lehungthinh02/KLTN_Data/Flowchart/KLTN_Data Diagram.png

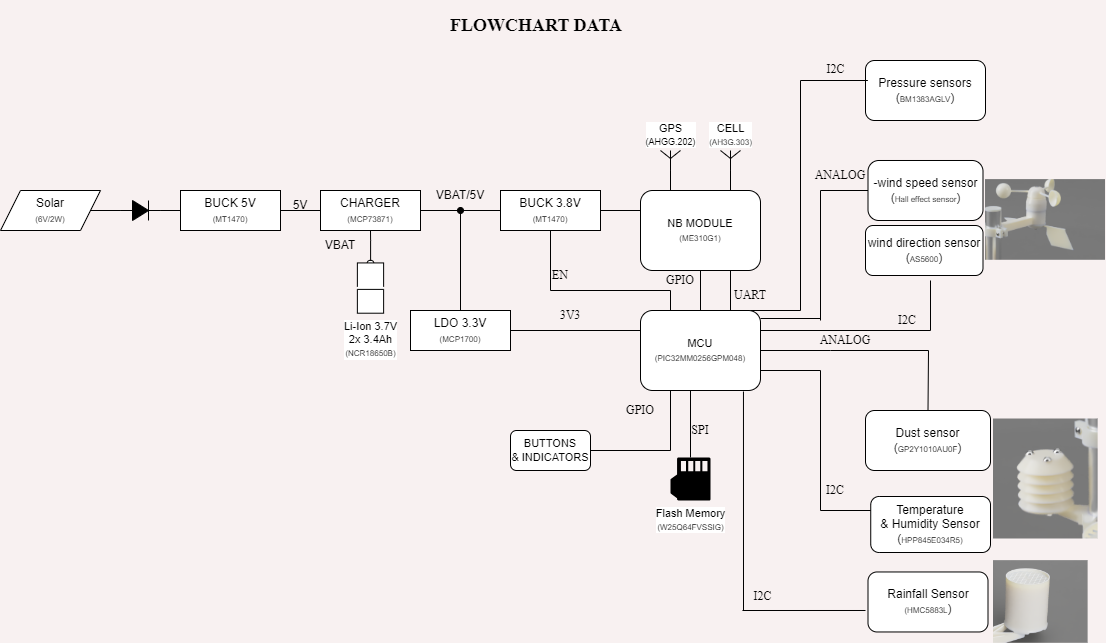
Flowchart/KLTN_Data Diagram.png
