lehungthinh02/KLTN_Data/Hardware/KiCADLib/FootprintConfig.png

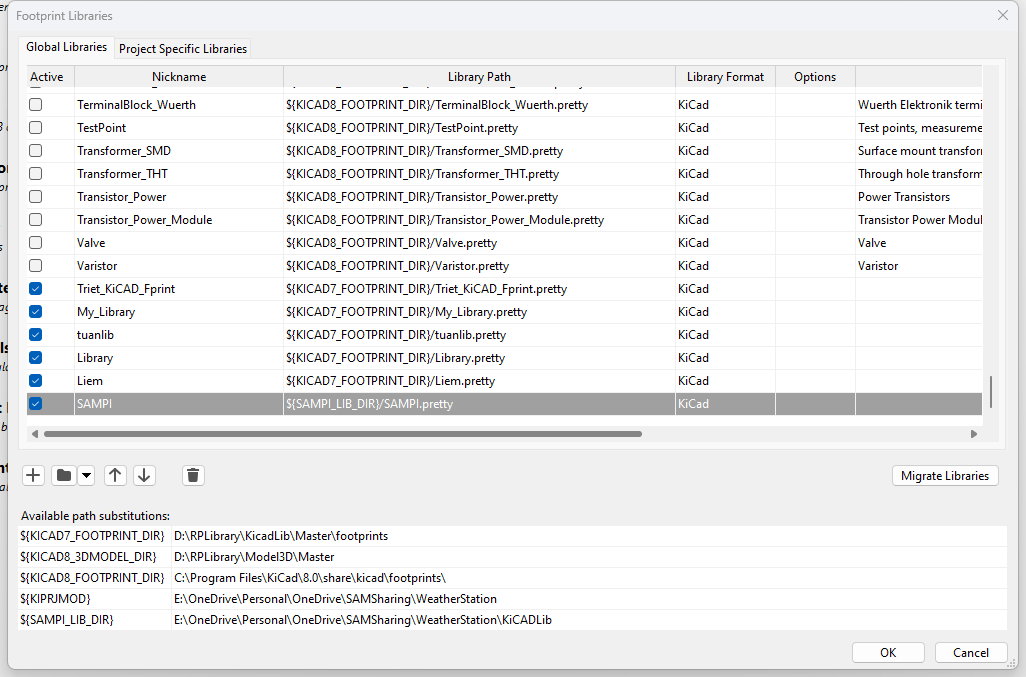
Hardware/KiCADLib/FootprintConfig.png
