lehungthinh02/KLTN_Data/Hardware/KiCADLib/PathConfig.png

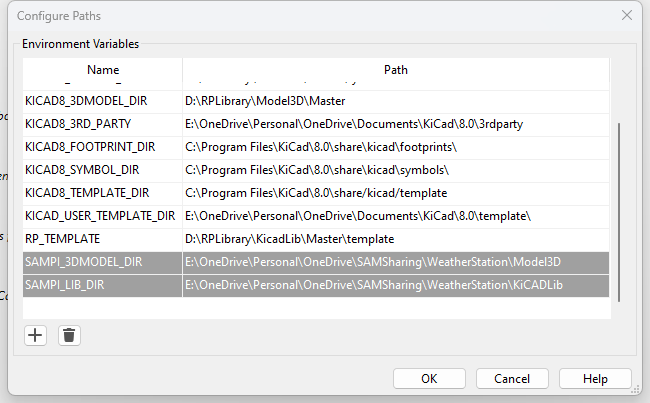
Hardware/KiCADLib/PathConfig.png
