lehungthinh02/KLTN_Data/Hardware/KiCADLib/SymbolConfig.png

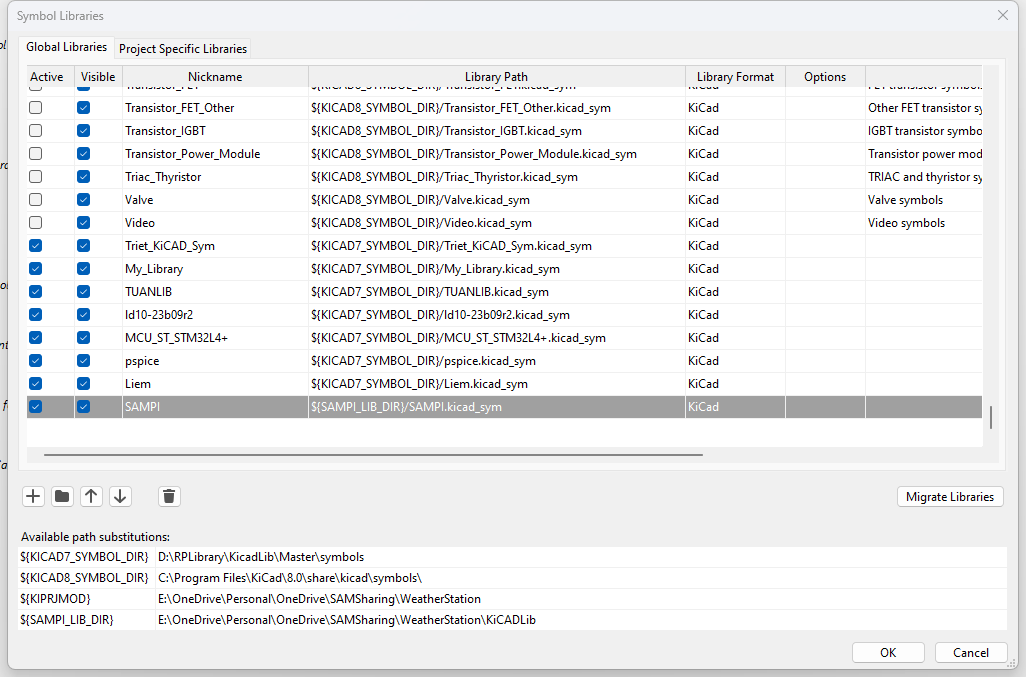
Hardware/KiCADLib/SymbolConfig.png
