lehungthinh02/KLTN_Data/Hardware/Enclosure/files/Anemo_top_-_Cap.stl

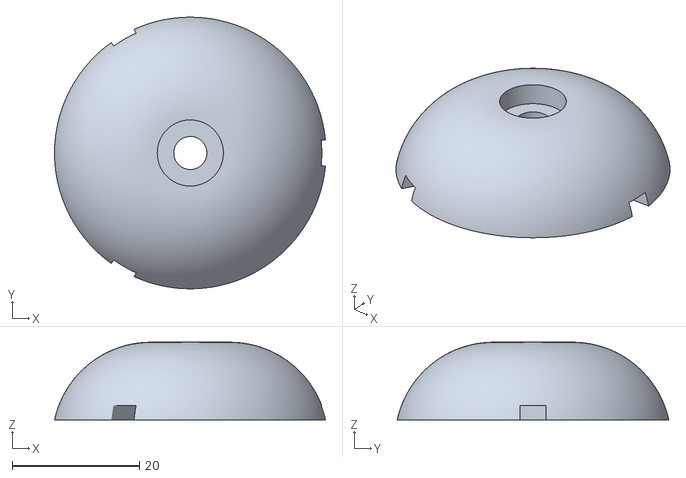
[picture p27: CAD file, 2024-04-03]
Hardware/Enclosure/files/Anemo_top_-_Cap.stl
42.6 x 42.7 x 12.2
