lehungthinh02/KLTN_Data/Hardware/Model3D/0612R.step

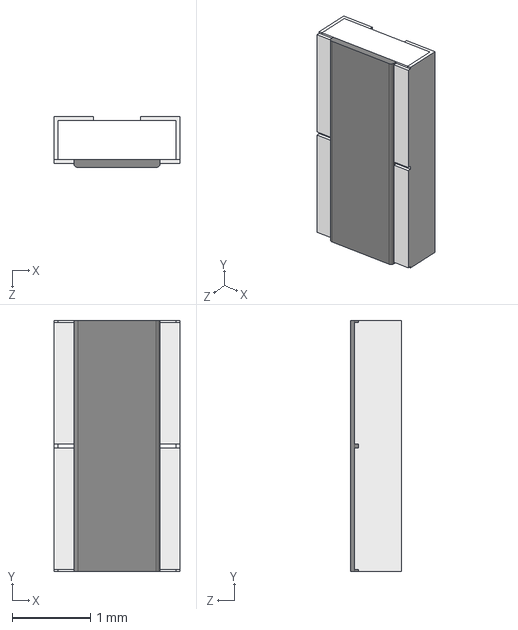
[picture p28: CAD file, 2024-04-12]
Hardware/Model3D/0612R.step
1.60 x 3.20 x 0.65 mm
