lehungthinh02/KLTN_Data/Hardware/Enclosure/files/Anemo_top_-_Wind_bowl.stl

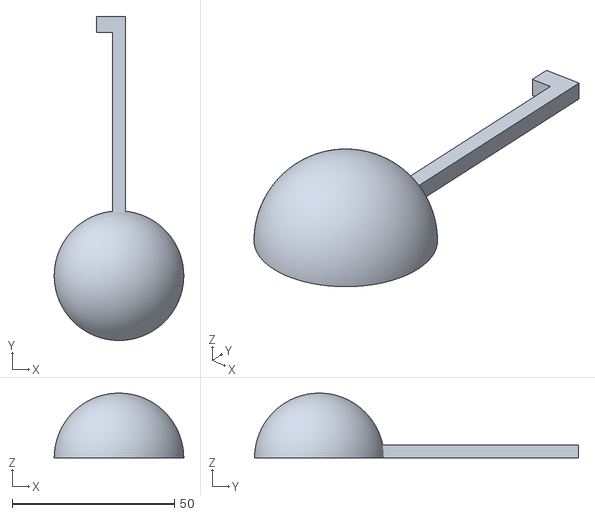
[picture p29: CAD file, 2024-04-03]
Hardware/Enclosure/files/Anemo_top_-_Wind_bowl.stl
40.0 x 100.0 x 20.0
