lehungthinh02/KLTN_Data/Hardware/Model3D/115v-ad00_c_1.stp

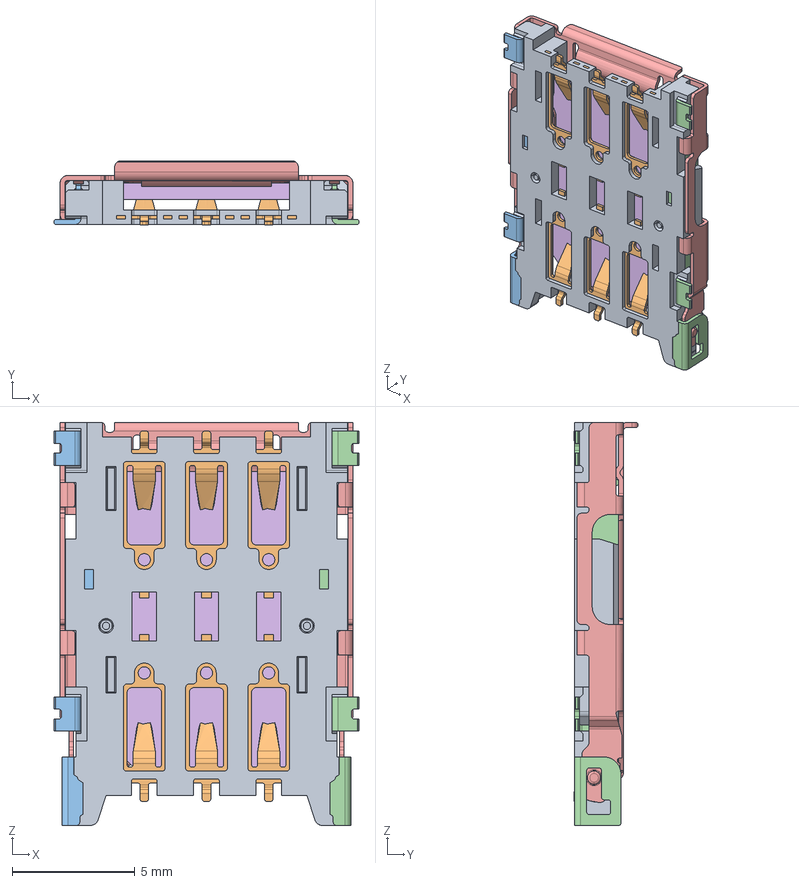
[picture p30: CAD file, 2024-04-12]
Hardware/Model3D/115v-ad00_c_1.stp
12.4 x 2.62 x 16.4 mm
INSULATOR
MICRO_SIM_CONTACT_01_19 x 3
MICRO_SIM_CONTACT_01_MIR_15 x 3
GROUND-LEFT
GROUND-RIGHT
NANO_SIM_CARD_2
