lehungthinh02/KLTN_Data/Hardware/Enclosure/files/Pluvio_sensor_Hub.stl

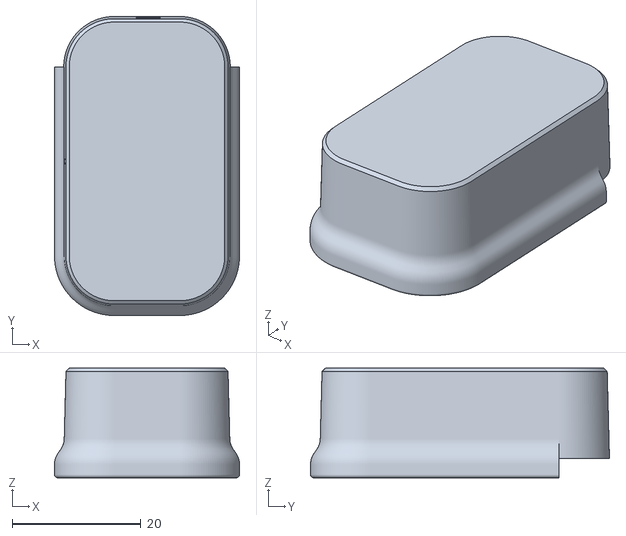
[picture p31: CAD file, 2024-04-03]
Hardware/Enclosure/files/Pluvio_sensor_Hub.stl
28.7 x 46.4 x 17.0
