lehungthinh02/KLTN_Data/Hardware/Model3D/EKMQ401VSN561MA40S.step

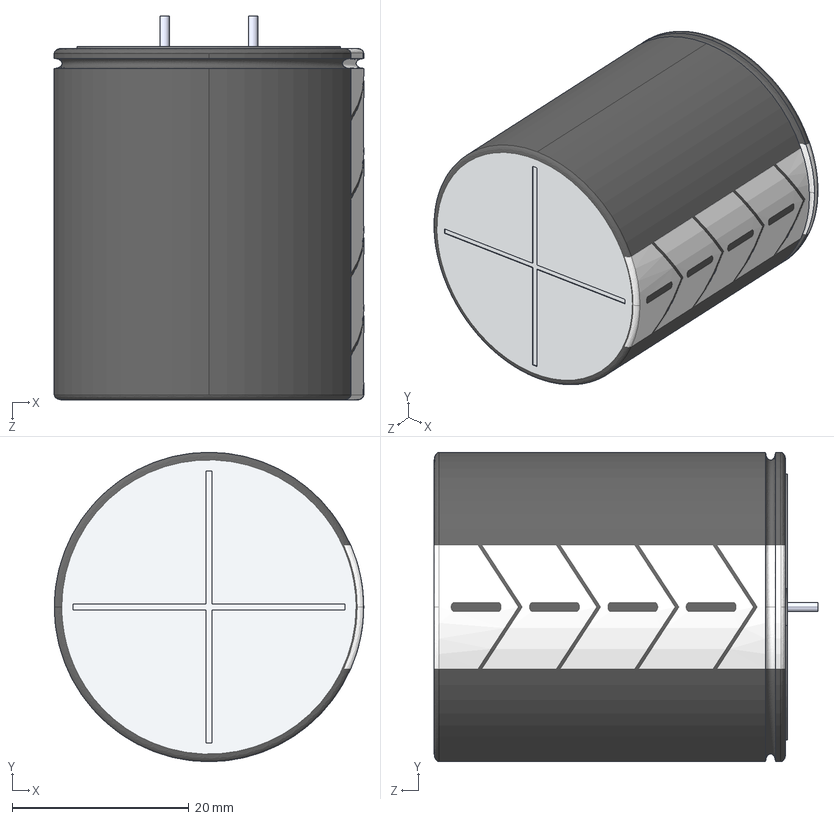
[picture p32: CAD file, 2024-04-12]
Hardware/Model3D/EKMQ401VSN561MA40S.step
35.0 x 35.0 x 43.4 mm
