lehungthinh02/KLTN_Data/Hardware/Enclosure/files/Anemo_Backpole.stl

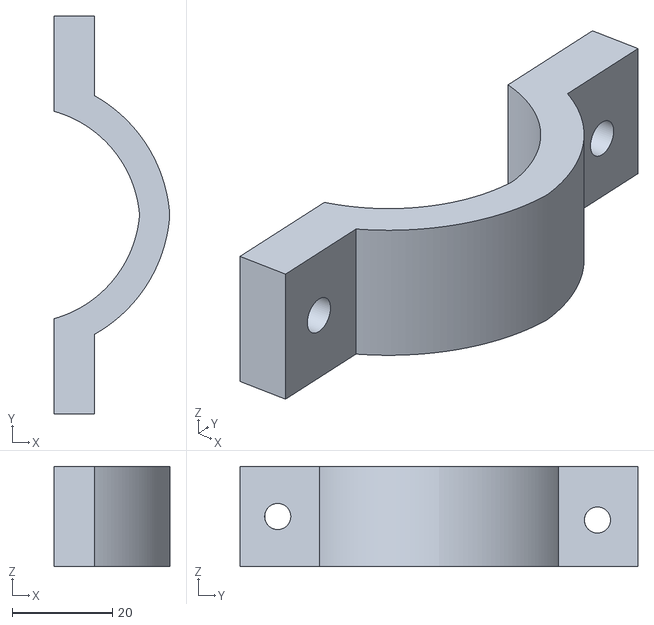
[picture p33: CAD file, 2024-04-03]
Hardware/Enclosure/files/Anemo_Backpole.stl
23.0 x 79.3 x 20.0
