lehungthinh02/KLTN_Data/Hardware/Model3D/C15DBAN.STEP

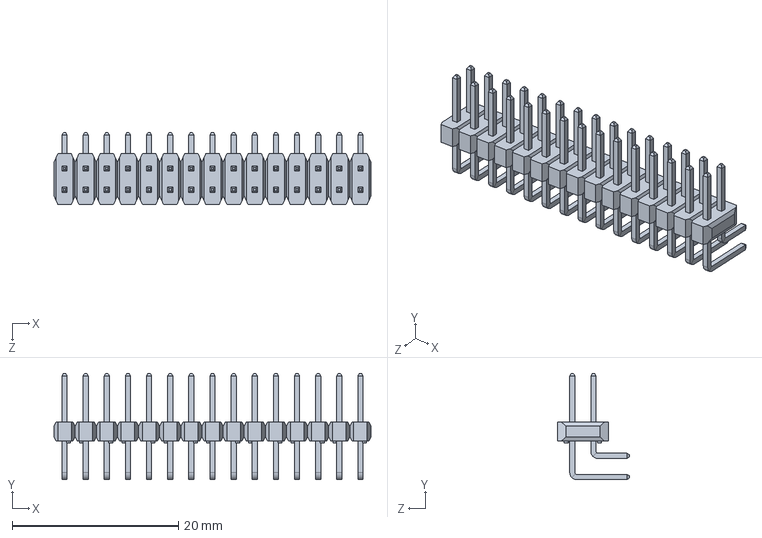
[picture p34: CAD file, 2024-04-12]
Hardware/Model3D/C15DBAN.STEP
38.1 x 12.8 x 8.64 mm
