lehungthinh02/KLTN_Data/Hardware/Enclosure/files/SH-First.stl

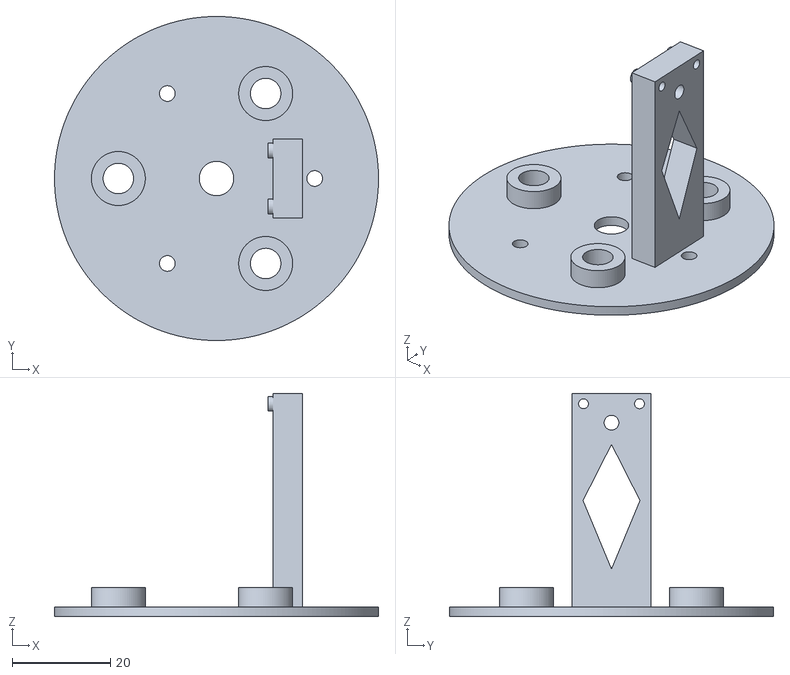
[picture p35: CAD file, 2024-04-03]
Hardware/Enclosure/files/SH-First.stl
66.0 x 66.0 x 45.5
