lehungthinh02/KLTN_Data/Hardware/Model3D/RES0603.STEP

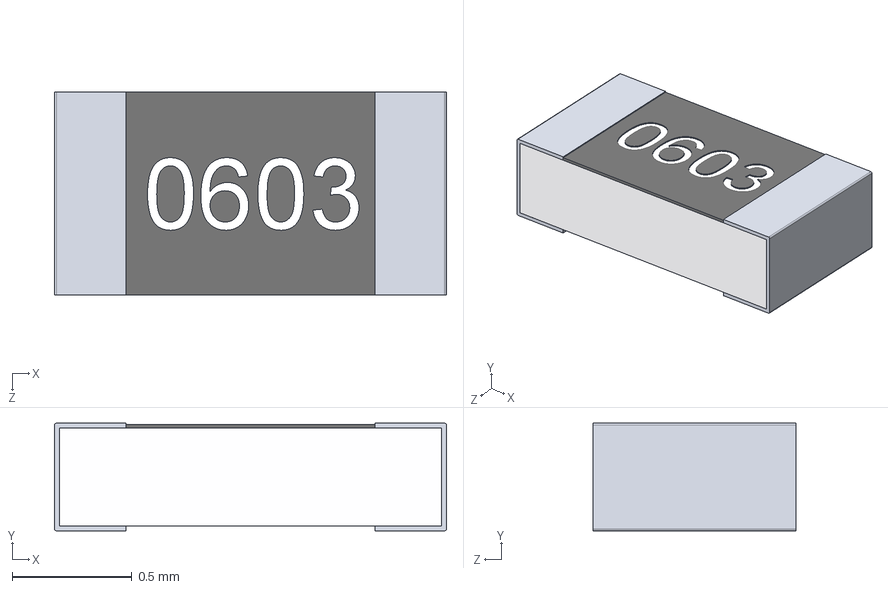
[picture p36: CAD file, 2024-04-12]
Hardware/Model3D/RES0603.STEP
1.64 x 0.45 x 0.85 mm
User Library-R SMD 0603_0603 BODY
User Library-R SMD 0603_0603 PAD x 2
User Library-R SMD 0603_0603 OPIS
