lehungthinh02/KLTN_Data/Hardware/Enclosure/files/Anemo_bottom-Base.stl

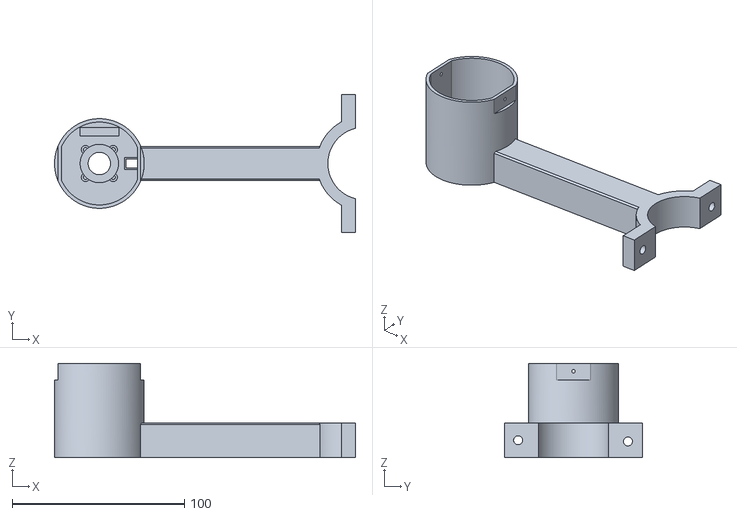
[picture p37: CAD file, 2024-04-03]
Hardware/Enclosure/files/Anemo_bottom-Base.stl
174.5 x 80.0 x 54.5
