lehungthinh02/KLTN_Data/Hardware/Model3D/1210C.step

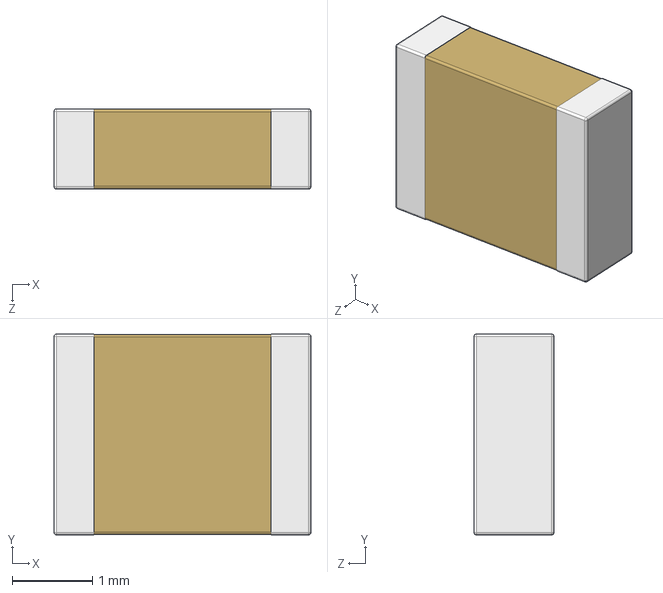
[picture p38: CAD file, 2024-04-12]
Hardware/Model3D/1210C.step
3.20 x 2.50 x 1.00 mm
