lehungthinh02/KLTN_Data/Hardware/Enclosure/files/Pluvio_Case.stl

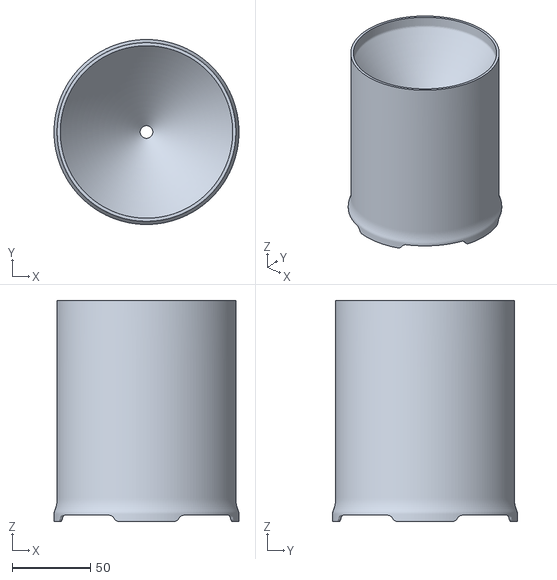
[picture p39: CAD file, 2024-04-03]
Hardware/Enclosure/files/Pluvio_Case.stl
118.0 x 118.0 x 141.0
