lehungthinh02/KLTN_Data/Hardware/Model3D/DF30FC-24DS-0.4V(82).stp

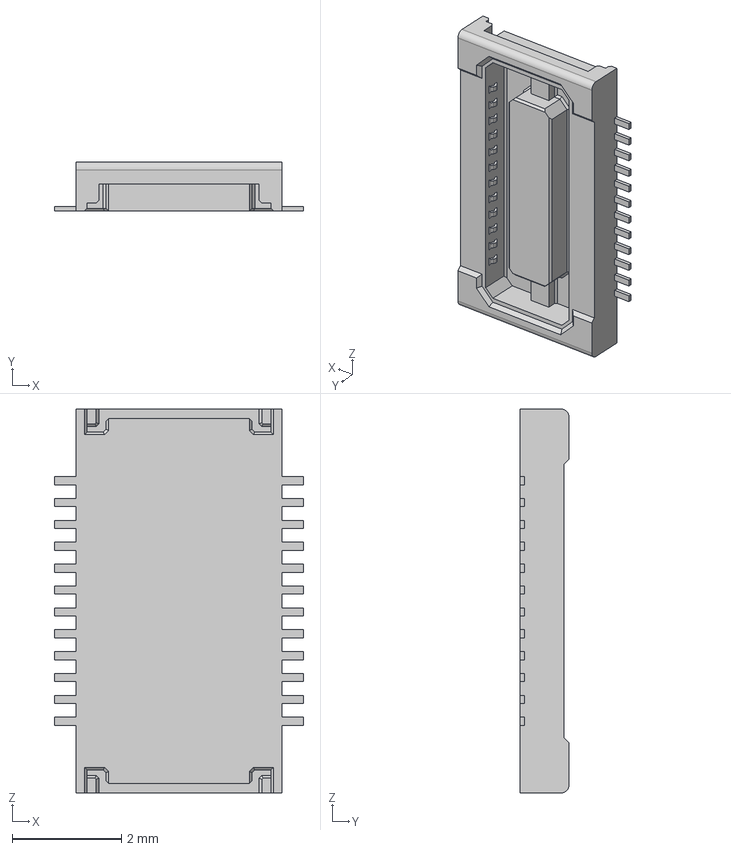
[picture p40: CAD file, 2024-04-12]
Hardware/Model3D/DF30FC-24DS-0.4V(82).stp
4.56 x 0.9 x 7.02 mm
