lehungthinh02/KLTN_Data/Hardware/Enclosure/files/SH-DHT_holder.stl

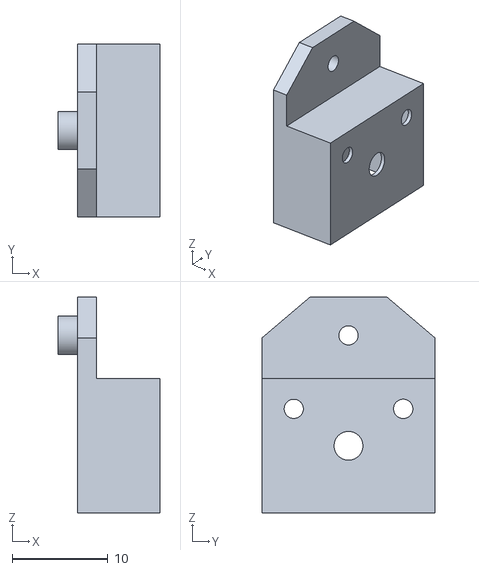
[picture p41: CAD file, 2024-04-03]
Hardware/Enclosure/files/SH-DHT_holder.stl
10.6 x 18.0 x 22.5
