lehungthinh02/KLTN_Data/Hardware/Model3D/C0603C104K4RACTU.step

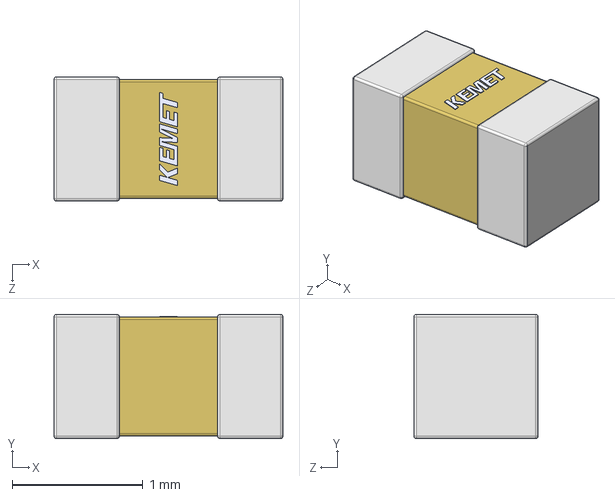
[picture p42: CAD file, 2024-04-12]
Hardware/Model3D/C0603C104K4RACTU.step
1.75 x 0.95 x 0.95 mm
