lehungthinh02/KLTN_Data/Hardware/Model3D/CONN 2M 22035025.stp

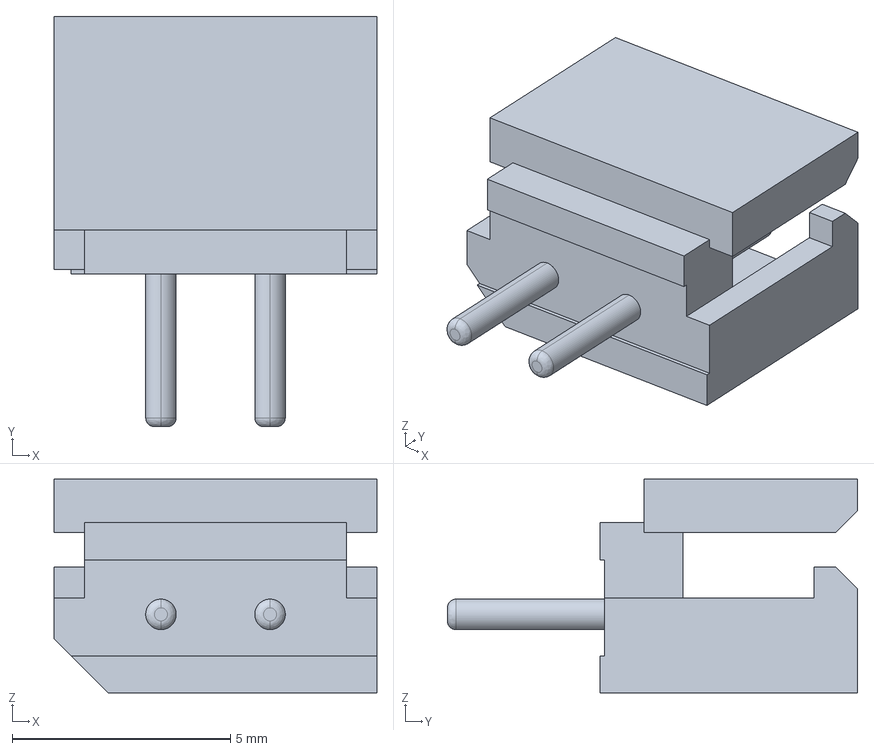
[picture p43: CAD file, 2024-04-12]
Hardware/Model3D/CONN 2M 22035025.stp
7.40 x 9.40 x 4.90 mm
