lehungthinh02/KLTN_Data/Hardware/Enclosure/files/Sensor_Hub_Backpole.stl

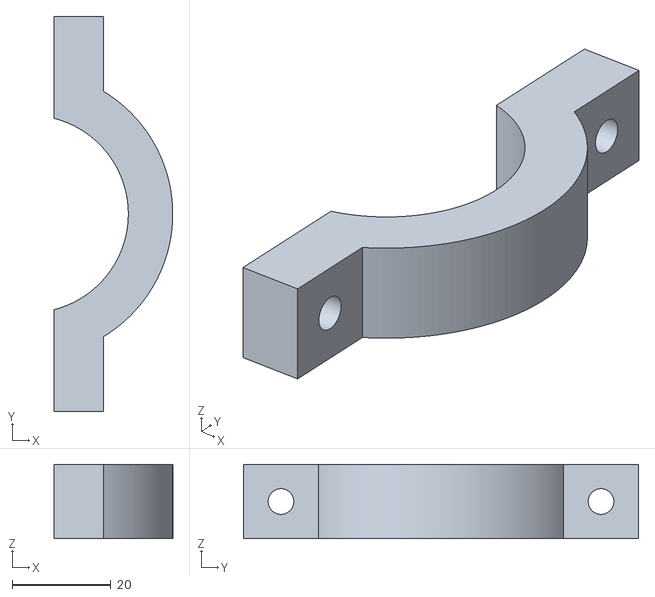
[picture p44: CAD file, 2024-04-03]
Hardware/Enclosure/files/Sensor_Hub_Backpole.stl
24.0 x 80.0 x 15.0
