lehungthinh02/KLTN_Data/Hardware/Model3D/SOP65P640X120-8N.step

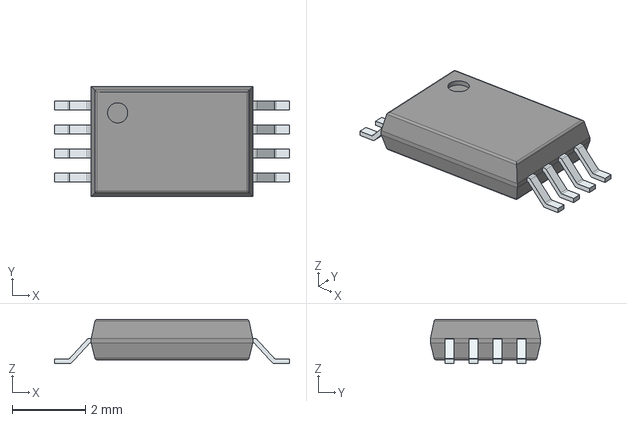
[picture p45: CAD file, 2024-04-12]
Hardware/Model3D/SOP65P640X120-8N.step
6.40 x 3.00 x 1.20 mm
PinsArrayLR
