lehungthinh02/KLTN_Data/Hardware/Enclosure/files/Pluvio-Backpole_V2.stl

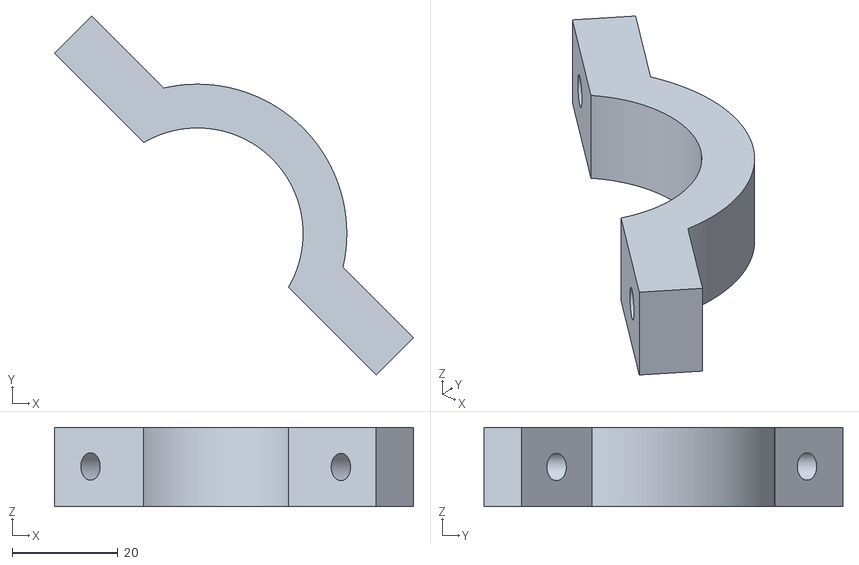
[picture p46: CAD file, 2024-04-03]
Hardware/Enclosure/files/Pluvio-Backpole_V2.stl
68.0 x 68.0 x 15.0
