lehungthinh02/KLTN_Data/Hardware/Model3D/QFN50P400X400X80-25N-D.step

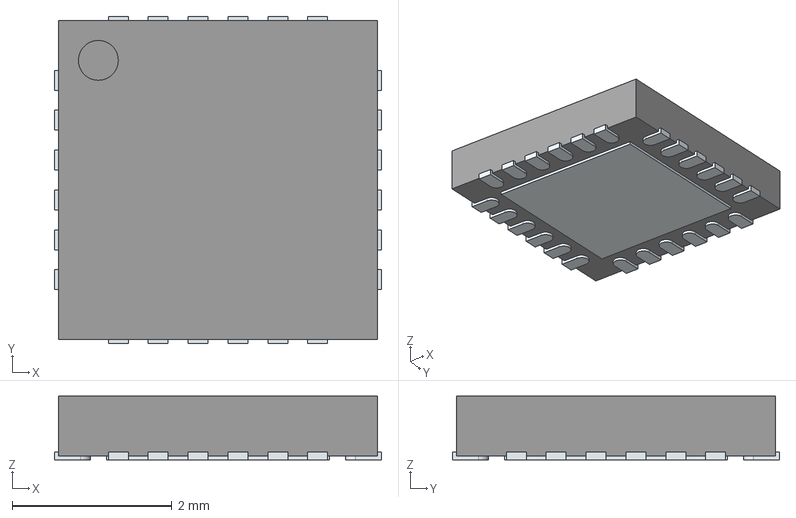
[picture p47: CAD file, 2024-04-12]
Hardware/Model3D/QFN50P400X400X80-25N-D.step
4.10 x 4.10 x 0.8 mm
ThermalPin
PinsArrayLR
PinsArrayTB
