lehungthinh02/KLTN_Data/Hardware/Enclosure/files/Sensor_Hub_Holder.stl

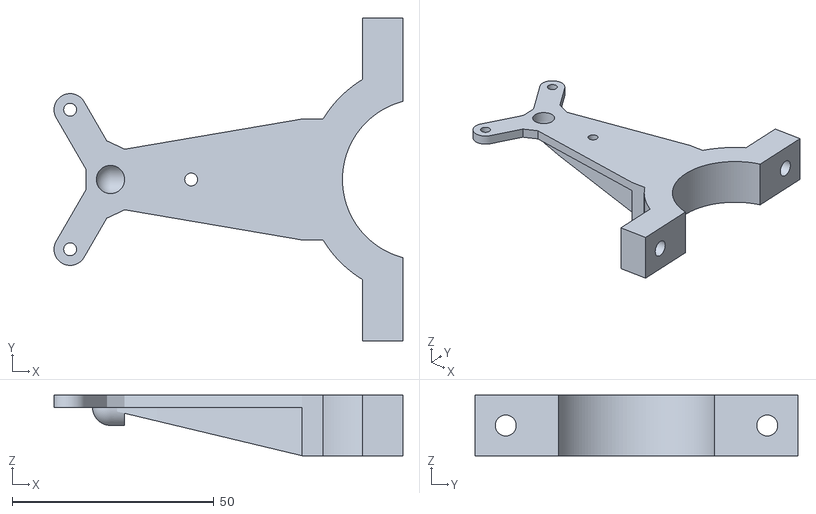
[picture p48: CAD file, 2024-04-03]
Hardware/Enclosure/files/Sensor_Hub_Holder.stl
86.5 x 80.0 x 15.0
