lehungthinh02/KLTN_Data/Hardware/Model3D/LED_0603_WS.STEP

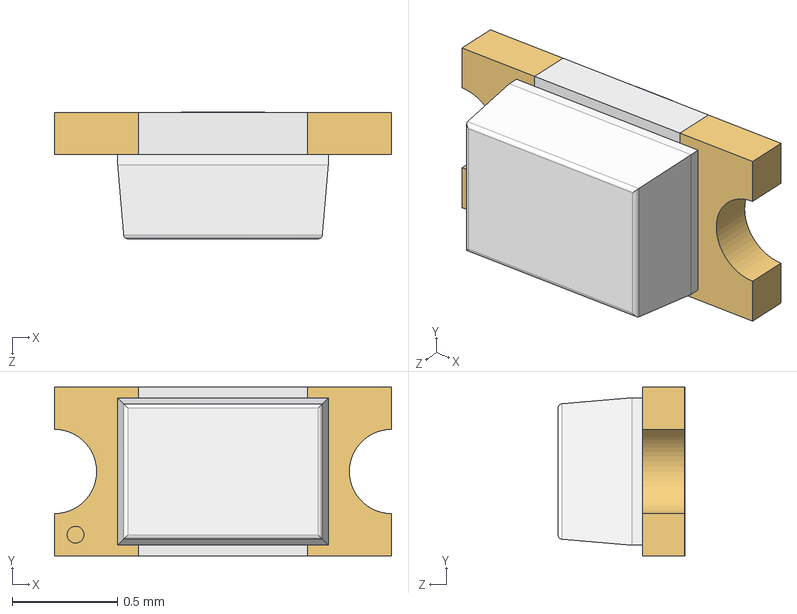
[picture p49: CAD file, 2024-04-12]
Hardware/Model3D/LED_0603_WS.STEP
1.60 x 0.8 x 0.602 mm
User Library-LED_0603_WS_Pocket002
User Library-LED_0603_WS_Pad004
User Library-LED_0603_WS_Fillet
User Library-LED_0603_WS_Pocket001
User Library-LED_0603_WS_Pad
