lehungthinh02/KLTN_Data/Hardware/Enclosure/files/Anemo_bottom-Low_cap_FIXED.stl

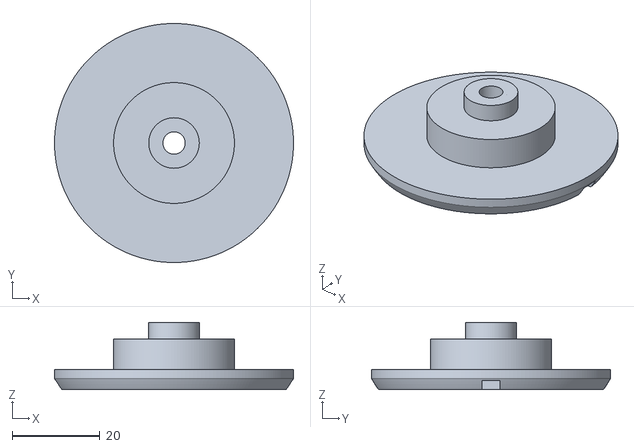
[picture p50: CAD file, 2024-04-03]
Hardware/Enclosure/files/Anemo_bottom-Low_cap_FIXED.stl
54.4 x 54.4 x 15.4
