lehungthinh02/KLTN_Data/Hardware/Model3D/mps_mag_4600.STEP

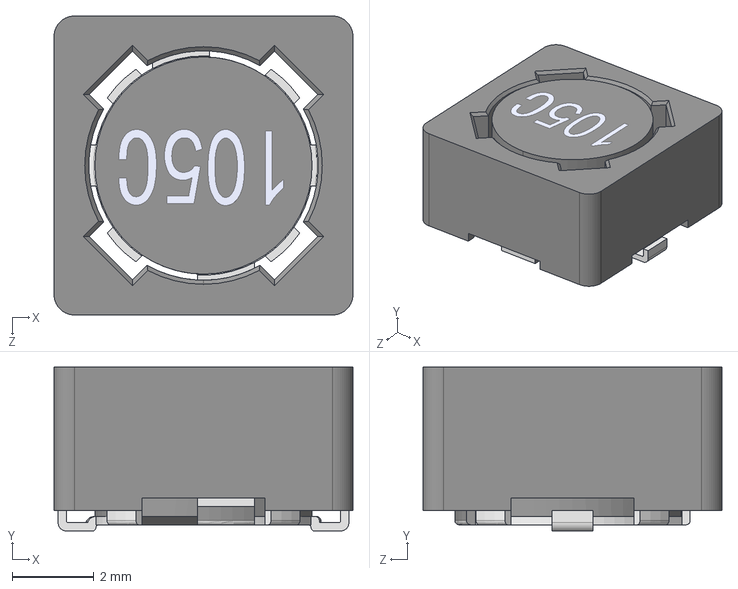
[picture p51: CAD file, 2024-04-12]
Hardware/Model3D/mps_mag_4600.STEP
7.30 x 4.00 x 7.30 mm
