lehungthinh02/KLTN_Data/Hardware/Enclosure/files/Pluvio_-_Base_FIXED.stl

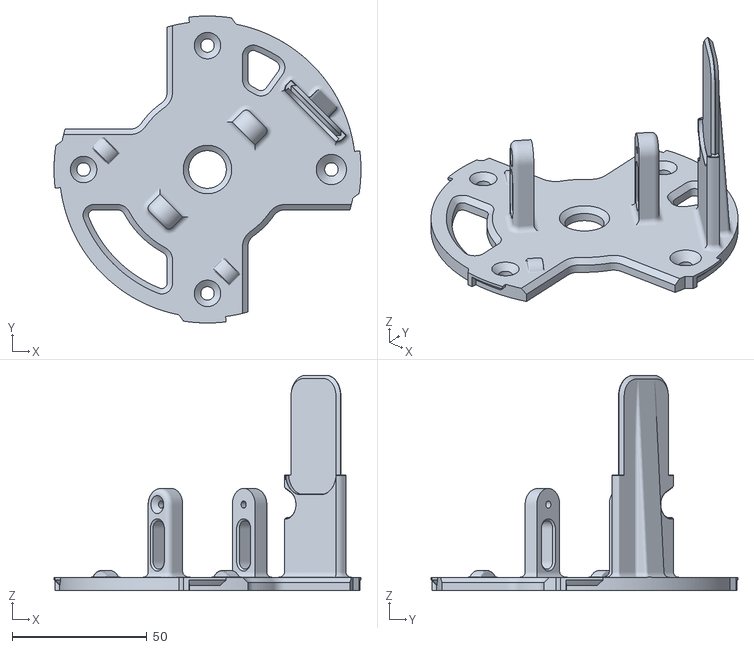
[picture p52: CAD file, 2024-04-03]
Hardware/Enclosure/files/Pluvio_-_Base_FIXED.stl
114.0 x 114.0 x 80.0
