lehungthinh02/KLTN_Data/Hardware/Model3D/A768MS477M1ELAE017.step

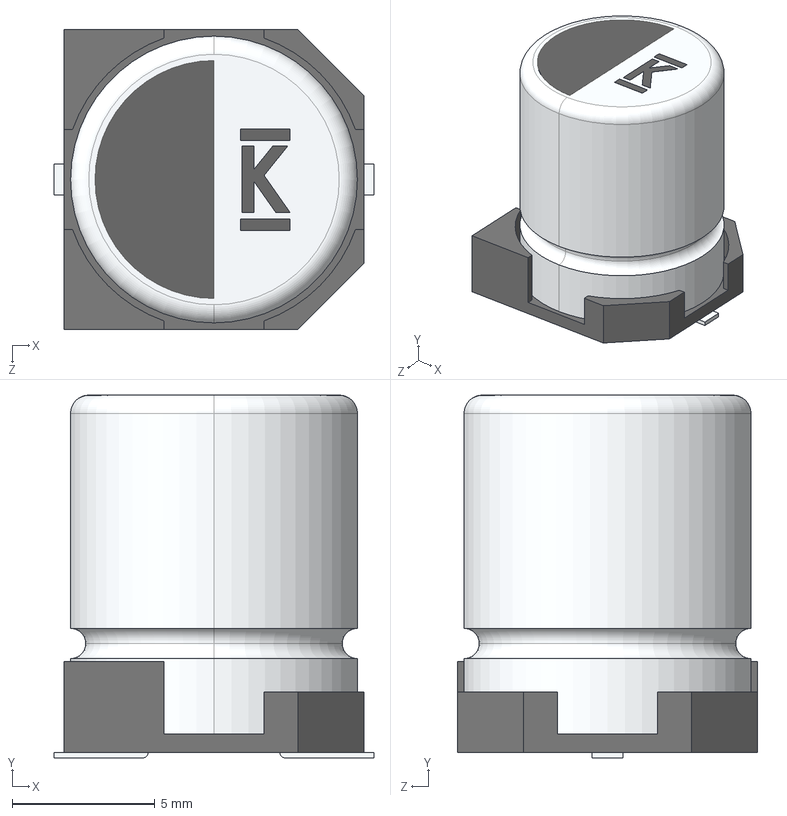
[picture p53: CAD file, 2024-04-12]
Hardware/Model3D/A768MS477M1ELAE017.step
11.2 x 12.7 x 10.5 mm
