lehungthinh02/KLTN_Data/Hardware/Enclosure/files/Sensor_Hub_Shield_top.stl

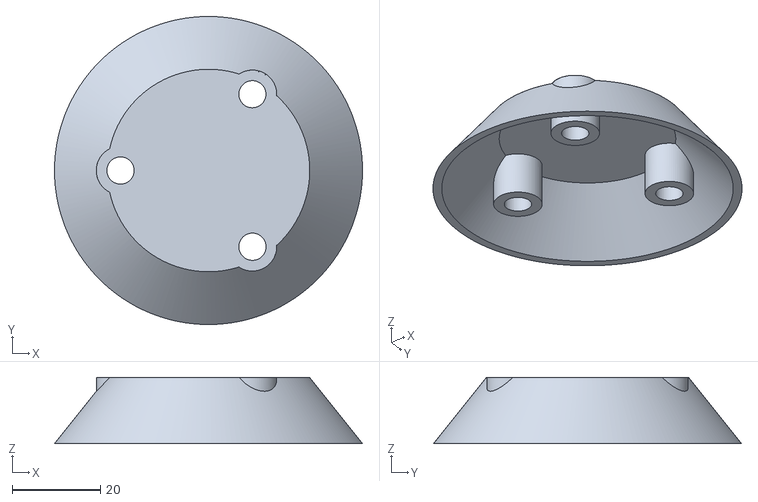
[picture p54: CAD file, 2024-04-03]
Hardware/Enclosure/files/Sensor_Hub_Shield_top.stl
70.0 x 70.0 x 15.0
