lehungthinh02/KLTN_Data/Hardware/Model3D/SCap_DGH155Q5R5_modified.STEP

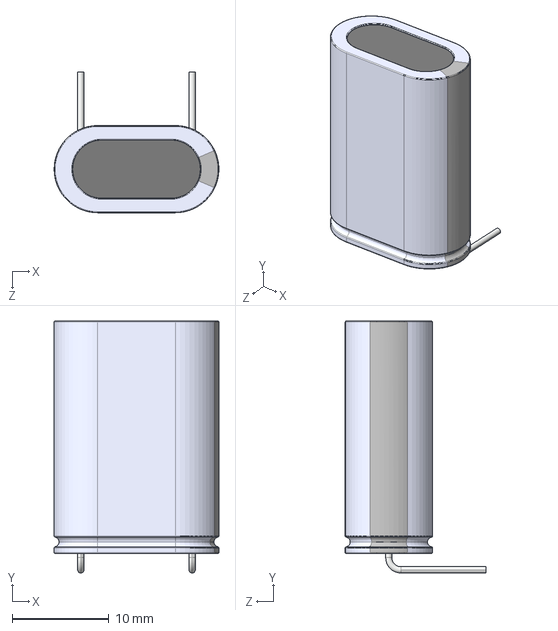
[picture p55: CAD file, 2024-04-12]
Hardware/Model3D/SCap_DGH155Q5R5_modified.STEP
17.0 x 26.0 x 14.5 mm
