lehungthinh02/KLTN_Data/Hardware/Model3D/DPS368.step

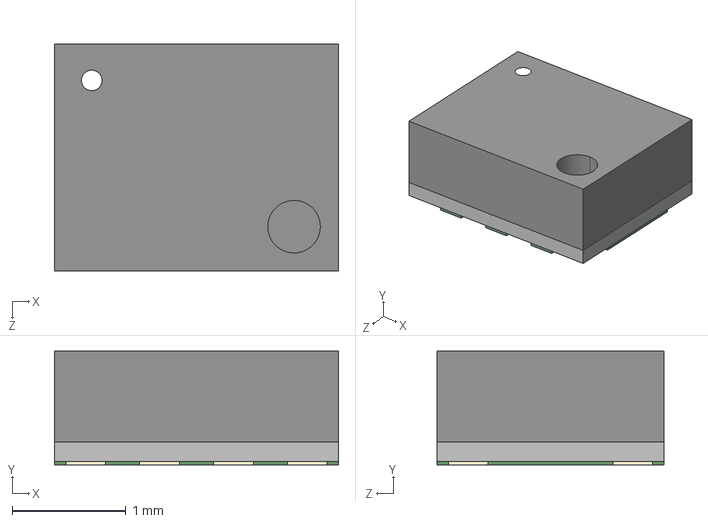
[picture p56: CAD file, 2024-04-12]
Hardware/Model3D/DPS368.step
2.50 x 1.00 x 2.00 mm
