lehungthinh02/KLTN_Data/Hardware/Enclosure/files/Pluvio_-_Tipping_bucket_FIXED.stl

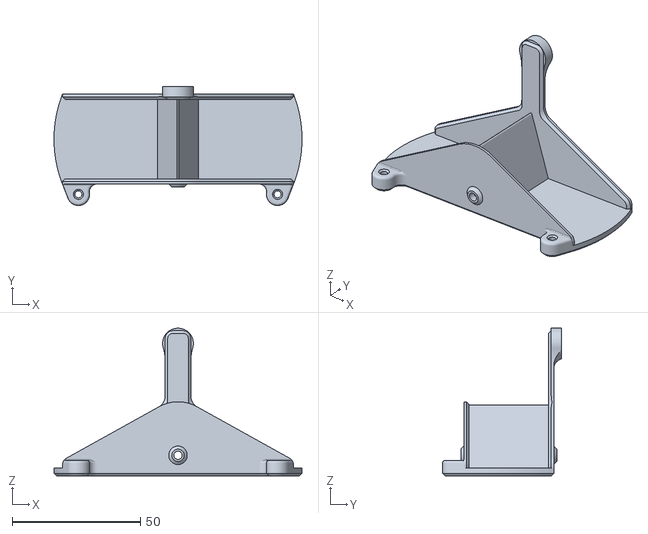
[picture p57: CAD file, 2024-04-03]
Hardware/Enclosure/files/Pluvio_-_Tipping_bucket_FIXED.stl
96.6 x 46.3 x 57.5
