lehungthinh02/KLTN_Data/Hardware/Model3D/QUECTEL L76.step

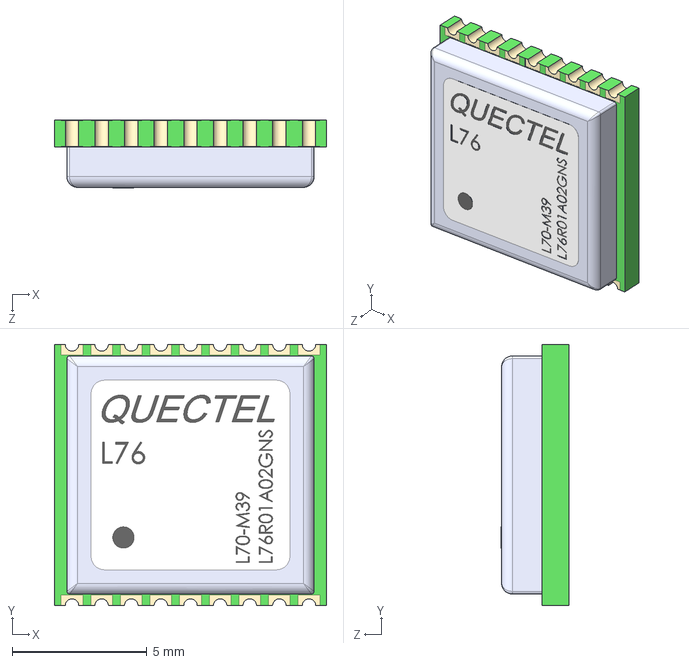
[picture p58: CAD file, 2024-04-12]
Hardware/Model3D/QUECTEL L76.step
10.1 x 9.70 x 2.52 mm
