lehungthinh02/KLTN_Data/Hardware/Enclosure/files/Anemo_bottom-High_cap_FIXED.stl

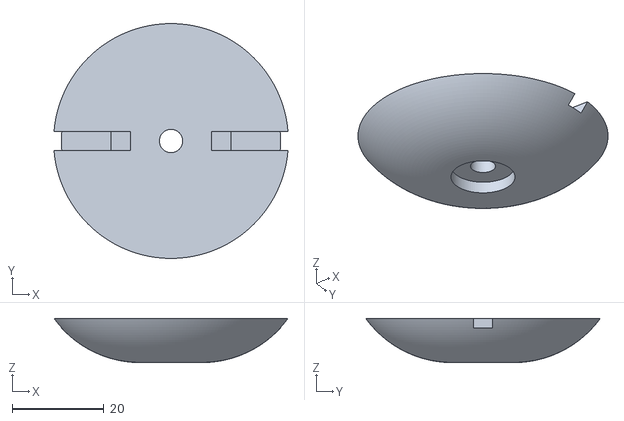
[picture p59: CAD file, 2024-04-03]
Hardware/Enclosure/files/Anemo_bottom-High_cap_FIXED.stl
51.0 x 51.2 x 9.64
