lehungthinh02/KLTN_Data/Hardware/Model3D/SOT65P210X110-6N.step

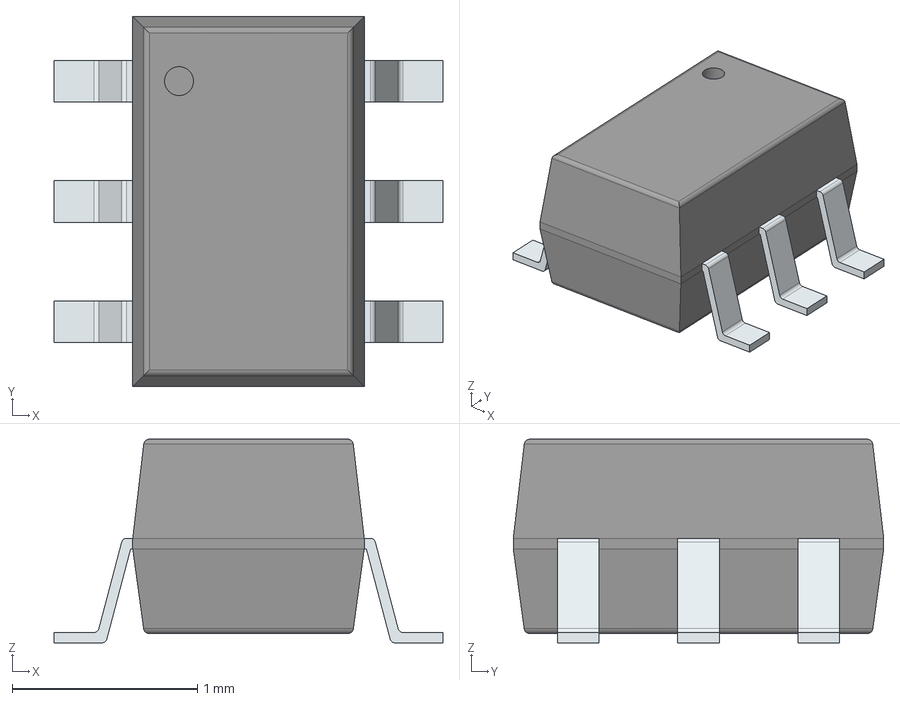
[picture p60: CAD file, 2024-04-12]
Hardware/Model3D/SOT65P210X110-6N.step
2.10 x 2.00 x 1.10 mm
PinsArrayLR
