lehungthinh02/KLTN_Data/Hardware/Model3D/mf-nsmf050.stp

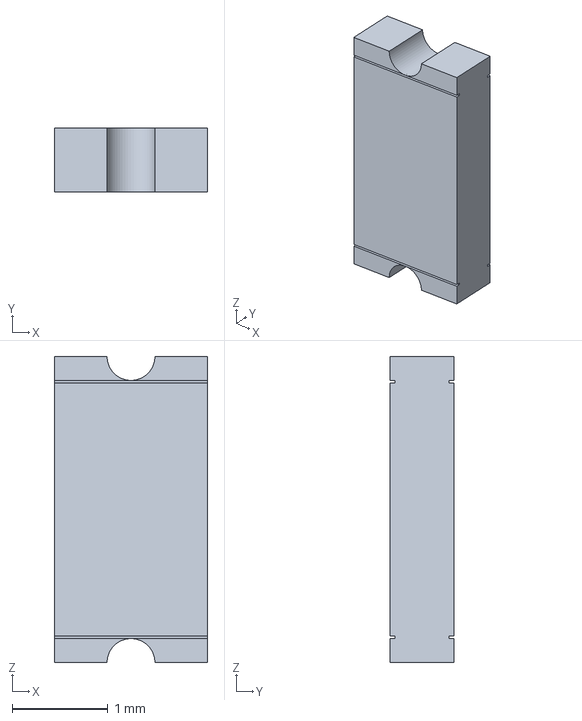
[picture p61: CAD file, 2024-04-12]
Hardware/Model3D/mf-nsmf050.stp
1.60 x 0.665 x 3.20 mm
