lehungthinh02/KLTN_Data/Hardware/Model3D/APTB1612.STEP

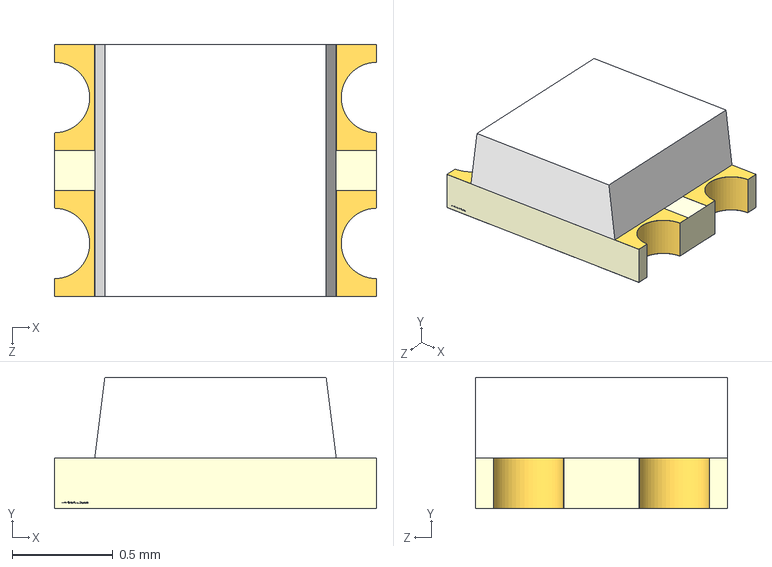
[picture p62: CAD file, 2024-04-12]
Hardware/Model3D/APTB1612.STEP
1.60 x 0.651 x 1.25 mm
