lehungthinh02/KLTN_Data/Hardware/Model3D/CI1104MXHR0-NH.STEP

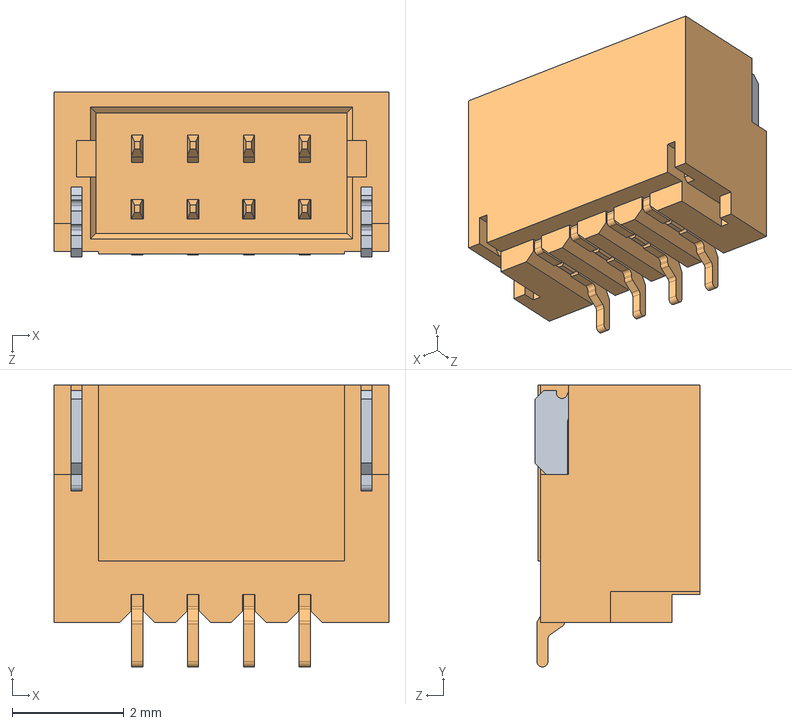
[picture p63: CAD file, 2024-04-12]
Hardware/Model3D/CI1104MXHR0-NH.STEP
6.00 x 5.05 x 2.95 mm
