lehungthinh02/KLTN_Data/Hardware/Model3D/SOT23-5L.step

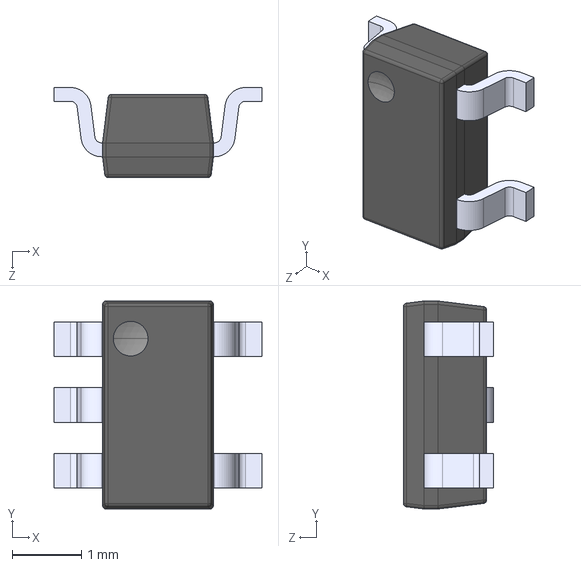
[picture p64: CAD file, 2024-04-12]
Hardware/Model3D/SOT23-5L.step
3.00 x 3.00 x 1.30 mm
