lehungthinh02/KLTN_Data/Hardware/Model3D/ZX60-B-5S.stp

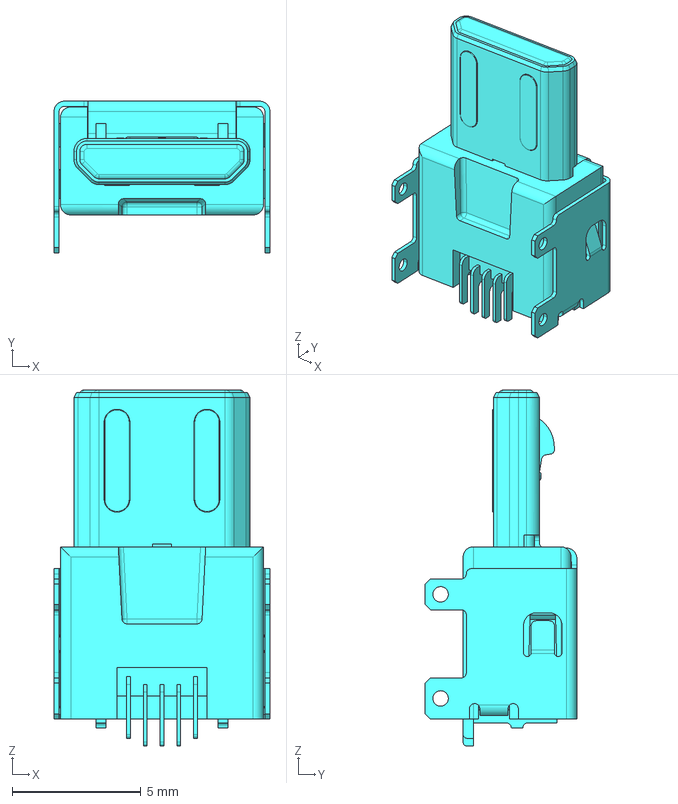
[picture p65: CAD file, 2024-04-12]
Hardware/Model3D/ZX60-B-5S.stp
8.40 x 5.90 x 13.9 mm
