lehungthinh02/KLTN_Data/Hardware/Model3D/CAP1206.step

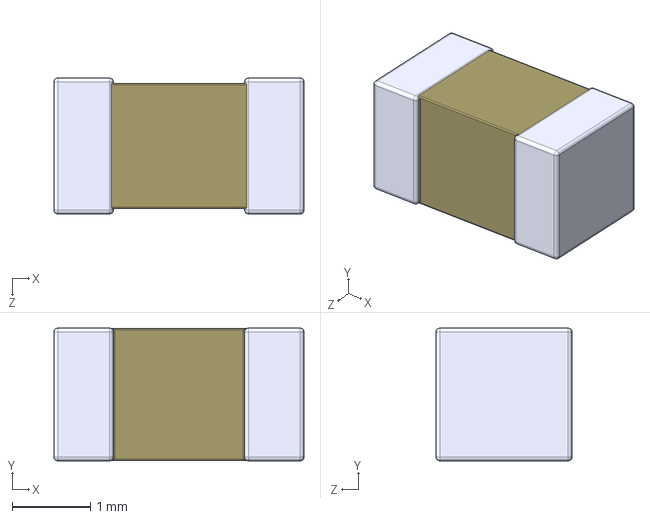
[picture p66: CAD file, 2024-04-12]
Hardware/Model3D/CAP1206.step
3.20 x 1.70 x 1.74 mm
