lehungthinh02/KLTN_Data/Hardware/Model3D/USB2512B-AEZG-TR.step

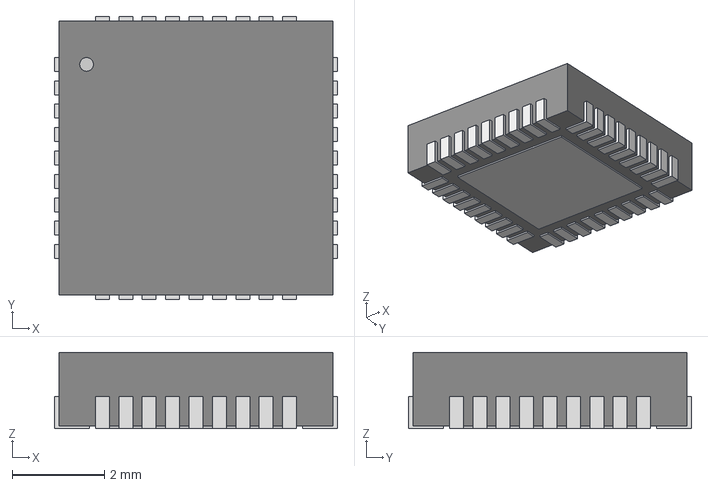
[picture p67: CAD file, 2024-04-12]
Hardware/Model3D/USB2512B-AEZG-TR.step
6.15 x 6.15 x 1.65 mm
