lehungthinh02/KLTN_Data/Hardware/Model3D/SSW-108-01-T-S.stp

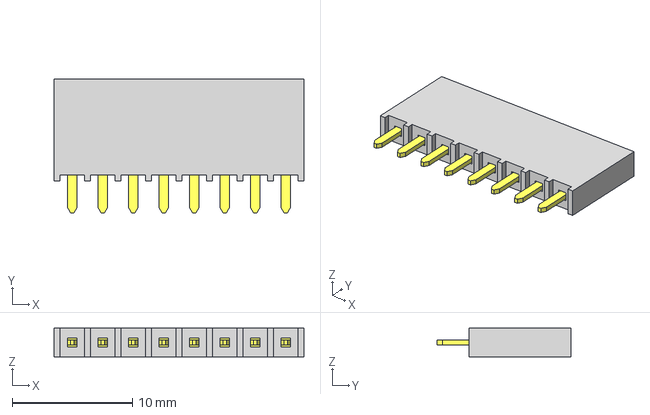
[picture p68: CAD file, 2024-04-12]
Hardware/Model3D/SSW-108-01-T-S.stp
20.8 x 11.2 x 2.41 mm
_T1SSW-108-01-T-S
_P2SSW-108-01-T-S
