lehungthinh02/KLTN_Data/Hardware/Model3D/SSW-120-01-T-D.stp

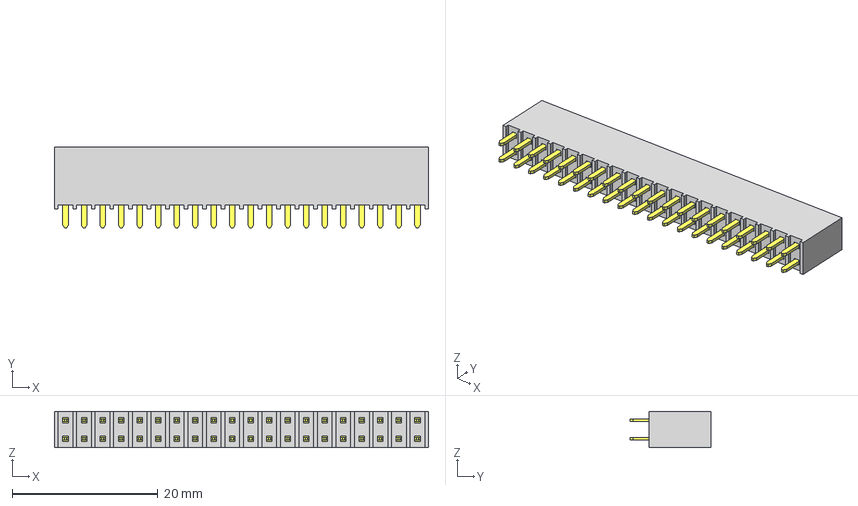
[picture p69: CAD file, 2024-04-12]
Hardware/Model3D/SSW-120-01-T-D.stp
51.3 x 11.2 x 4.95 mm
P2SSW-120-01-T-D
T1SSW-120-01-T-D
