lehungthinh02/KLTN_Data/Hardware/Model3D/Ferrite Bead 0603.STEP

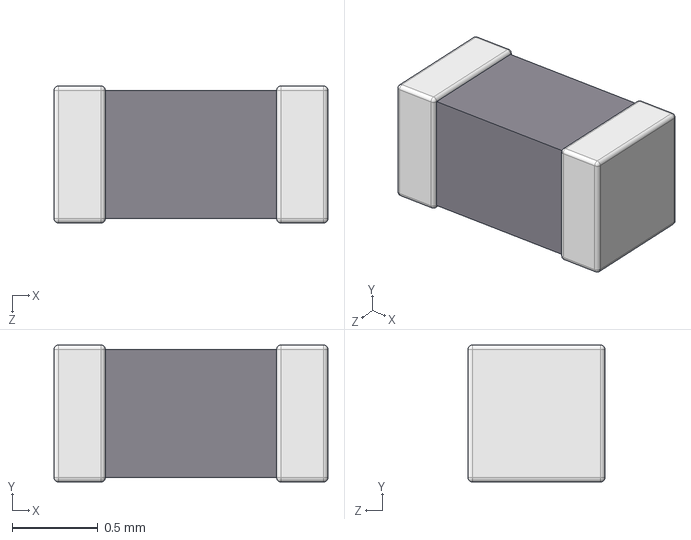
[picture p70: CAD file, 2024-04-12]
Hardware/Model3D/Ferrite Bead 0603.STEP
1.60 x 0.8 x 0.8 mm
User Library-FB_1608_Pad001
User Library-FB_1608_Cut
