lehungthinh02/KLTN_Data/Hardware/Model3D/SOT25_DIODES.step

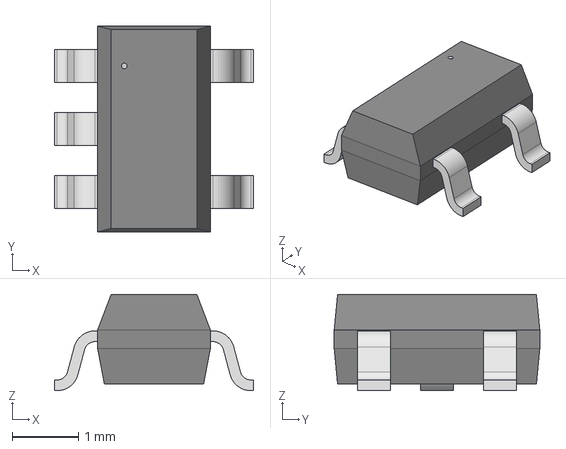
[picture p71: CAD file, 2024-04-12]
Hardware/Model3D/SOT25_DIODES.step
3.00 x 3.10 x 1.45 mm
