lehungthinh02/KLTN_Data/Hardware/Model3D/TO-220.step

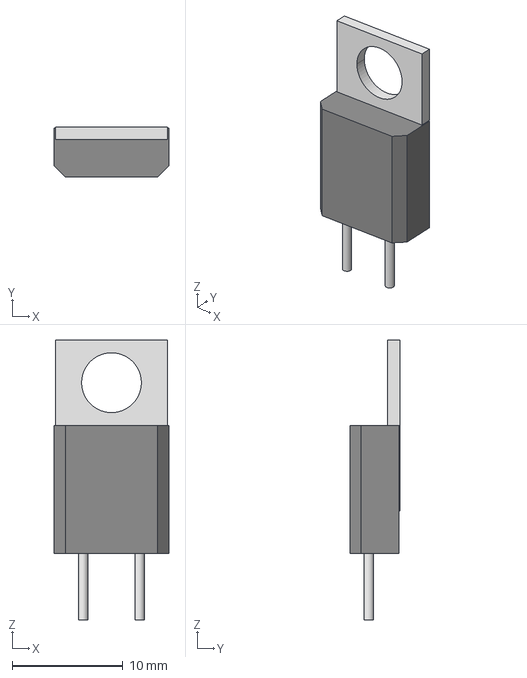
[picture p72: CAD file, 2024-04-12]
Hardware/Model3D/TO-220.step
10.3 x 4.55 x 25.2 mm
