lehungthinh02/KLTN_Data/Hardware/Model3D/SSW-109-02-G-D-RA.stp

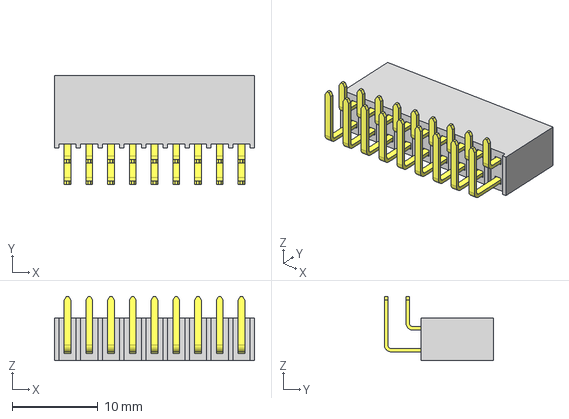
[picture p73: CAD file, 2024-04-12]
Hardware/Model3D/SSW-109-02-G-D-RA.stp
23.4 x 12.8 x 7.48 mm
P2SSW-109-02-G-D-RA
T1SSW-109-02-G-D-RA
