lehungthinh02/KLTN_Data/Hardware/Model3D/SOT23-6.step

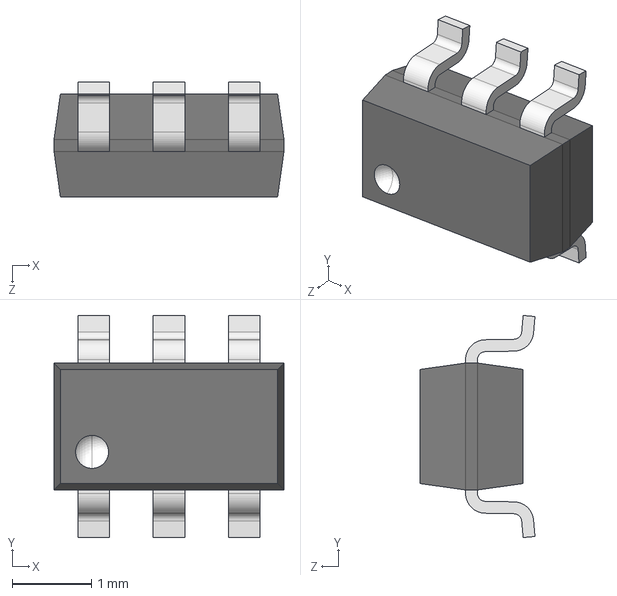
[picture p74: CAD file, 2024-04-12]
Hardware/Model3D/SOT23-6.step
2.90 x 2.80 x 1.45 mm
