lehungthinh02/KLTN_Data/Hardware/Model3D/HDM-TH-1x26x2.54R.STEP

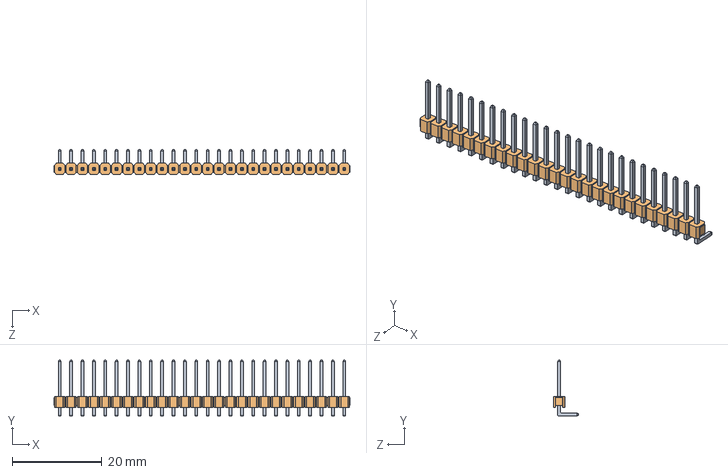
[picture p75: CAD file, 2024-04-12]
Hardware/Model3D/HDM-TH-1x26x2.54R.STEP
66.0 x 12.4 x 5.59 mm
