lehungthinh02/KLTN_Data/Hardware/Model3D/SOT-563.step

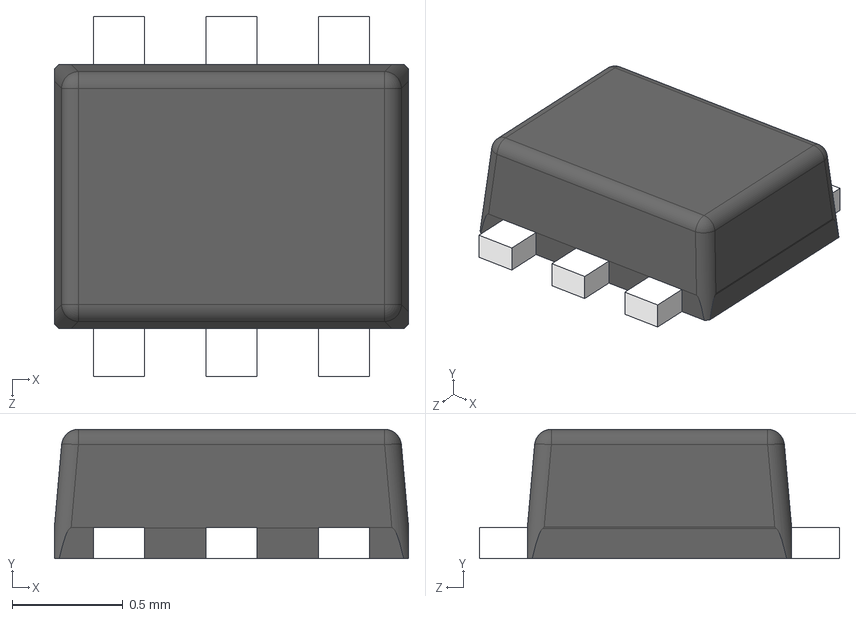
[picture p77: CAD file, 2024-04-12]
Hardware/Model3D/SOT-563.step
1.60 x 0.584 x 1.63 mm
