lehungthinh02/KLTN_Data/Hardware/Model3D/SC70-6.step

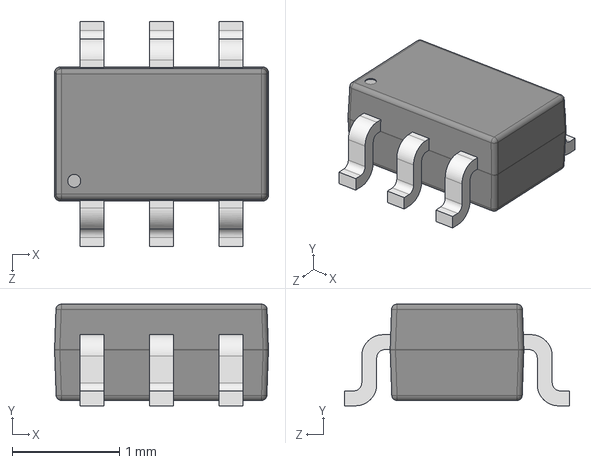
[picture p78: CAD file, 2024-04-12]
Hardware/Model3D/SC70-6.step
2.00 x 0.95 x 2.10 mm
