lehungthinh02/KLTN_Data/Hardware/Model3D/SOT95P270X145-5N.step

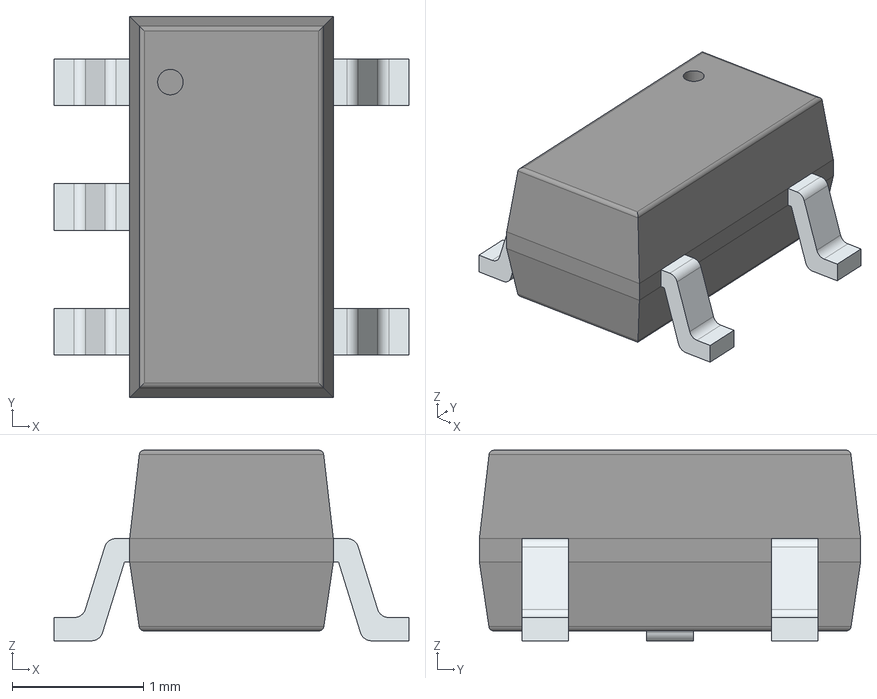
[picture p79: CAD file, 2024-04-12]
Hardware/Model3D/SOT95P270X145-5N.step
2.70 x 2.90 x 1.45 mm
PinsArrayL
PinsArrayR
