lehungthinh02/KLTN_Data/Hardware/Model3D/DF30RC-24DP-0.4V(82).stp

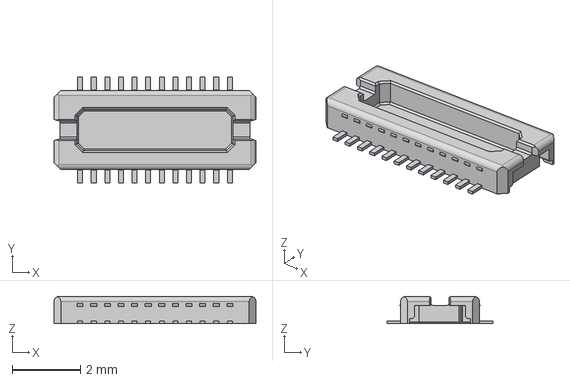
[picture p80: CAD file, 2024-04-12]
Hardware/Model3D/DF30RC-24DP-0.4V(82).stp
5.94 x 3.12 x 0.8 mm
