lehungthinh02/KLTN_Data/Hardware/Model3D/xE310.step

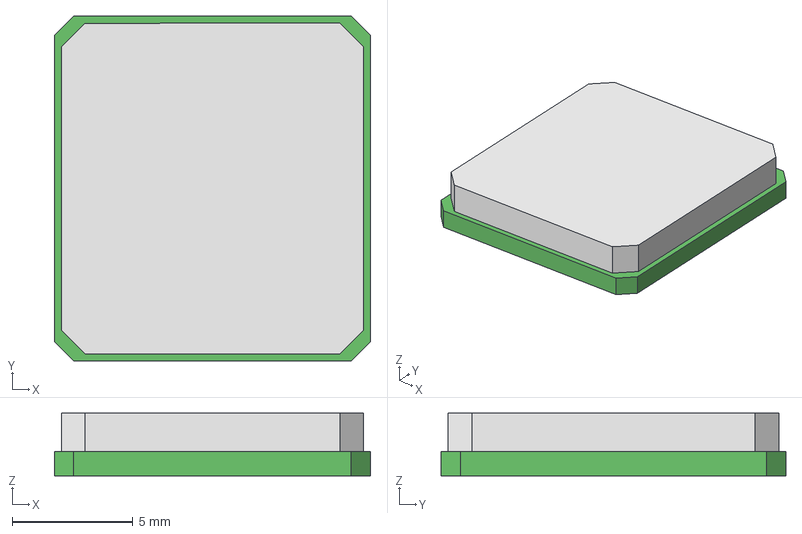
[picture p81: CAD file, 2024-04-12]
Hardware/Model3D/xE310.step
13.1 x 14.3 x 2.60 mm
Extruded
Extruded001
