lehungthinh02/KLTN_Data/Hardware/Model3D/SHU2512.step

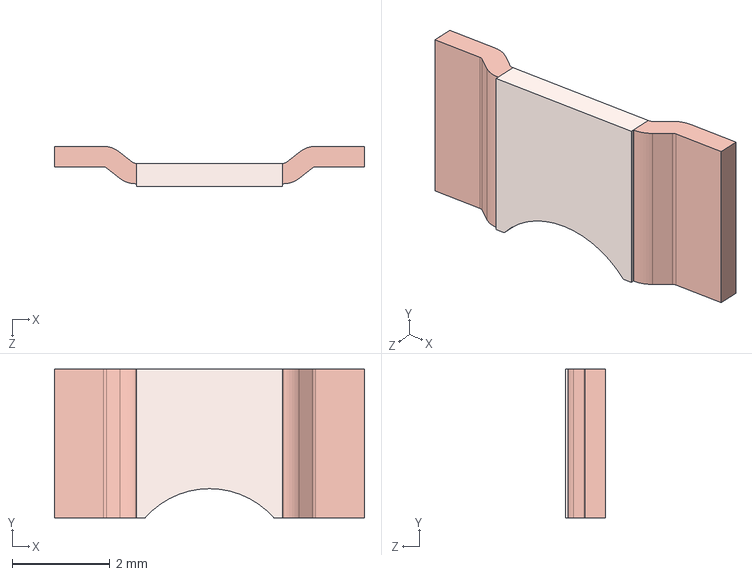
[picture p82: CAD file, 2024-04-12]
Hardware/Model3D/SHU2512.step
6.35 x 3.05 x 0.828 mm
