lehungthinh02/KLTN_Data/Hardware/Model3D/4x0402.stp

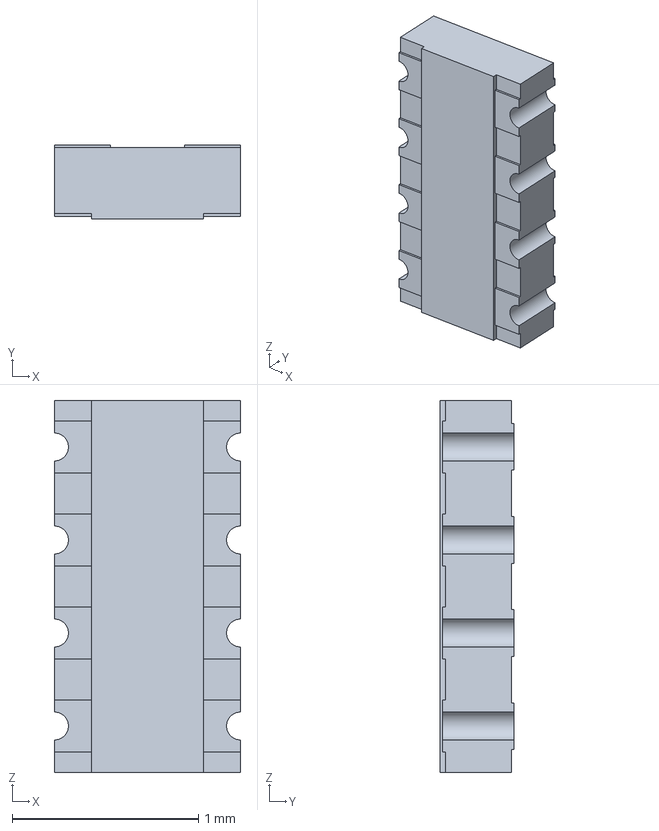
[picture p83: CAD file, 2024-04-12]
Hardware/Model3D/4x0402.stp
1.00 x 0.4 x 2.00 mm
