lehungthinh02/KLTN_Data/Hardware/Model3D/SOIC127P1032X265-16N.step

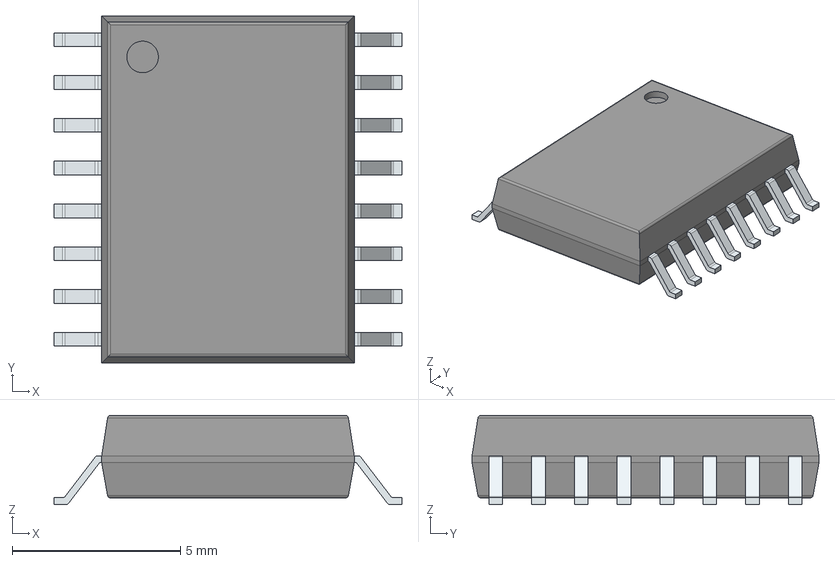
[picture p84: CAD file, 2024-04-12]
Hardware/Model3D/SOIC127P1032X265-16N.step
10.3 x 10.3 x 2.65 mm
PinsArrayLR
