lehungthinh02/KLTN_Data/Hardware/Model3D/SOT95P280X145-6N.step

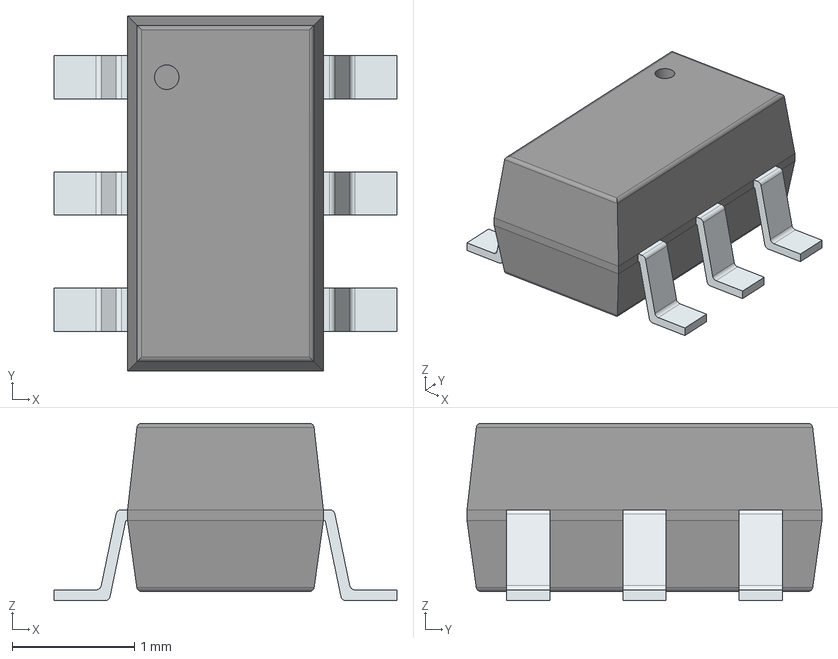
[picture p85: CAD file, 2024-04-12]
Hardware/Model3D/SOT95P280X145-6N.step
2.80 x 2.90 x 1.45 mm
PinsArrayLR
