lehungthinh02/KLTN_Data/Hardware/Model3D/SOIC127P600X150-9N.step

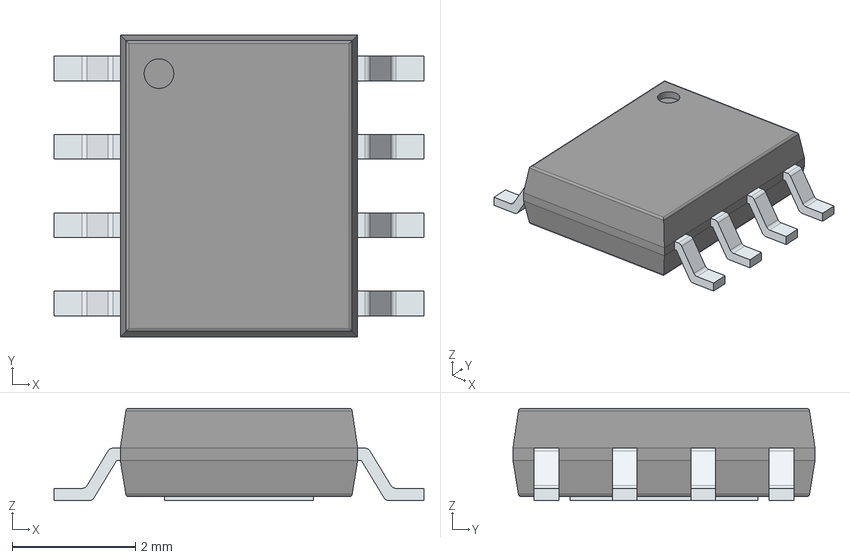
[picture p86: CAD file, 2024-04-12]
Hardware/Model3D/SOIC127P600X150-9N.step
6.00 x 4.90 x 1.50 mm
PinsArrayLR
ThermalPad
