lehungthinh02/KLTN_Data/Hardware/Model3D/CapAlu6.3-7.7M_SMD.stp

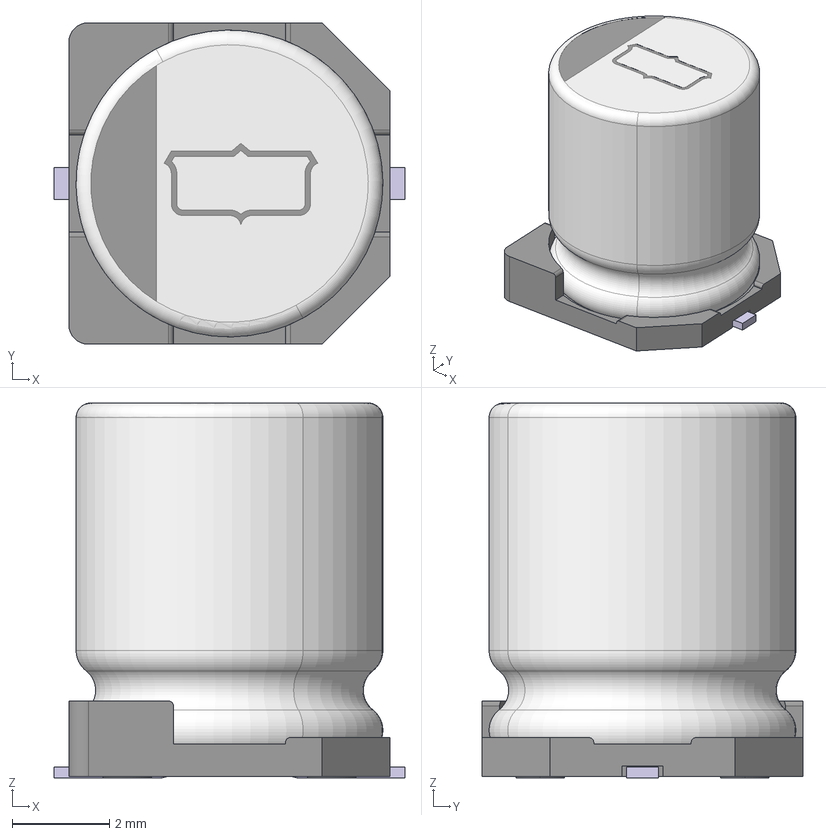
[picture p87: CAD file, 2024-04-12]
Hardware/Model3D/CapAlu6.3-7.7M_SMD.stp
7.20 x 6.60 x 7.70 mm
E-CHIP_D6.3_L7.7_ELEMENT
E-CHIP_D6.3_LEAD-
E-CHIP_D6.3_LEAD＋
E-CHIP_D6.3_TABLE
