lehungthinh02/KLTN_Data/Hardware/Model3D/IND1210_4P.step

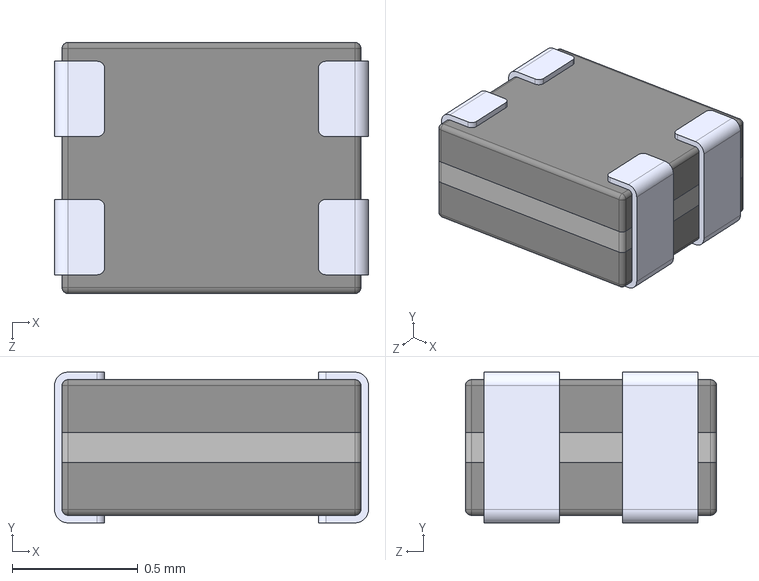
[picture p89: CAD file, 2024-04-12]
Hardware/Model3D/IND1210_4P.step
1.25 x 0.6 x 1.00 mm
