lehungthinh02/KLTN_Data/Hardware/Model3D/TQFP64_PT_MCH.step

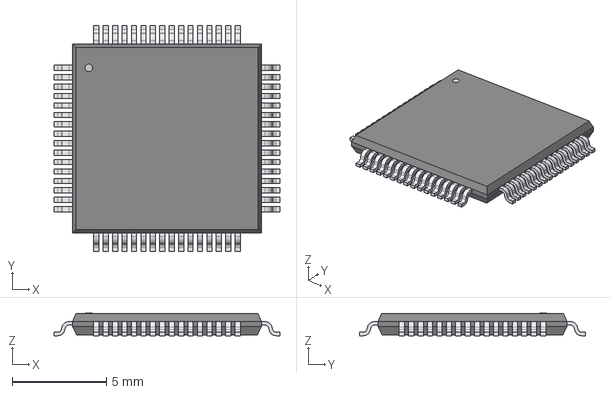
[picture p90: CAD file, 2024-04-12]
Hardware/Model3D/TQFP64_PT_MCH.step
12.0 x 12.0 x 1.20 mm
