lehungthinh02/KLTN_Data/Hardware/Model3D/IND0603.STEP

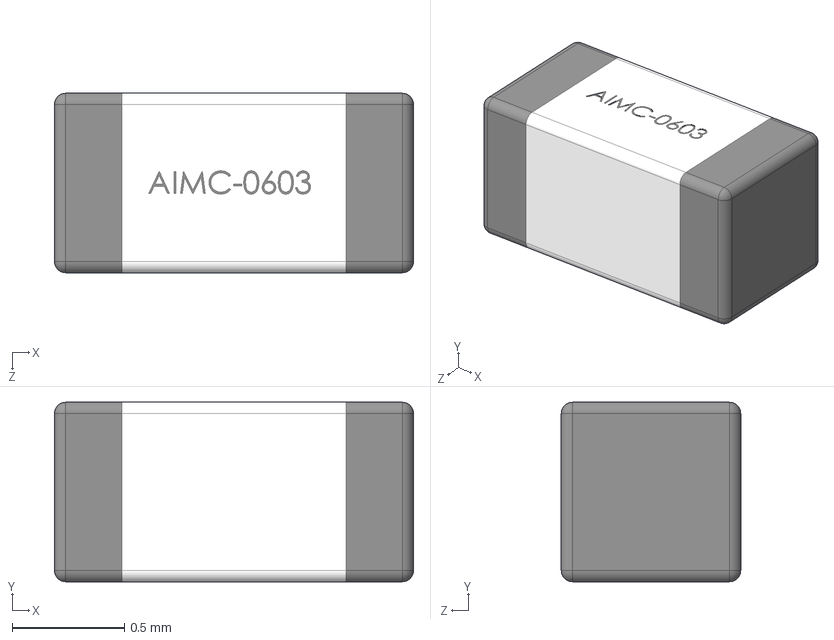
[picture p91: CAD file, 2024-04-12]
Hardware/Model3D/IND0603.STEP
1.60 x 0.8 x 0.8 mm
