lehungthinh02/KLTN_Data/Hardware/Model3D/ATMEL ICE.stp

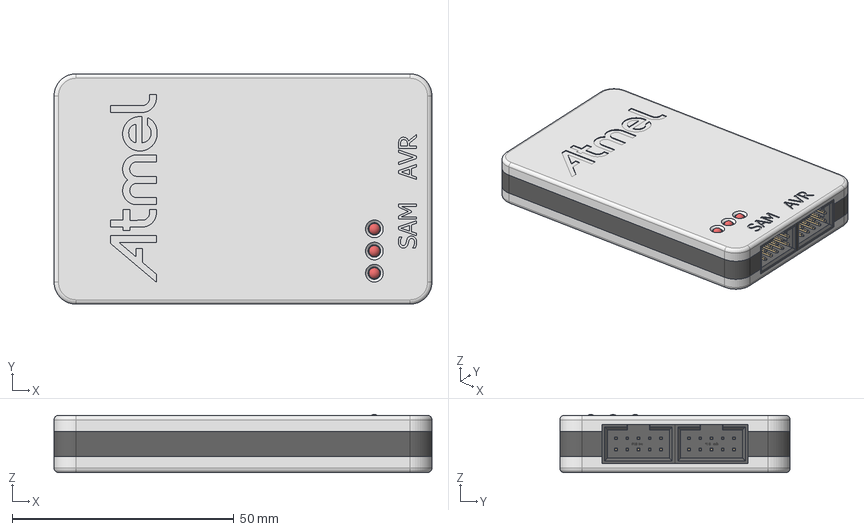
[picture p92: CAD file, 2024-04-12]
Hardware/Model3D/ATMEL ICE.stp
85.3 x 52.0 x 13.1 mm
AICE_BOT
AICE_MID
AICE_TOP
10-Pin Shrouded Header (IDC) Right Angle x 2
ISO 7050 - ST2,2 x 4,5 - C - H x 4
Led x 3
MicroUSB v1
