lehungthinh02/KLTN_Data/Hardware/Model3D/SWITCH SLIDE SPDT CUS-12TB.stp

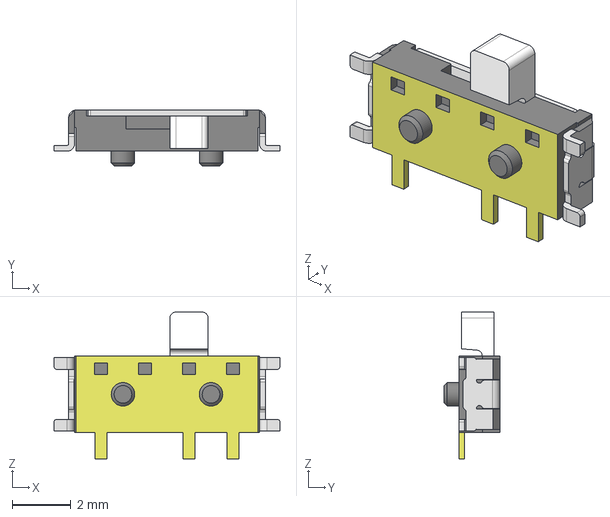
[picture p93: CAD file, 2024-04-12]
Hardware/Model3D/SWITCH SLIDE SPDT CUS-12TB.stp
7.70 x 1.90 x 5.00 mm
_CUS-12-body
_CUS-12-slider
