lehungthinh02/KLTN_Data/Hardware/Model3D/AK-P-13.stp

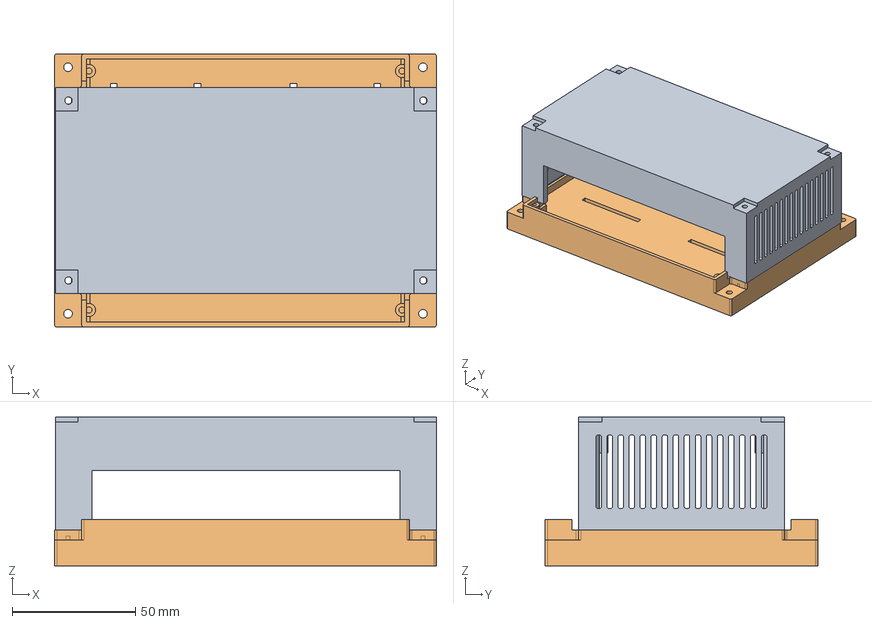
[picture p94: CAD file, 2024-04-12]
Hardware/Model3D/AK-P-13.stp
155.0 x 110.9 x 60.3 mm
