lehungthinh02/KLTN_Data/Hardware/Model3D/SOT23_SEM.step

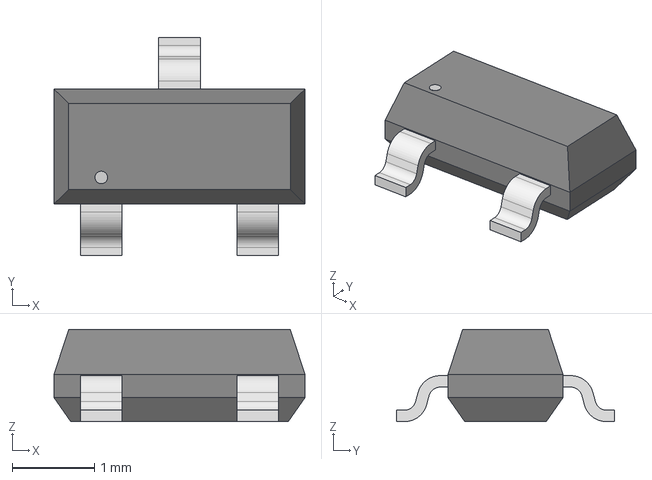
[picture p95: CAD file, 2024-04-12]
Hardware/Model3D/SOT23_SEM.step
3.05 x 2.64 x 1.12 mm
