lehungthinh02/KLTN_Data/Hardware/Model3D/SOT-363.step

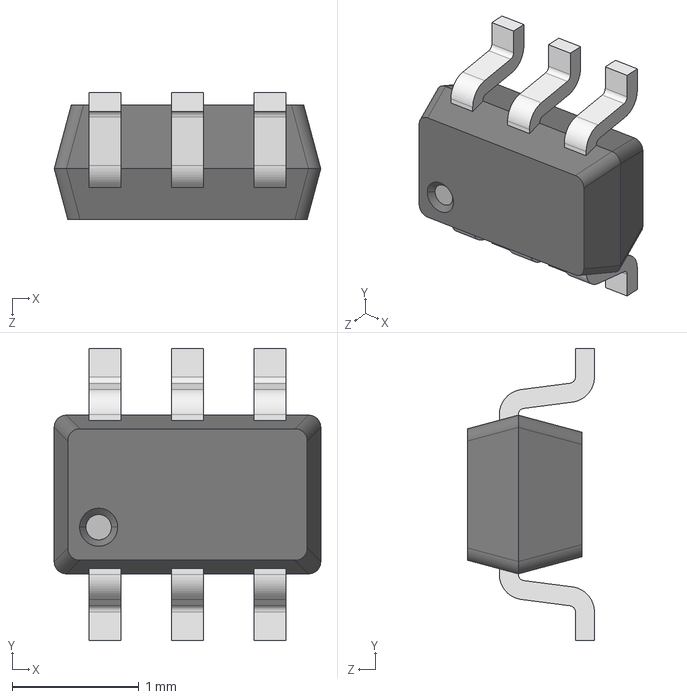
[picture p96: CAD file, 2024-04-12]
Hardware/Model3D/SOT-363.step
2.10 x 2.30 x 1.00 mm
