lehungthinh02/KLTN_Data/Hardware/Model3D/DFN 3_3x3_3.step

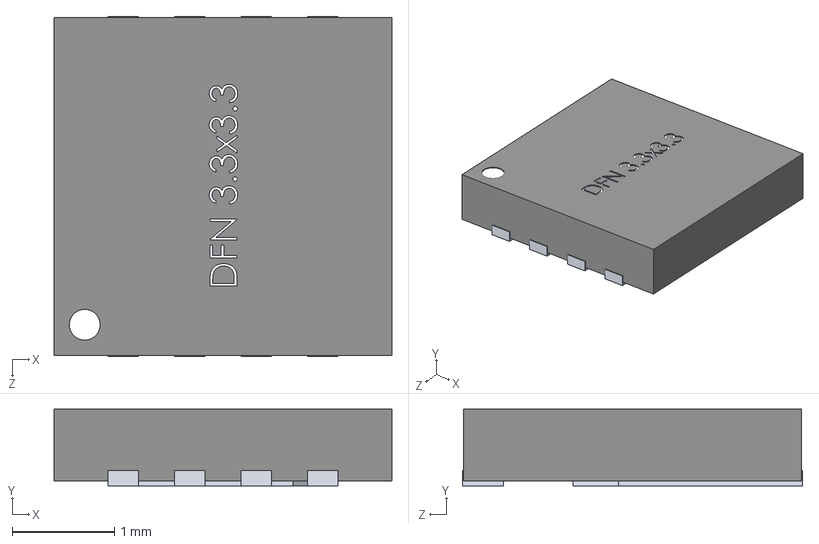
[picture p97: CAD file, 2024-04-12]
Hardware/Model3D/DFN 3_3x3_3.step
3.30 x 0.75 x 3.32 mm
