lehungthinh02/KLTN_Data/Hardware/Model3D/ESK228M025AL4AA.step

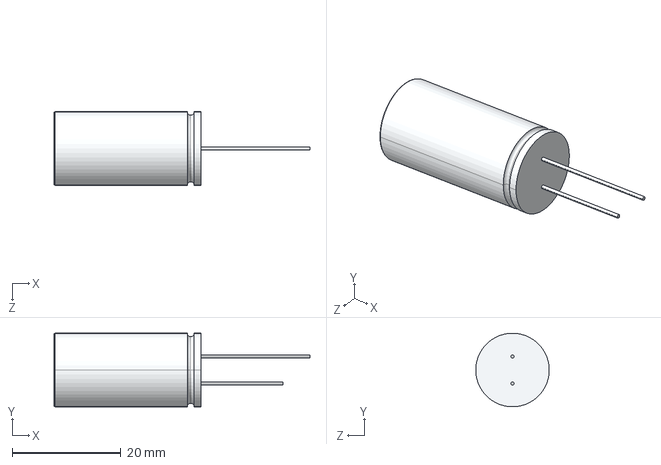
[picture p98: CAD file, 2024-04-12]
Hardware/Model3D/ESK228M025AL4AA.step
47.0 x 13.5 x 13.5 mm
