lehungthinh02/KLTN_Data/Hardware/Model3D/srn4018-2r2m.stp

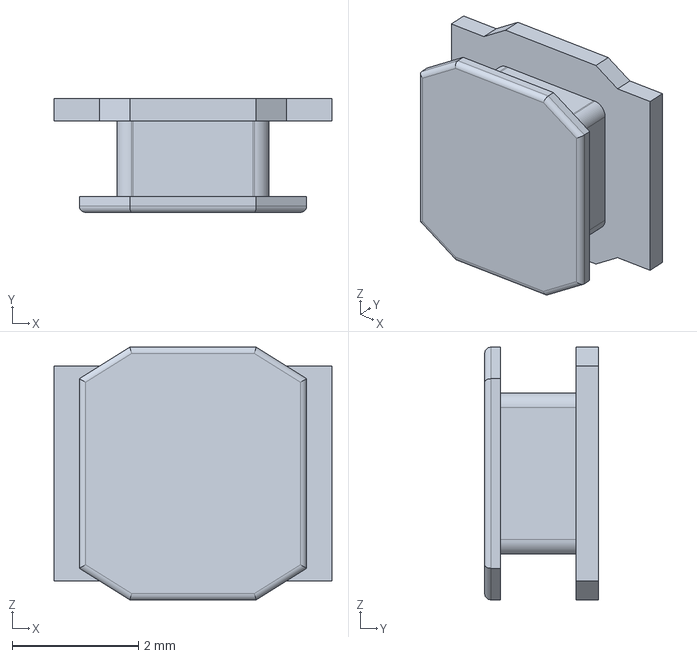
[picture p99: CAD file, 2024-04-12]
Hardware/Model3D/srn4018-2r2m.stp
4.40 x 1.80 x 4.00 mm
