lehungthinh02/KLTN_Data/Hardware/Model3D/ADR5040BRTZ-REEL7.stp

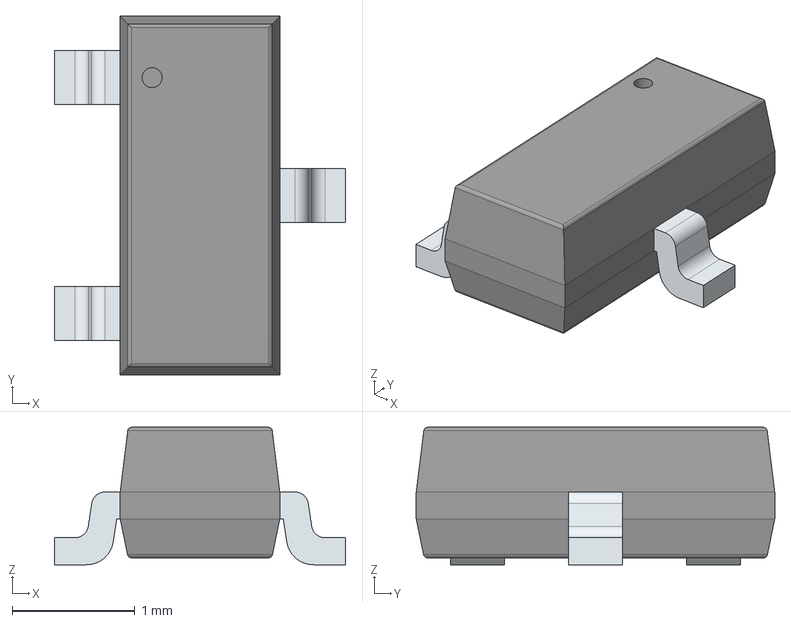
[picture p100: CAD file, 2024-04-12]
Hardware/Model3D/ADR5040BRTZ-REEL7.stp
2.37 x 2.92 x 1.12 mm
PinsArrayL
FilletPinR
