lehungthinh02/KLTN_Data/Hardware/Model3D/QFN50P800X800X100-57N-D.step

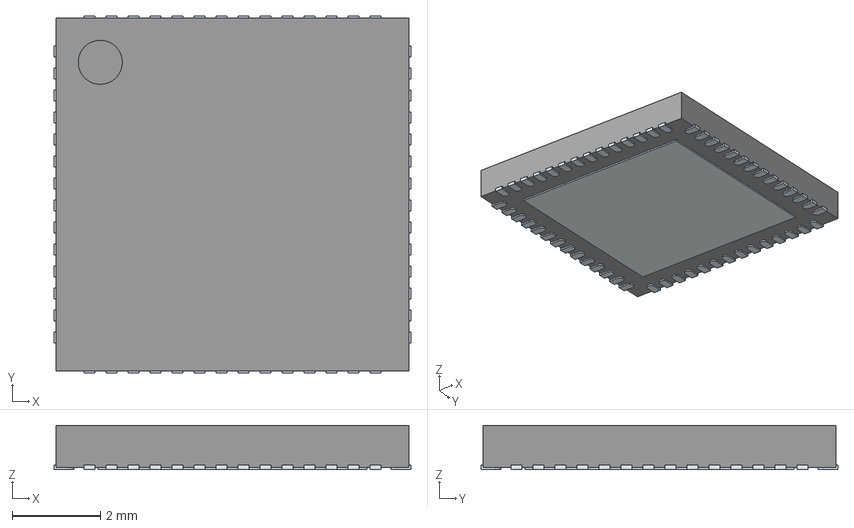
[picture p101: CAD file, 2024-04-12]
Hardware/Model3D/QFN50P800X800X100-57N-D.step
8.10 x 8.10 x 1.00 mm
ThermalPin
PinsArrayLR
PinsArrayTB
