lehungthinh02/KLTN_Data/Hardware/Model3D/eSIM-ST-MFF2.STEP

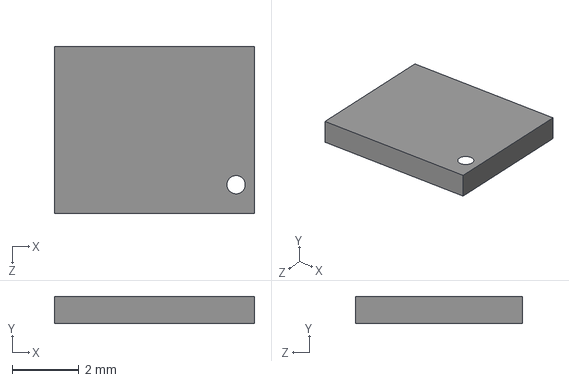
[picture p102: CAD file, 2024-04-12]
Hardware/Model3D/eSIM-ST-MFF2.STEP
6.00 x 0.82 x 5.00 mm
