lehungthinh02/KLTN_Data/Hardware/Model3D/CL21A106KOFNNNE.STEP

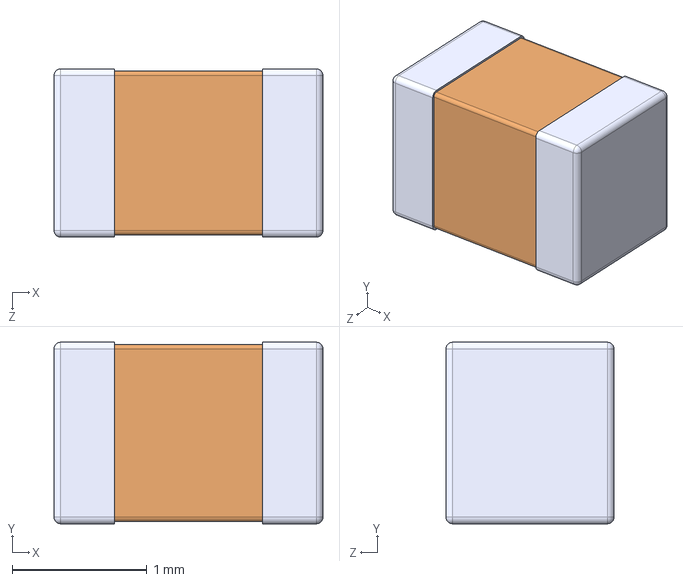
[picture p103: CAD file, 2024-04-12]
Hardware/Model3D/CL21A106KOFNNNE.STEP
2.00 x 1.35 x 1.25 mm
