lehungthinh02/KLTN_Data/Hardware/Model3D/LED APA2107.STEP

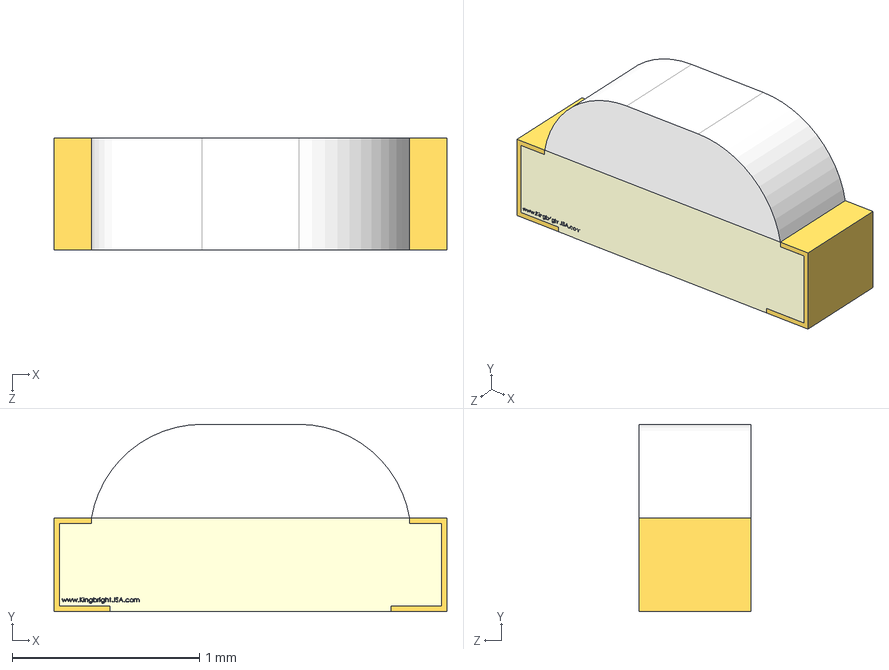
[picture p104: CAD file, 2024-04-12]
Hardware/Model3D/LED APA2107.STEP
2.10 x 1.00 x 0.6 mm
