lehungthinh02/KLTN_Data/Hardware/Model3D/ADUM4160BRWZ.STEP

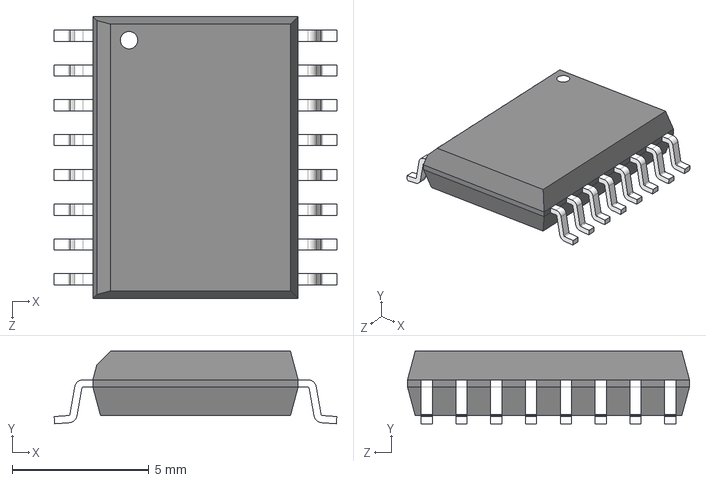
[picture p105: CAD file, 2024-04-12]
Hardware/Model3D/ADUM4160BRWZ.STEP
10.3 x 2.65 x 10.3 mm
