lehungthinh02/KLTN_Data/Hardware/Model3D/HalogenLamp-6.35.step

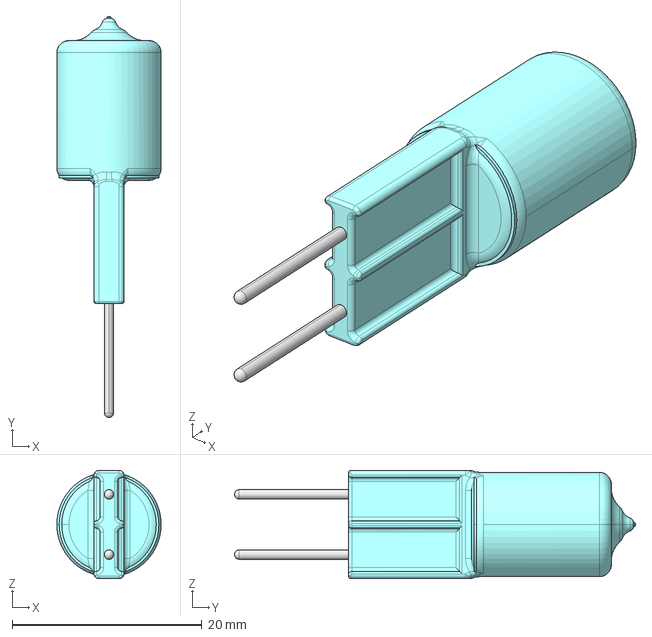
[picture p106: CAD file, 2024-04-12]
Hardware/Model3D/HalogenLamp-6.35.step
11.0 x 42.3 x 11.4 mm
