lehungthinh02/KLTN_Data/Hardware/Model3D/HDM-TH-1x20x2.54R.STEP

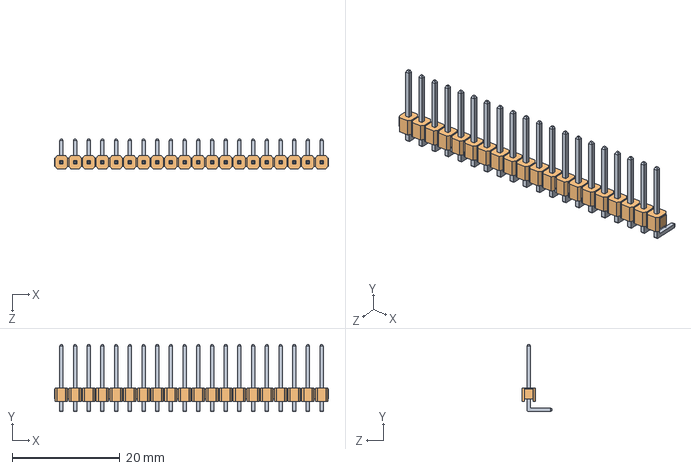
[picture p107: CAD file, 2024-04-12]
Hardware/Model3D/HDM-TH-1x20x2.54R.STEP
50.8 x 12.4 x 5.59 mm
