lehungthinh02/KLTN_Data/Hardware/Model3D/0ZCJ0035FF2G.step

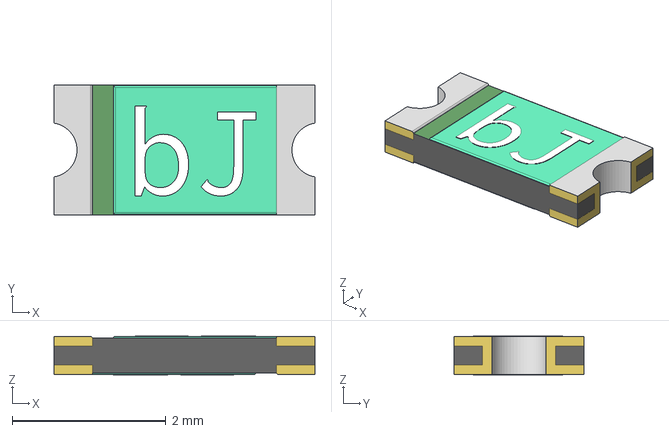
[picture p108: CAD file, 2024-04-12]
Hardware/Model3D/0ZCJ0035FF2G.step
3.40 x 1.70 x 0.508 mm
