lehungthinh02/KLTN_Data/Hardware/Model3D/B022NFSS-RC.STEP

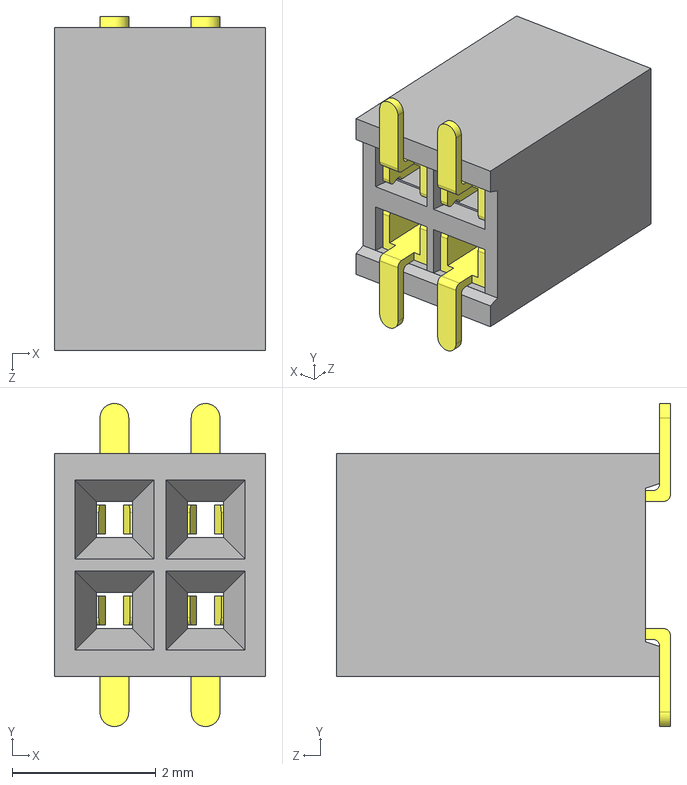
[picture p109: CAD file, 2024-04-12]
Hardware/Model3D/B022NFSS-RC.STEP
2.94 x 4.50 x 4.65 mm
