lehungthinh02/KLTN_Data/Hardware/Model3D/DT-49-C91W-03.stp

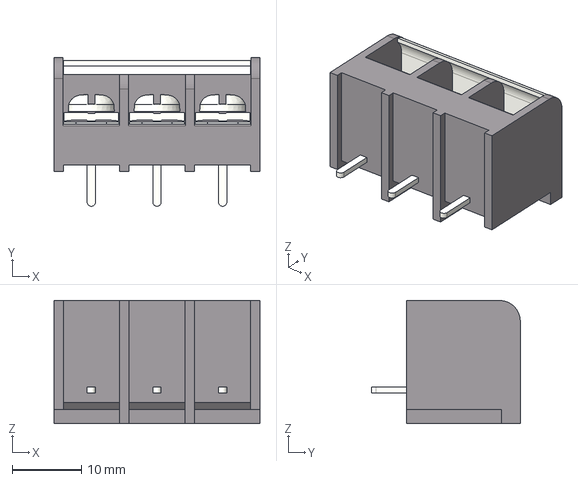
[picture p110: CAD file, 2024-04-12]
Hardware/Model3D/DT-49-C91W-03.stp
29.8 x 21.5 x 17.8 mm
