lehungthinh02/KLTN_Data/Hardware/Model3D/DT-49-C91W-04.stp

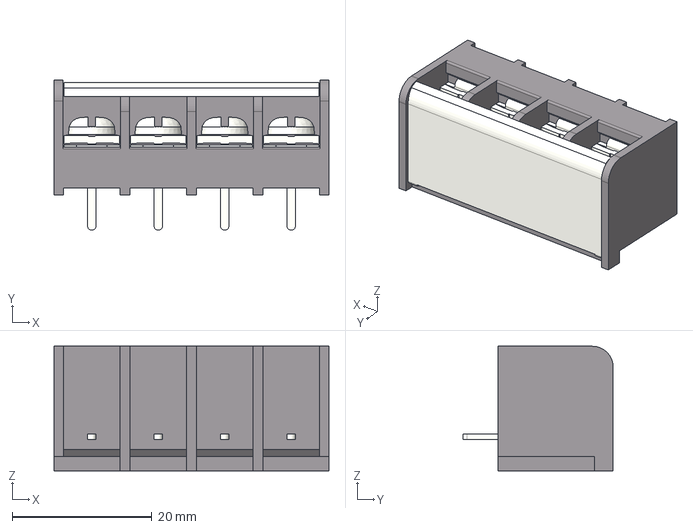
[picture p111: CAD file, 2024-04-12]
Hardware/Model3D/DT-49-C91W-04.stp
39.3 x 21.5 x 17.8 mm
