lehungthinh02/KLTN_Data/Hardware/Model3D/CapAlu12.5-13.5M_SMD.stp

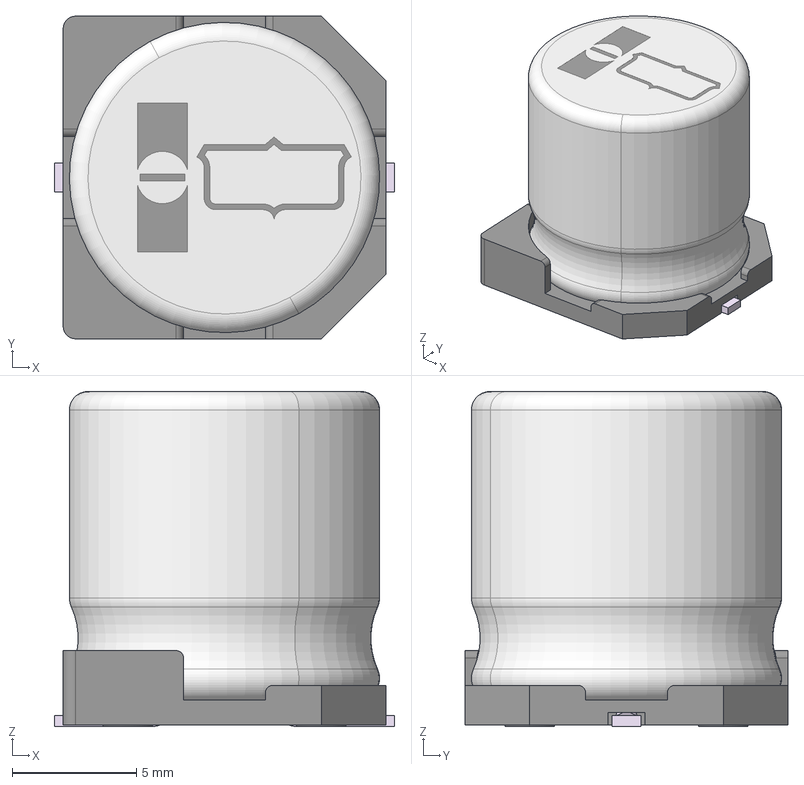
[picture p112: CAD file, 2024-04-12]
Hardware/Model3D/CapAlu12.5-13.5M_SMD.stp
13.7 x 13.0 x 13.5 mm
E-CHIP_D12.5_LEAD+
E-CHIP_D12.5_LEAD-
E-CHIP_D12.5_TABLE
E-CHIP_D12.5_L13.5_ELEMENT
