lehungthinh02/KLTN_Data/Hardware/Model3D/B_S-1WR3.stp

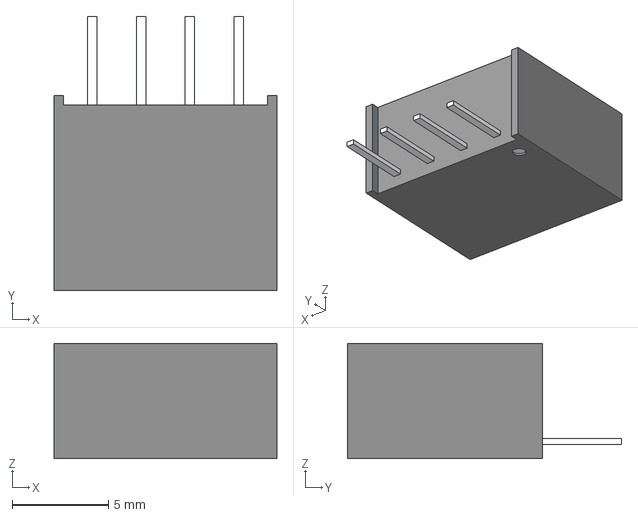
[picture p113: CAD file, 2024-04-12]
Hardware/Model3D/B_S-1WR3.stp
11.6 x 14.3 x 6.00 mm
