lehungthinh02/KLTN_Data/Hardware/Model3D/TO-3P-3LD.step

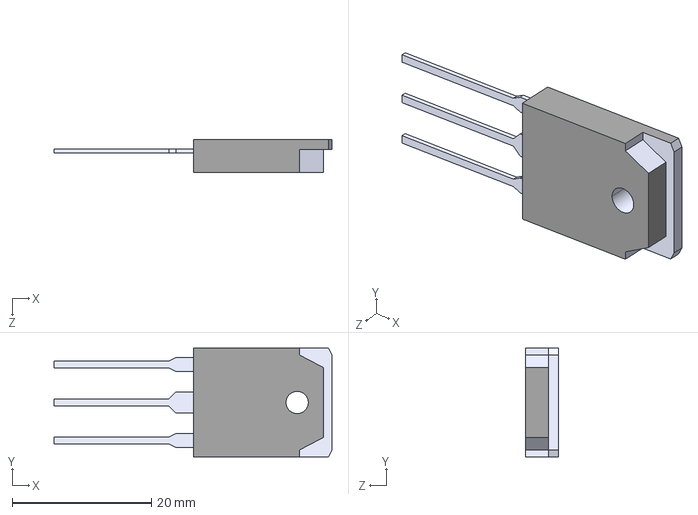
[picture p114: CAD file, 2024-04-12]
Hardware/Model3D/TO-3P-3LD.step
39.9 x 15.6 x 4.80 mm
