lehungthinh02/KLTN_Data/Hardware/Model3D/40UQFN.STEP

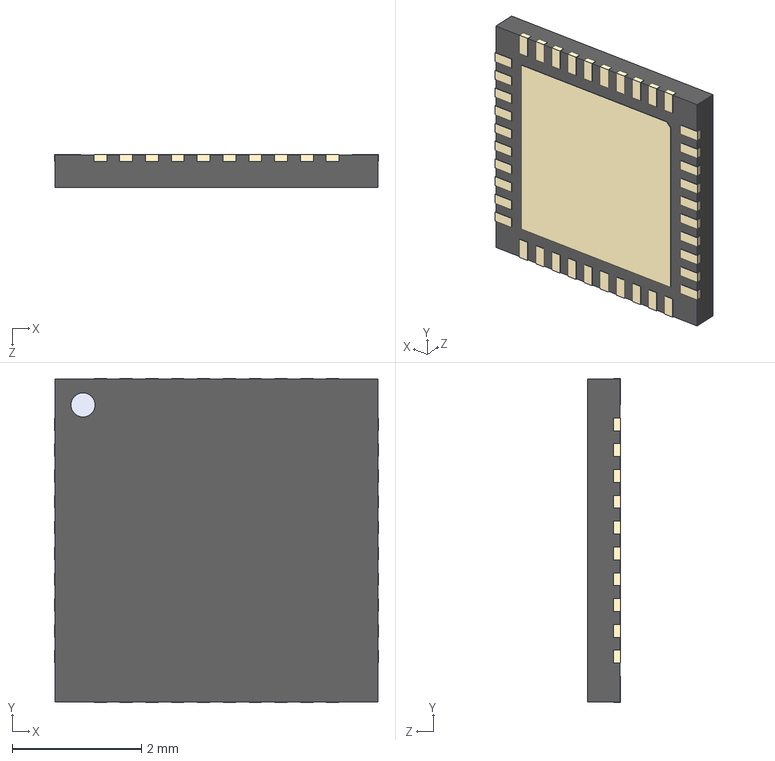
[picture p115: CAD file, 2024-04-12]
Hardware/Model3D/40UQFN.STEP
5.02 x 5.02 x 0.51 mm
