lehungthinh02/KLTN_Data/Hardware/Model3D/CGGBP.18.4.A.02.STEP

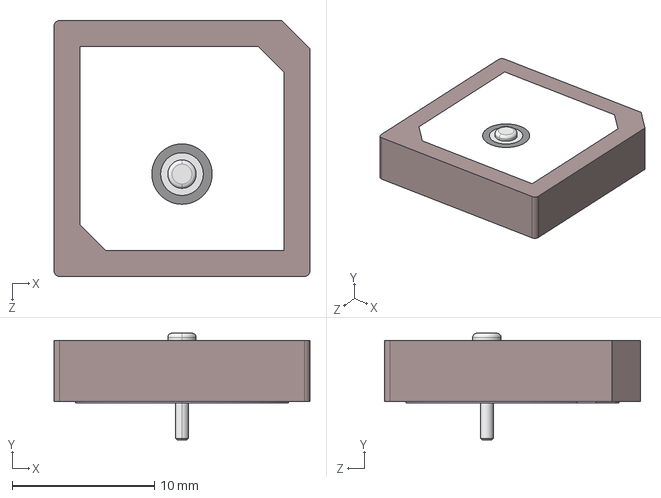
[picture p116: CAD file, 2024-04-12]
Hardware/Model3D/CGGBP.18.4.A.02.STEP
18.0 x 7.50 x 18.0 mm
