lehungthinh02/KLTN_Data/Hardware/Model3D/CD75.step

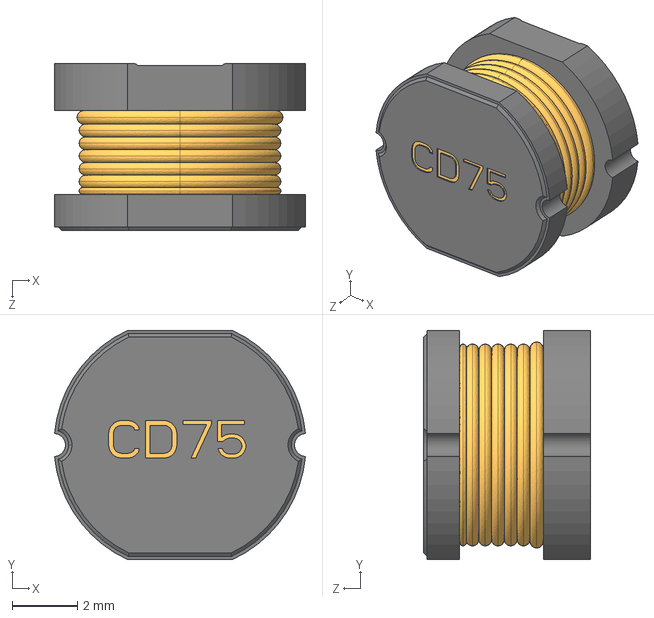
[picture p117: CAD file, 2024-04-12]
Hardware/Model3D/CD75.step
7.67 x 7.00 x 5.09 mm
