lehungthinh02/KLTN_Data/Hardware/Model3D/OLED-1.3-128x64.step

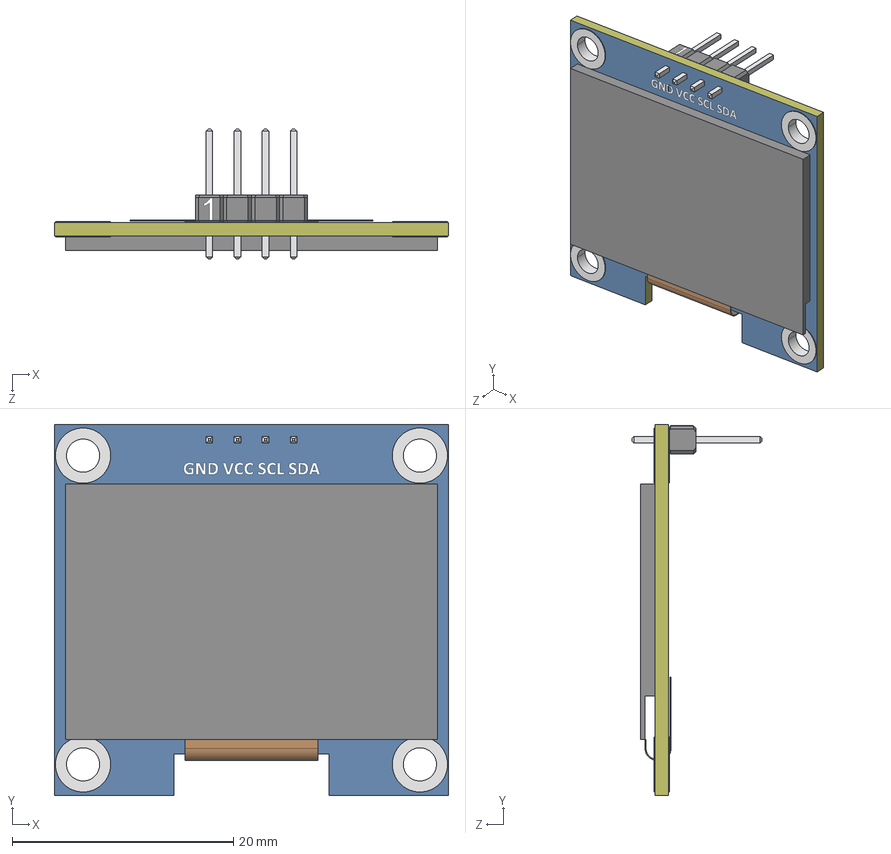
[picture p118: CAD file, 2024-04-12]
Hardware/Model3D/OLED-1.3-128x64.step
35.6 x 33.6 x 11.8 mm
