lehungthinh02/KLTN_Data/Hardware/Model3D/DSC1001CE1-012.0000.step

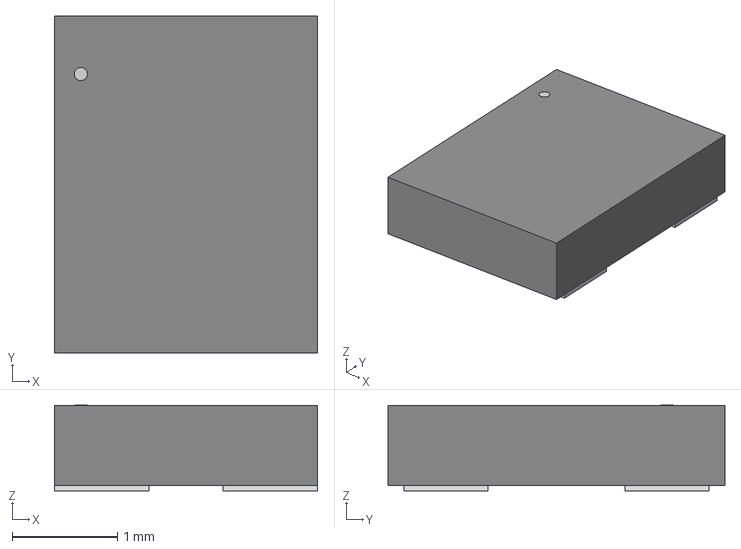
[picture p120: CAD file, 2024-04-12]
Hardware/Model3D/DSC1001CE1-012.0000.step
2.50 x 3.20 x 0.815 mm
