lehungthinh02/KLTN_Data/Hardware/Model3D/IND0402_CW105550A.stp

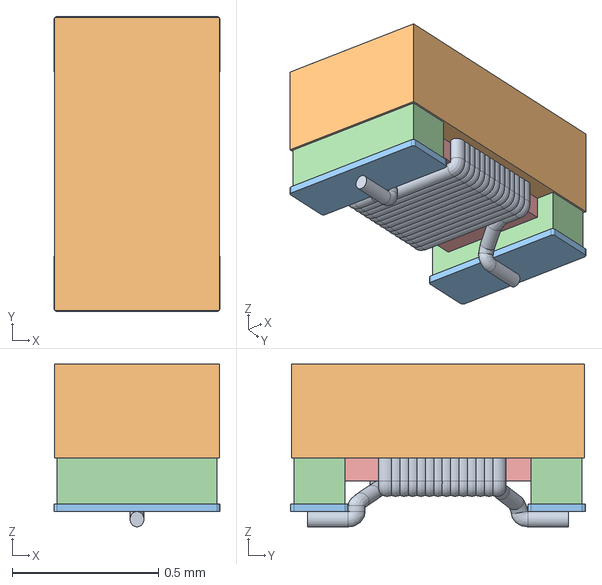
[picture p121: CAD file, 2024-04-12]
Hardware/Model3D/IND0402_CW105550A.stp
0.568 x 1.01 x 0.557 mm
