lehungthinh02/KLTN_Data/Hardware/Model3D/CSYTAL-MC146.step

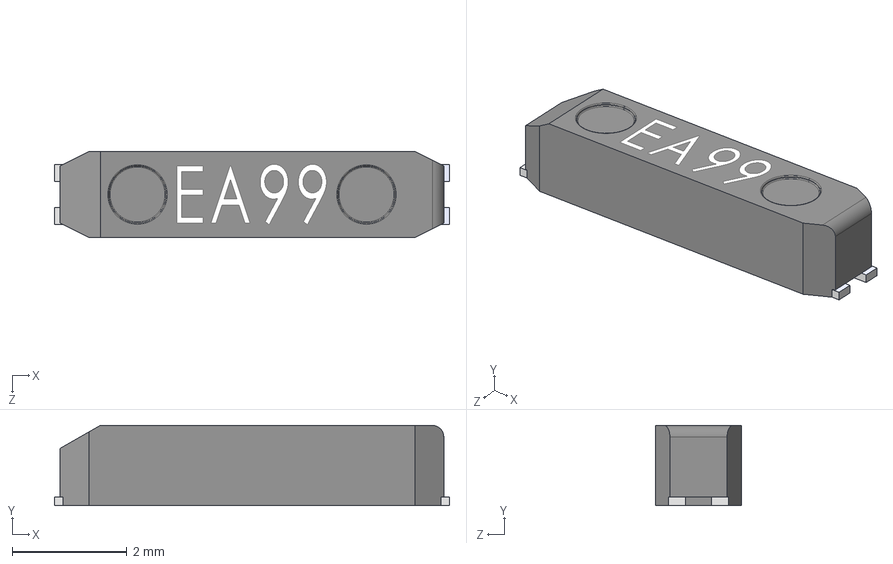
[picture p122: CAD file, 2024-04-12]
Hardware/Model3D/CSYTAL-MC146.step
6.90 x 1.40 x 1.50 mm
