lehungthinh02/KLTN_Data/Hardware/Model3D/74CBTLV3257BQ115.step

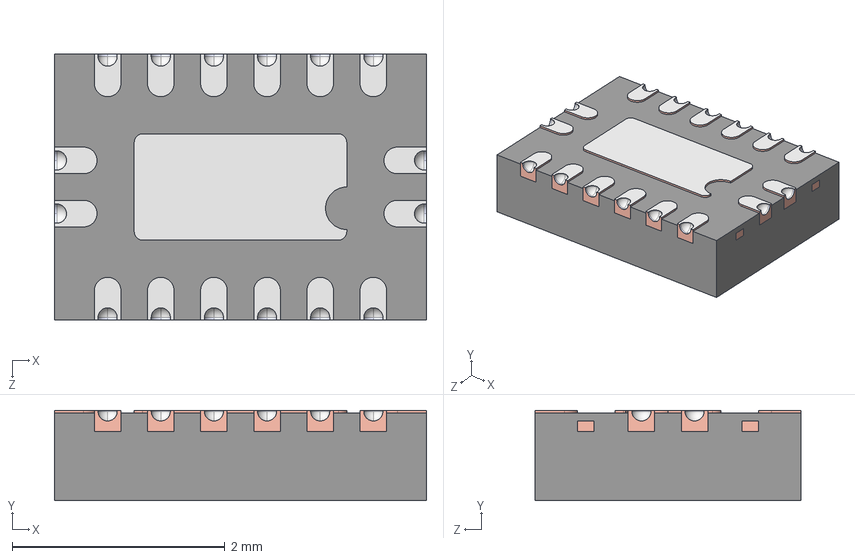
[picture p123: CAD file, 2024-04-12]
Hardware/Model3D/74CBTLV3257BQ115.step
3.50 x 0.85 x 2.50 mm
SOT763-1 LF
SOT763-1 Mold Body
