lehungthinh02/KLTN_Data/Hardware/Model3D/HDM-4x2.54-TH-RA.step

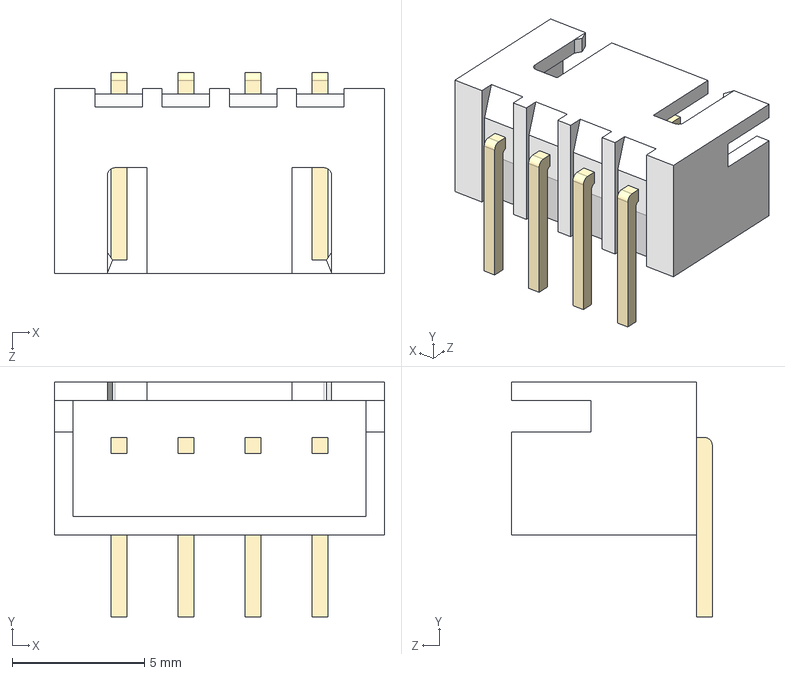
[picture p124: CAD file, 2024-04-12]
Hardware/Model3D/HDM-4x2.54-TH-RA.step
12.5 x 8.90 x 7.60 mm
