lehungthinh02/KLTN_Data/Hardware/Model3D/c-1-1825027-1-g-3d.stp

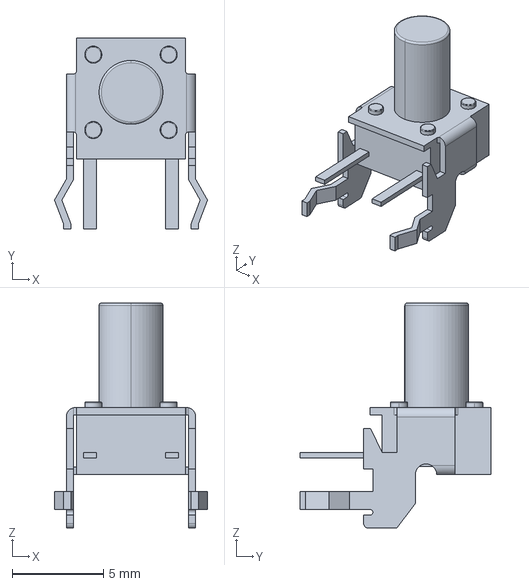
[picture p125: CAD file, 2024-04-12]
Hardware/Model3D/c-1-1825027-1-g-3d.stp
8.41 x 10.5 x 12.4 mm
