lehungthinh02/KLTN_Data/Hardware/Model3D/3557-2.step

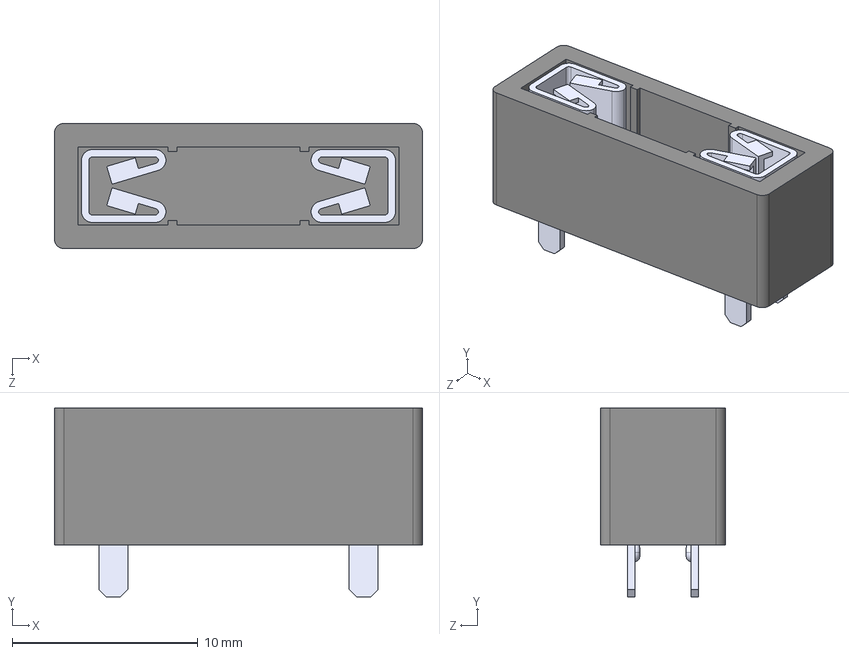
[picture p126: CAD file, 2024-04-12]
Hardware/Model3D/3557-2.step
19.8 x 10.2 x 6.73 mm
