lehungthinh02/KLTN_Data/Hardware/Model3D/SOIC127P1000X230-6N.step

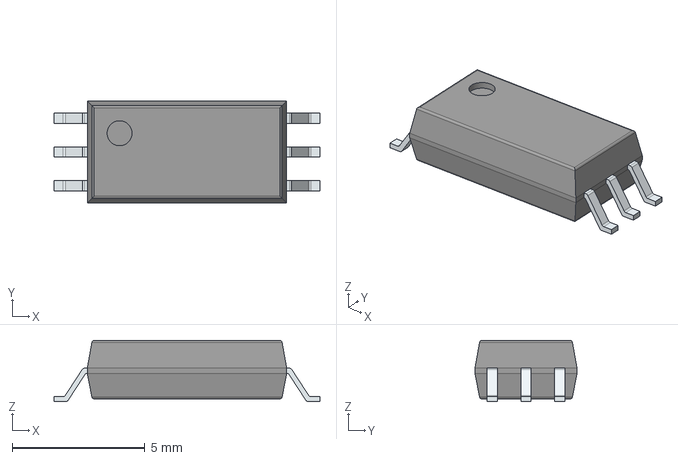
[picture p127: CAD file, 2024-04-12]
Hardware/Model3D/SOIC127P1000X230-6N.step
10.0 x 3.84 x 2.30 mm
PinsArrayLR
