lehungthinh02/KLTN_Data/Hardware/Model3D/YDRA-A18-1575.step

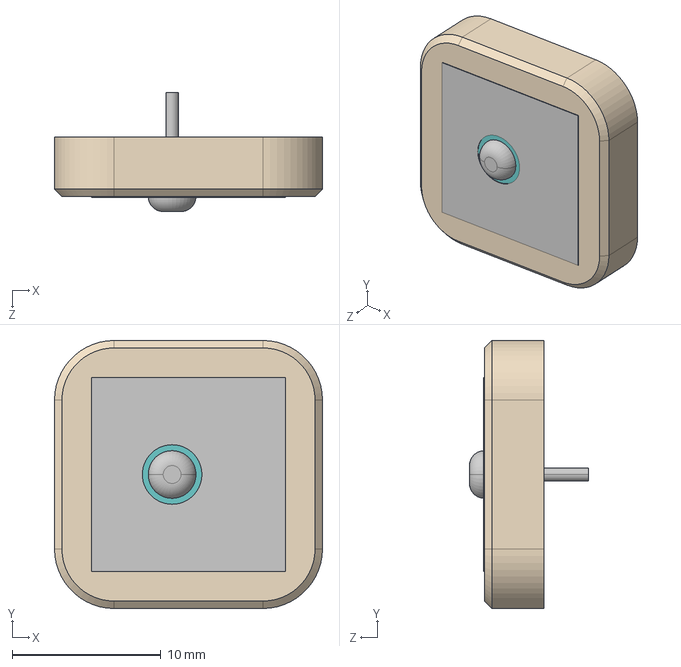
[picture p128: CAD file, 2024-04-12]
Hardware/Model3D/YDRA-A18-1575.step
18.0 x 18.0 x 8.00 mm
