lehungthinh02/KLTN_Data/Hardware/Model3D/AH3G.STEP

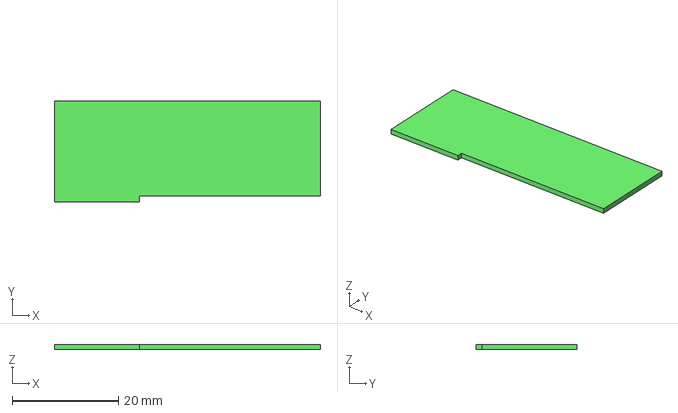
[picture p129: CAD file, 2024-04-12]
Hardware/Model3D/AH3G.STEP
50.0 x 19.0 x 1.00 mm
