lehungthinh02/KLTN_Data/Hardware/Model3D/SOD-128Flat.step

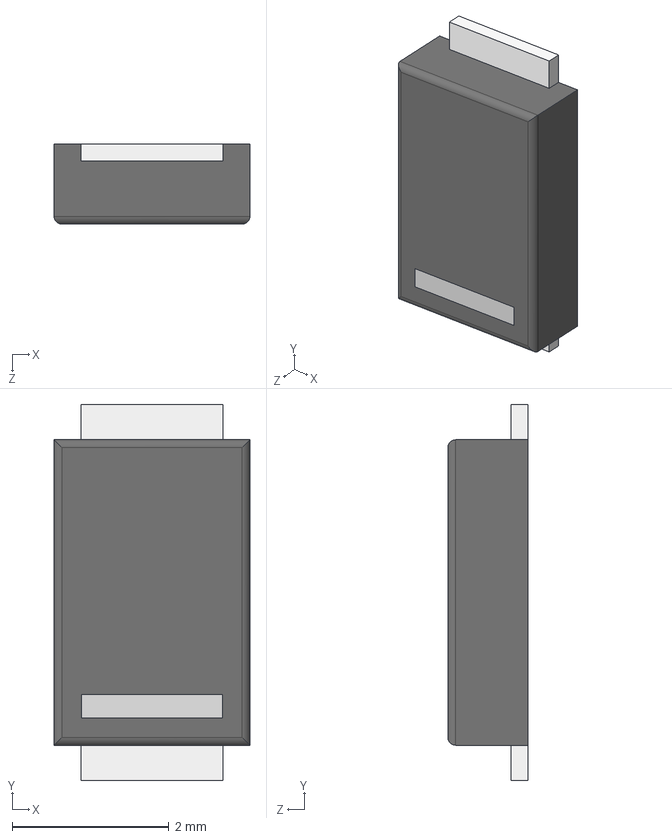
[picture p130: CAD file, 2024-04-12]
Hardware/Model3D/SOD-128Flat.step
2.50 x 4.80 x 1.02 mm
