lehungthinh02/KLTN_Data/Hardware/Model3D/MSOP8.step

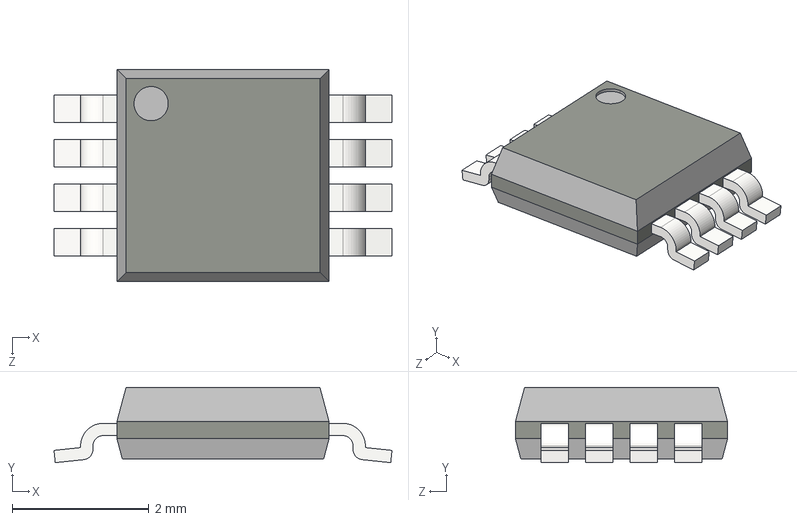
[picture p131: CAD file, 2024-04-12]
Hardware/Model3D/MSOP8.step
4.94 x 1.10 x 3.10 mm
