lehungthinh02/KLTN_Data/Hardware/Model3D/VQFN-20-3x3-0.45.STEP

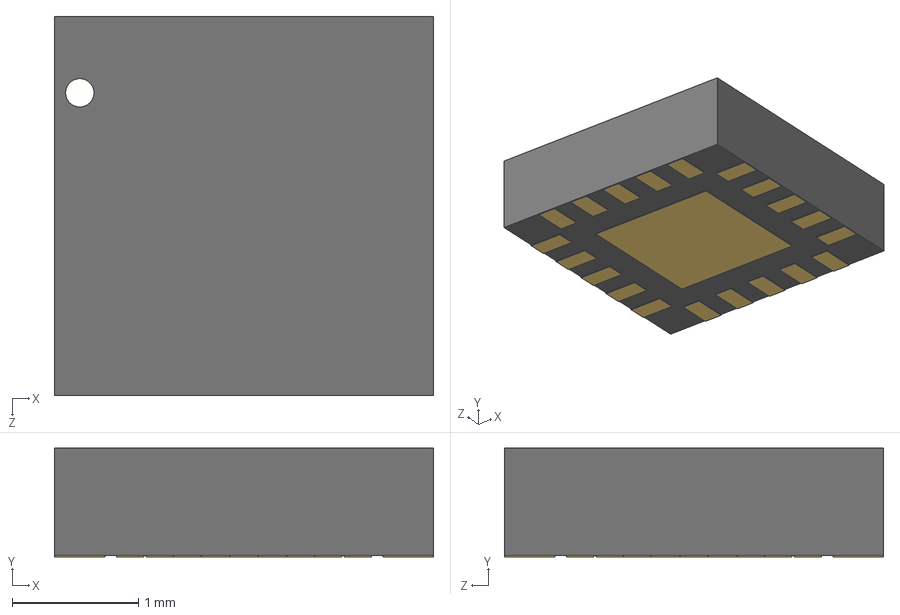
[picture p132: CAD file, 2024-04-12]
Hardware/Model3D/VQFN-20-3x3-0.45.STEP
3.00 x 0.86 x 3.00 mm
