lehungthinh02/KLTN_Data/Hardware/Model3D/SON40P135X330X55-17N-D.stp

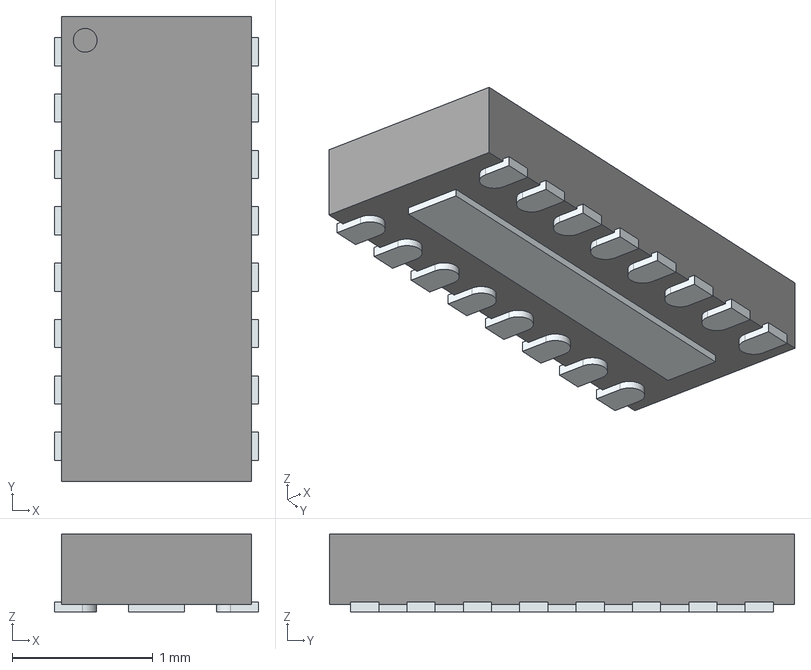
[picture p133: CAD file, 2024-04-12]
Hardware/Model3D/SON40P135X330X55-17N-D.stp
1.45 x 3.30 x 0.55 mm
ThermalPin
PinsArrayLR
