lehungthinh02/KLTN_Data/Hardware/Model3D/LD10-23BxxR2-RC.step

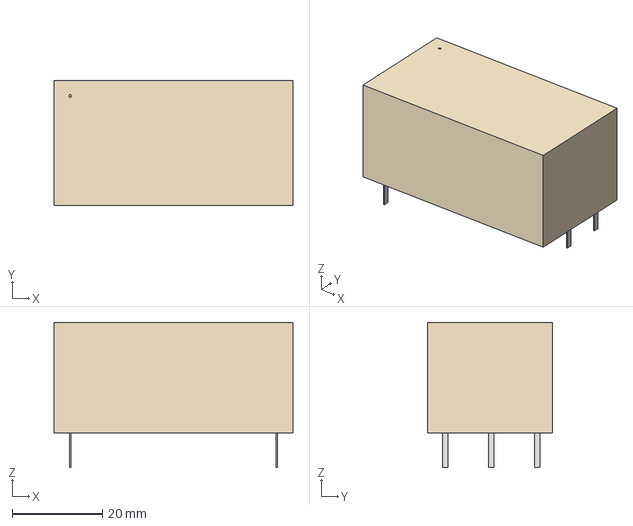
[picture p134: CAD file, 2024-04-12]
Hardware/Model3D/LD10-23BxxR2-RC.step
52.9 x 27.7 x 32.1 mm
