lehungthinh02/KLTN_Data/Hardware/Model3D/4341x3.stp

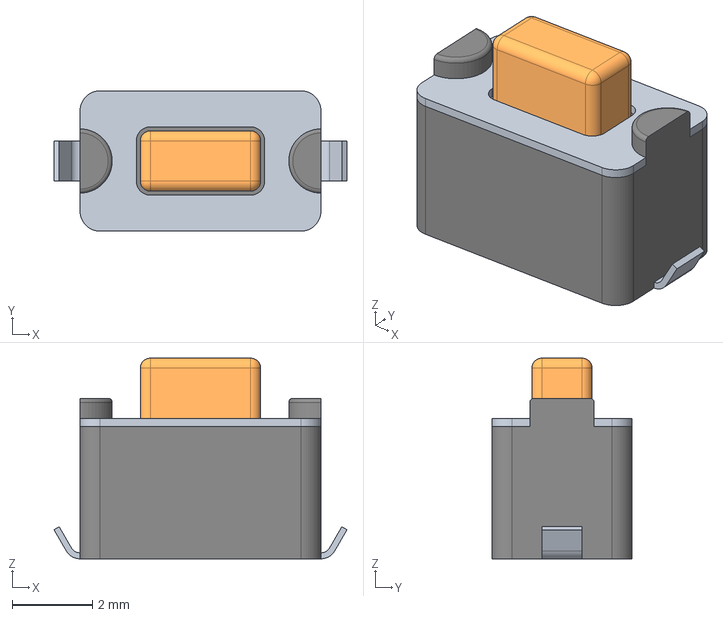
[picture p135: CAD file, 2024-04-12]
Hardware/Model3D/4341x3.stp
7.30 x 3.50 x 5.00 mm
