lehungthinh02/KLTN_Data/Hardware/Model3D/X4B.STEP

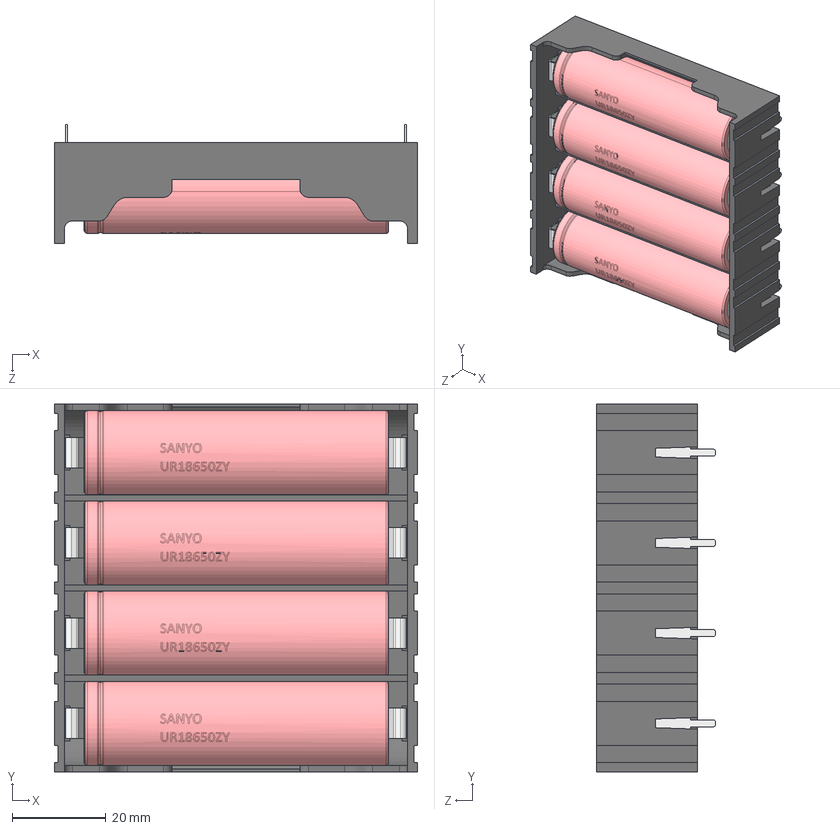
[picture p136: CAD file, 2024-04-12]
Hardware/Model3D/X4B.STEP
77.6 x 78.7 x 25.5 mm
18650m_4
18650s x 8
18650_Cell only x 4
