lehungthinh02/KLTN_Data/Hardware/Model3D/CI0108M1HR0-NH.STEP

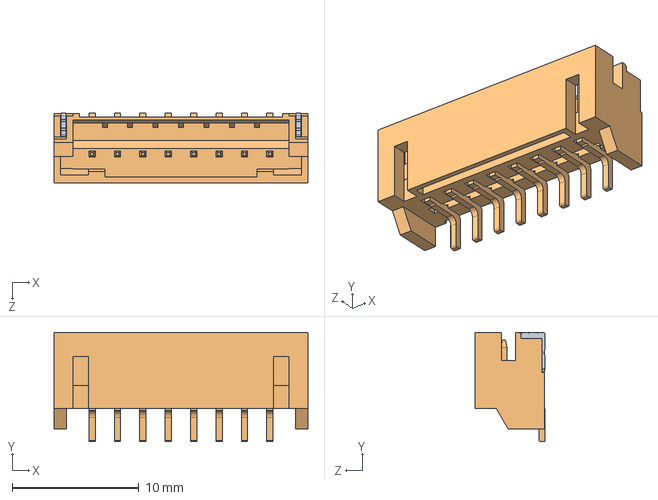
[picture p137: CAD file, 2024-04-12]
Hardware/Model3D/CI0108M1HR0-NH.STEP
20.0 x 8.60 x 5.55 mm
