lehungthinh02/KLTN_Data/Hardware/Model3D/TL3330AFxxxQG.stp

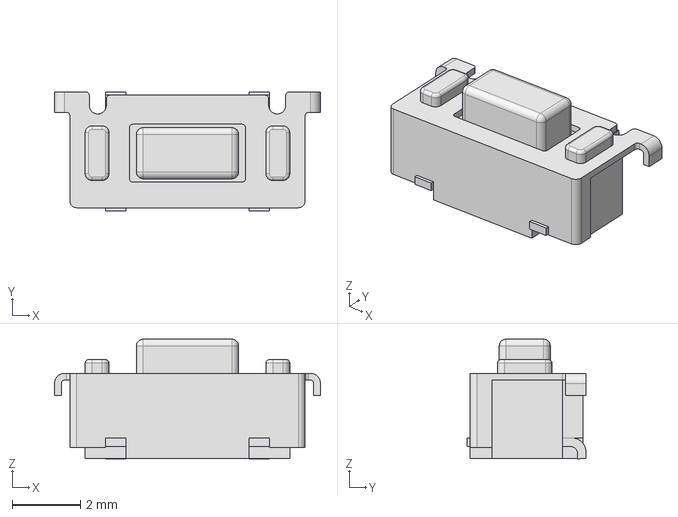
[picture p138: CAD file, 2024-04-12]
Hardware/Model3D/TL3330AFxxxQG.stp
7.80 x 3.50 x 3.51 mm
