lehungthinh02/KLTN_Data/Hardware/Model3D/CAP_FILM_6.0x12.0x12.5-P10.step

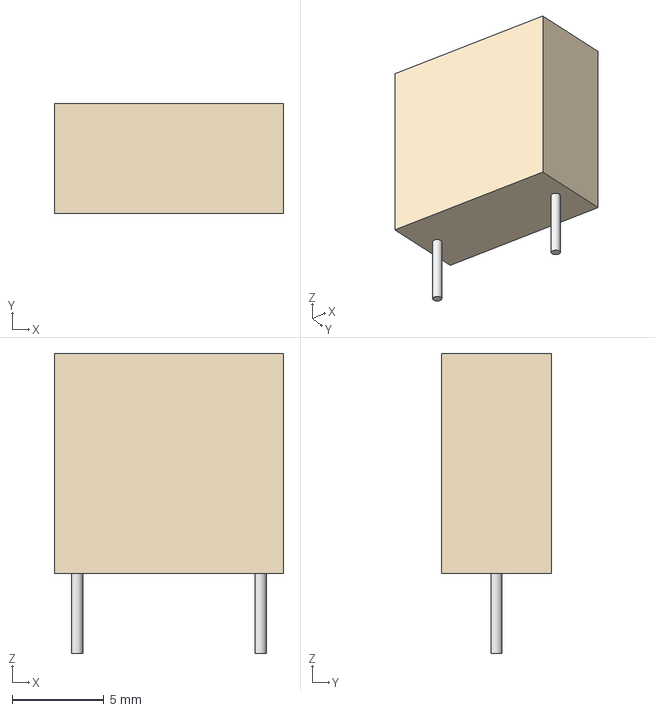
[picture p139: CAD file, 2024-04-12]
Hardware/Model3D/CAP_FILM_6.0x12.0x12.5-P10.step
12.5 x 5.99 x 16.4 mm
