lehungthinh02/KLTN_Data/Hardware/Model3D/B061NGCN-RC.STEP

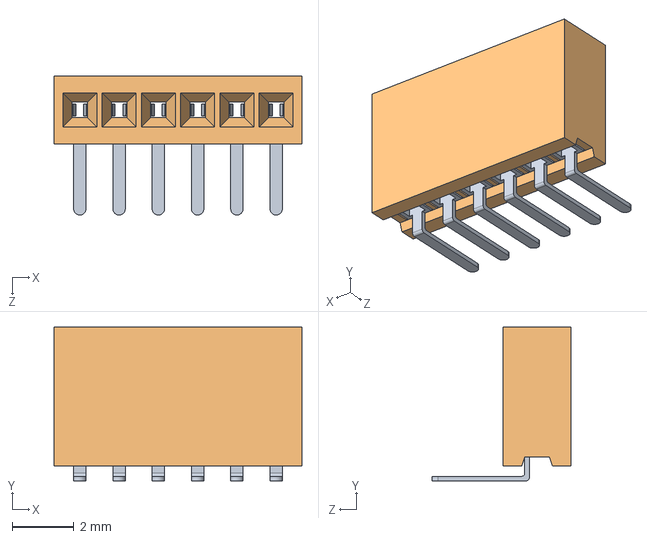
[picture p140: CAD file, 2024-04-12]
Hardware/Model3D/B061NGCN-RC.STEP
8.02 x 4.98 x 4.50 mm
