lehungthinh02/KLTN_Data/Hardware/Model3D/0402R.step

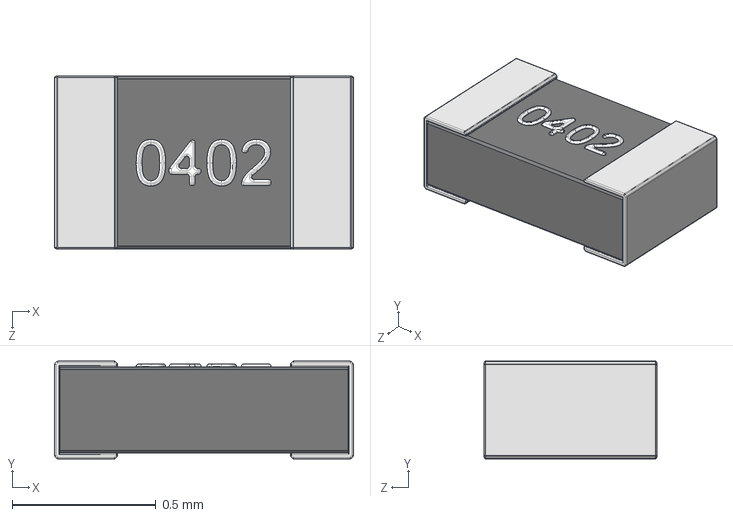
[picture p141: CAD file, 2024-04-12]
Hardware/Model3D/0402R.step
1.04 x 0.34 x 0.6 mm
