lehungthinh02/KLTN_Data/Hardware/Model3D/74HC245BQQ100X.step

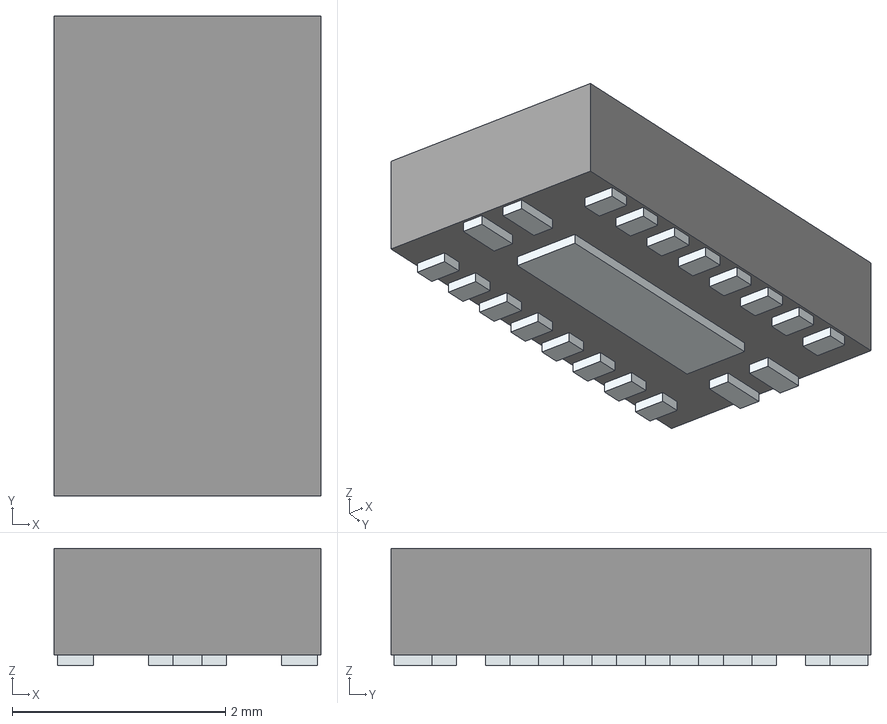
[picture p142: CAD file, 2024-04-12]
Hardware/Model3D/74HC245BQQ100X.step
2.50 x 4.50 x 1.10 mm
Pins
