lehungthinh02/KLTN_Data/Hardware/Model3D/SSOP-16_5.3X7.8X6.2.STEP

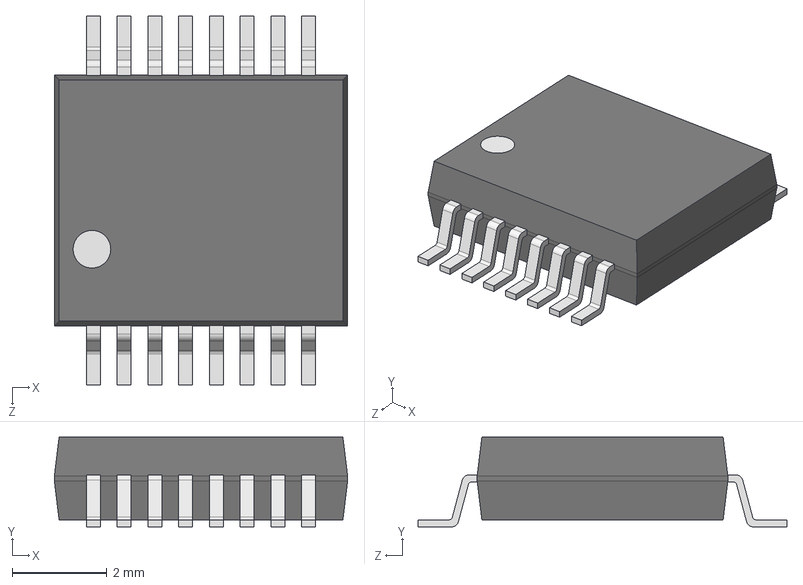
[picture p143: CAD file, 2024-04-12]
Hardware/Model3D/SSOP-16_5.3X7.8X6.2.STEP
6.20 x 1.90 x 7.80 mm
_X2_041A043E0440043F04430441_X0_
_X2_041C04350442043A0430_X0_
_X2_041D043E0436043A0430_X0_ x 8
