lehungthinh02/KLTN_Data/Hardware/Model3D/MCP1727T-3302E_SN.STEP

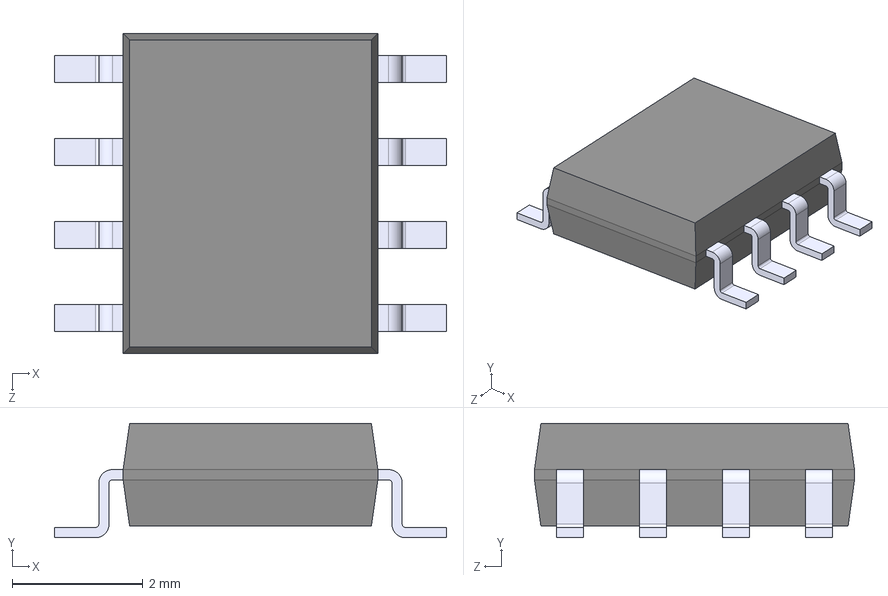
[picture p144: CAD file, 2024-04-12]
Hardware/Model3D/MCP1727T-3302E_SN.STEP
6.00 x 1.75 x 4.90 mm
