lehungthinh02/KLTN_Data/Hardware/Model3D/CAPC1206 v2.step

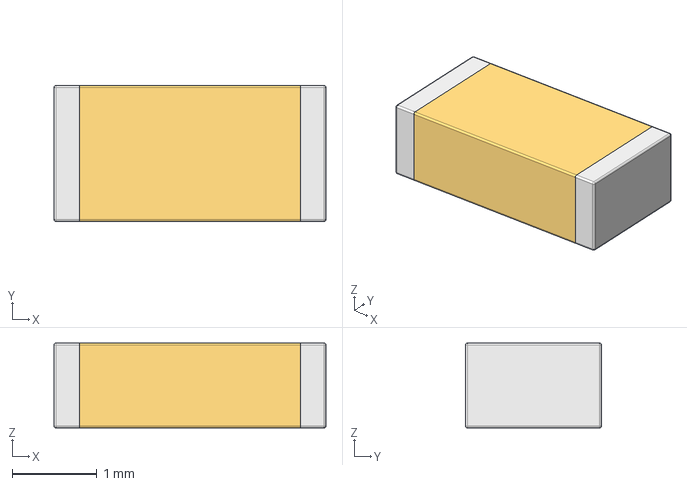
[picture p145: CAD file, 2024-04-12]
Hardware/Model3D/CAPC1206 v2.step
3.20 x 1.60 x 1.00 mm
