lehungthinh02/KLTN_Data/Hardware/Model3D/OptoSO16.step

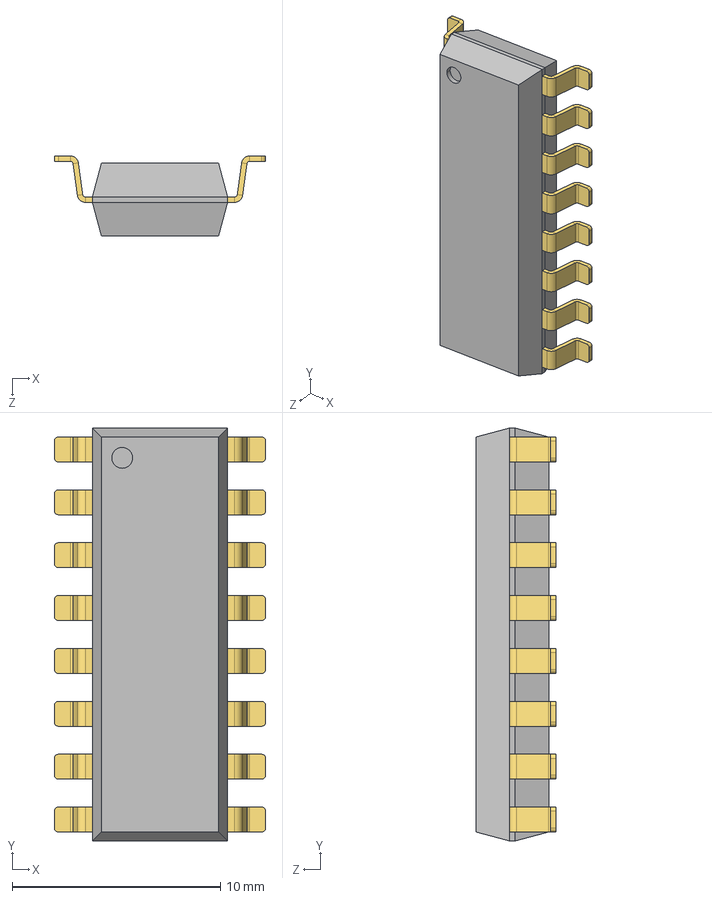
[picture p146: CAD file, 2024-04-12]
Hardware/Model3D/OptoSO16.step
10.2 x 19.8 x 3.85 mm
