lehungthinh02/KLTN_Data/Hardware/Model3D/LED0606_1616.step

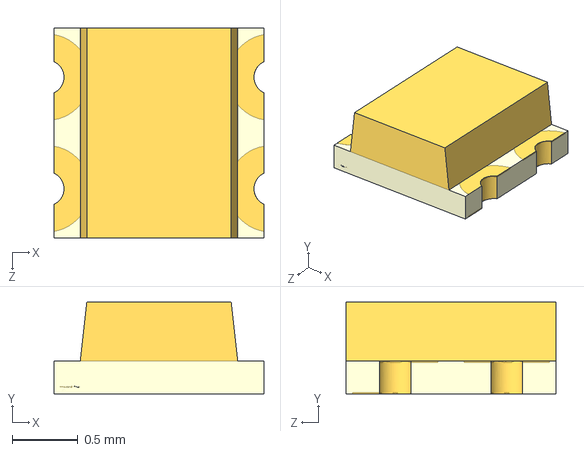
[picture p147: CAD file, 2024-04-12]
Hardware/Model3D/LED0606_1616.step
1.60 x 0.7 x 1.60 mm
