lehungthinh02/KLTN_Data/Hardware/Model3D/93LC46BT-IOT.step

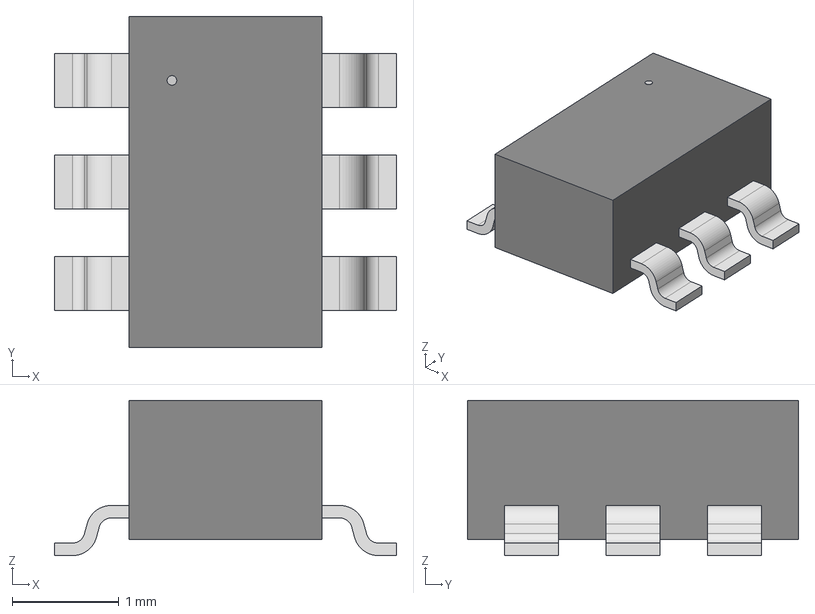
[picture p148: CAD file, 2024-04-12]
Hardware/Model3D/93LC46BT-IOT.step
3.20 x 3.10 x 1.45 mm
