lehungthinh02/KLTN_Data/Hardware/Model3D/QFN36 6x6.step

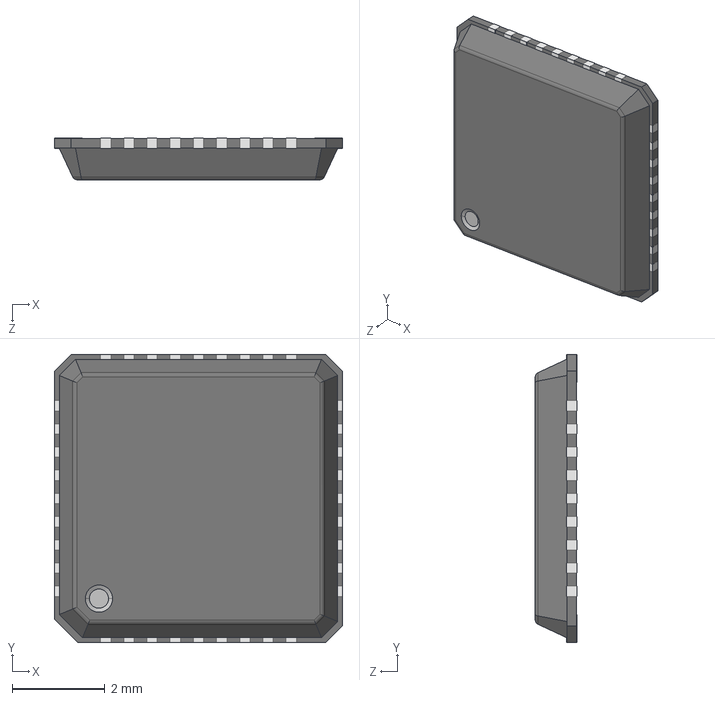
[picture p149: CAD file, 2024-04-12]
Hardware/Model3D/QFN36 6x6.step
6.21 x 6.21 x 0.895 mm
