lehungthinh02/KLTN_Data/Hardware/Model3D/B072VWVN-RC.STEP

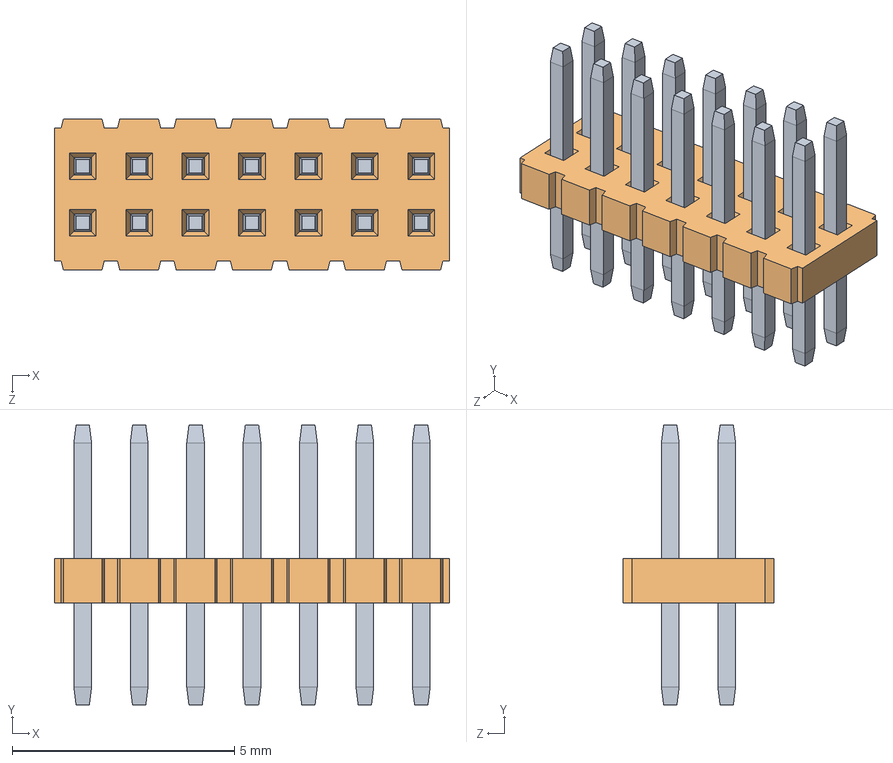
[picture p150: CAD file, 2024-04-12]
Hardware/Model3D/B072VWVN-RC.STEP
8.89 x 6.30 x 3.40 mm
