lehungthinh02/KLTN_Data/Hardware/Model3D/WCSP4F_z90.stp

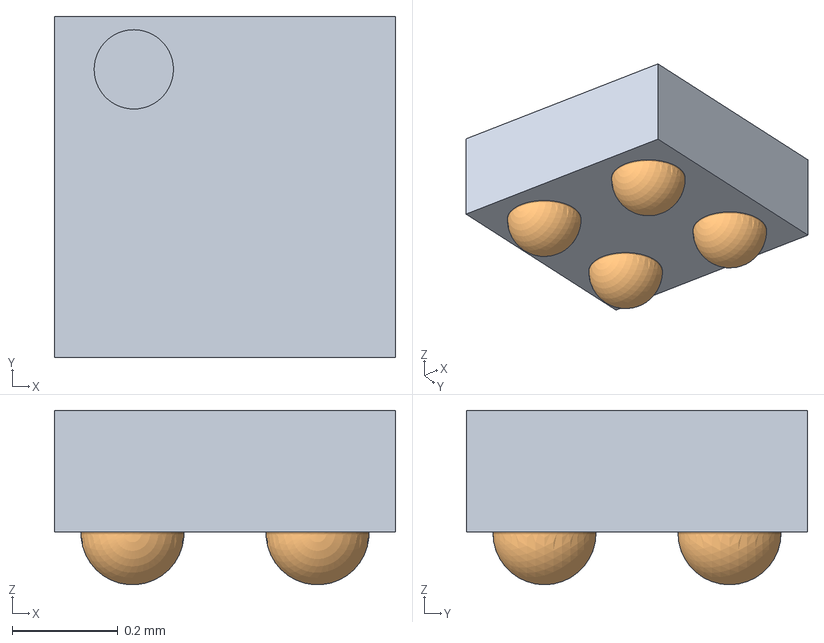
[picture p152: CAD file, 2024-04-12]
Hardware/Model3D/WCSP4F_z90.stp
0.645 x 0.645 x 0.33 mm
