lehungthinh02/KLTN_Data/Hardware/Model3D/C0805C226K9PACTU.step

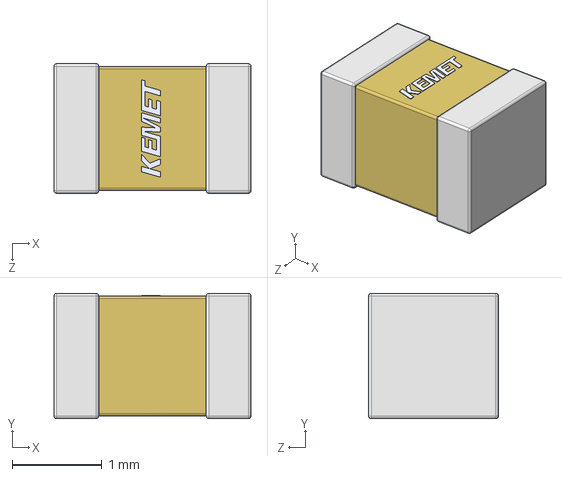
[picture p153: CAD file, 2024-04-12]
Hardware/Model3D/C0805C226K9PACTU.step
2.20 x 1.40 x 1.45 mm
