lehungthinh02/KLTN_Data/Hardware/Model3D/ECAP-18x51.5-LS7.5.STEP

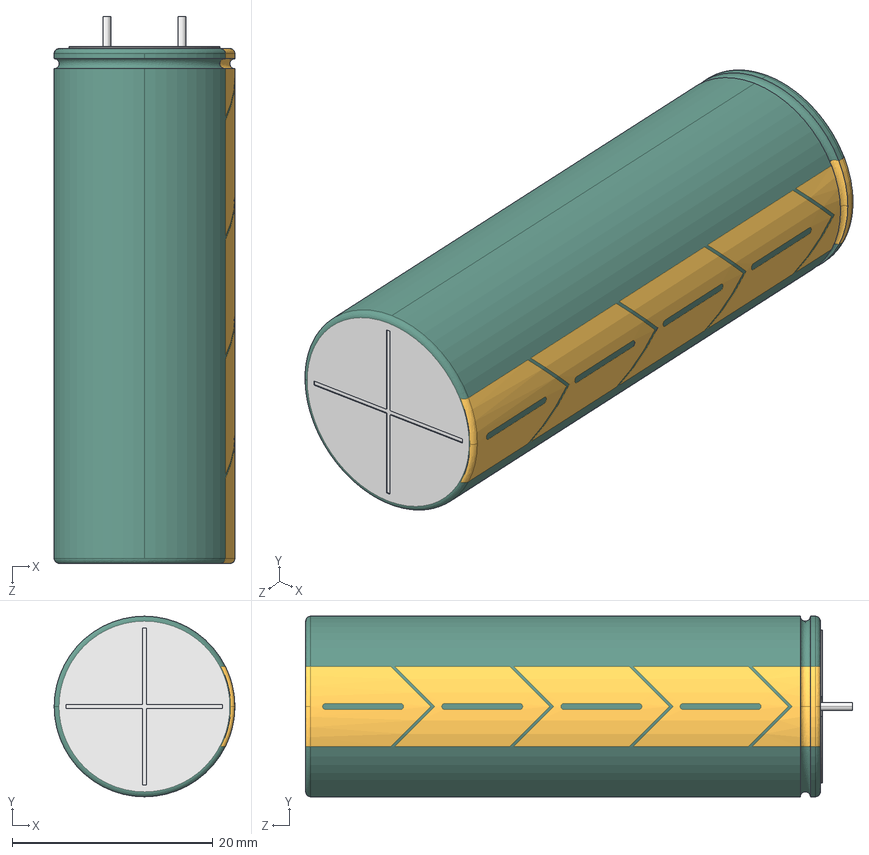
[picture p154: CAD file, 2024-04-12]
Hardware/Model3D/ECAP-18x51.5-LS7.5.STEP
18.0 x 18.0 x 54.5 mm
