lehungthinh02/KLTN_Data/Hardware/Model3D/Microchip - PICkit4.STEP

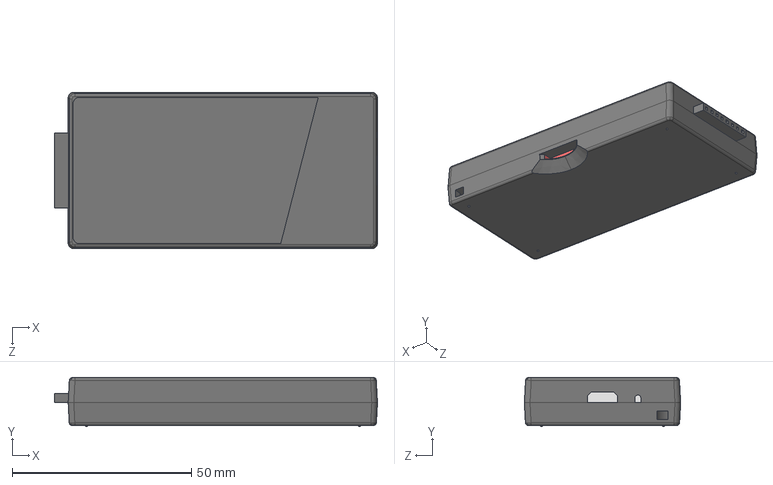
[picture p155: CAD file, 2024-04-12]
Hardware/Model3D/Microchip - PICkit4.STEP
90.2 x 13.8 x 43.6 mm
