lehungthinh02/KLTN_Data/Hardware/Model3D/09VR1B20F.stp

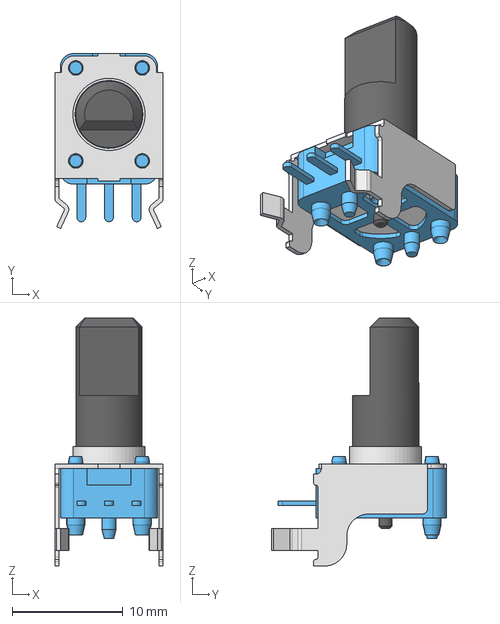
[picture p156: CAD file, 2024-04-12]
Hardware/Model3D/09VR1B20F.stp
9.80 x 15.8 x 22.4 mm
