lehungthinh02/KLTN_Data/Hardware/Model3D/QFN50P250X250X80-15N.step

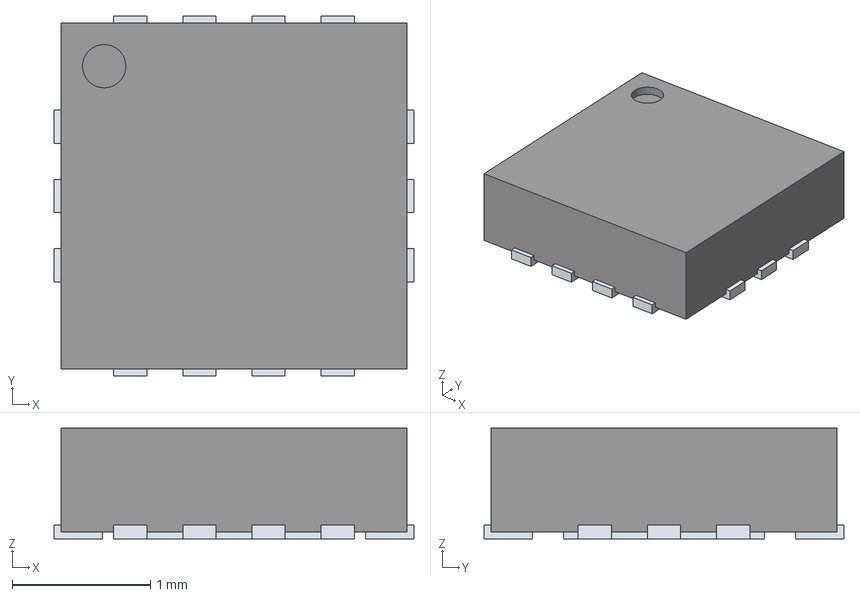
[picture p157: CAD file, 2024-04-12]
Hardware/Model3D/QFN50P250X250X80-15N.step
2.60 x 2.60 x 0.8 mm
ThermalPin
PinsArrayLR
PinsArrayTB
