lehungthinh02/KLTN_Data/Hardware/Production/Schematic/WeatherStation.pdf

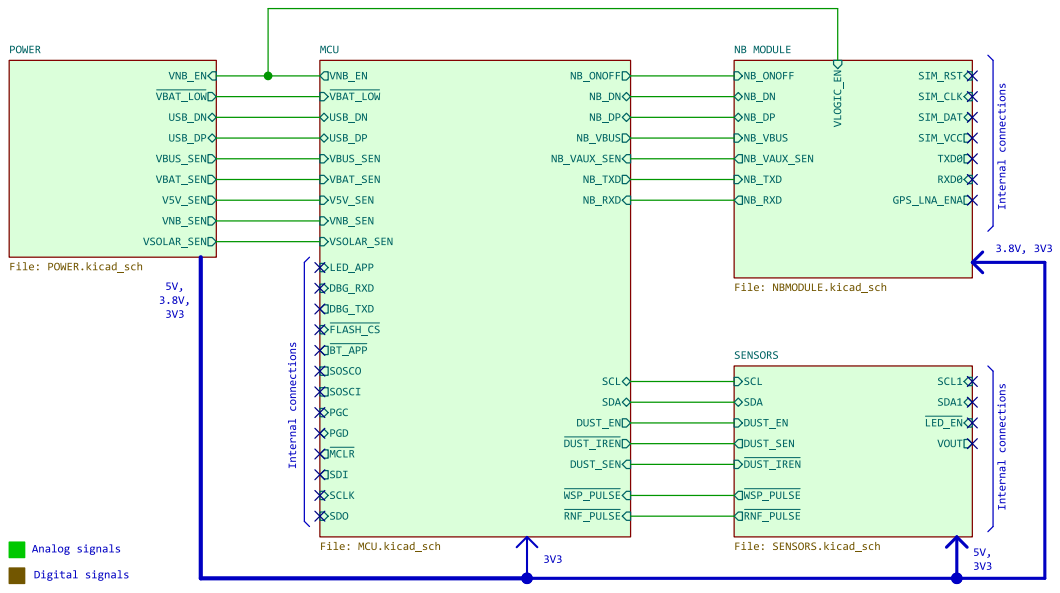
[picture p158: page 1]

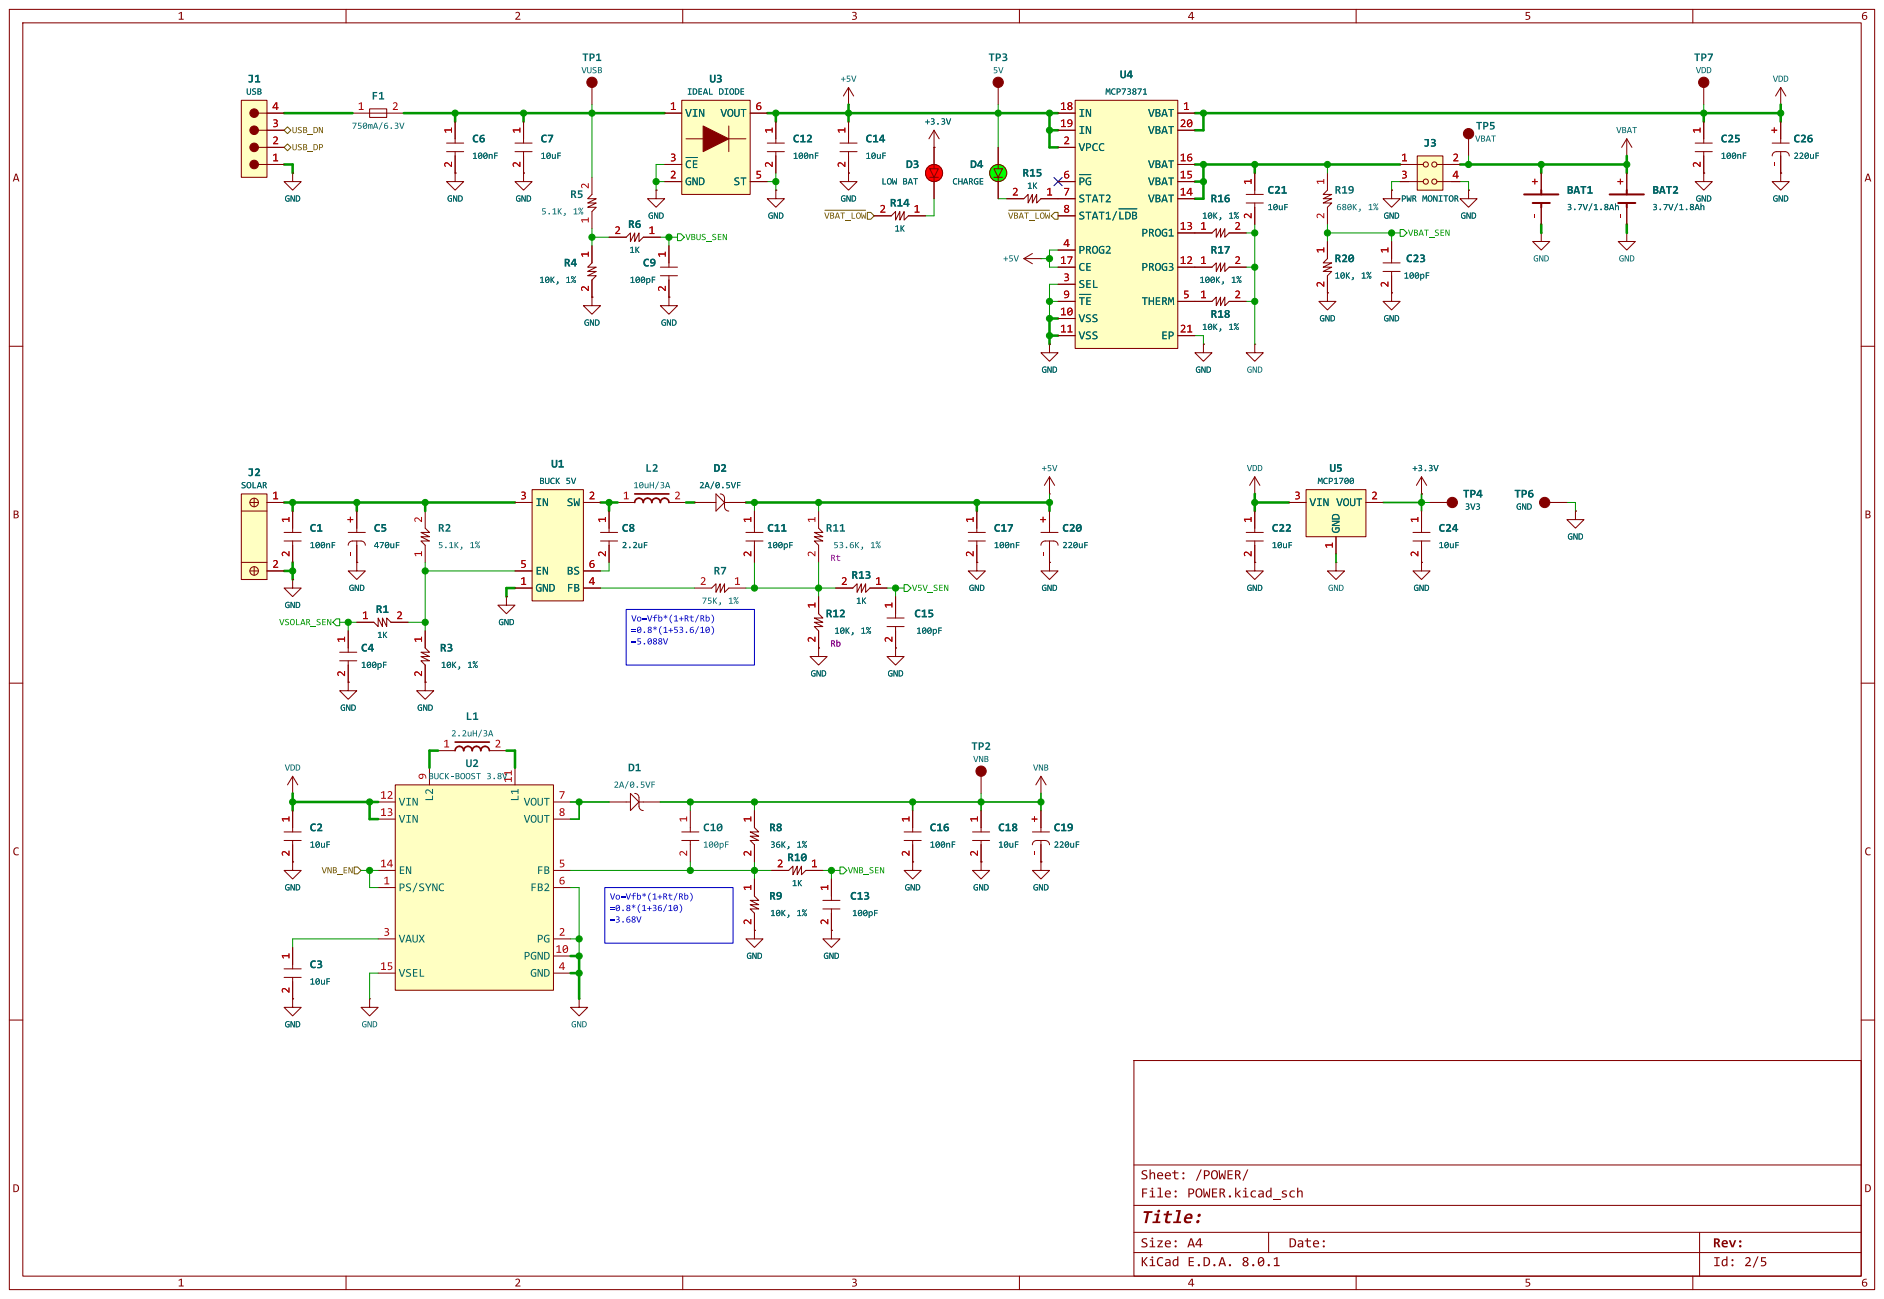
[picture p159: page 2]

Vo=Vfb*(1+Rt/Rb) =0.8*(1+53.6/10) =5.088V J2
SOLAR

1 VOUT 2 VIN 3 TP6 GND GND

Vo=Vfb*(1+Rt/Rb) =0.8*(1+36/10) =3.68V

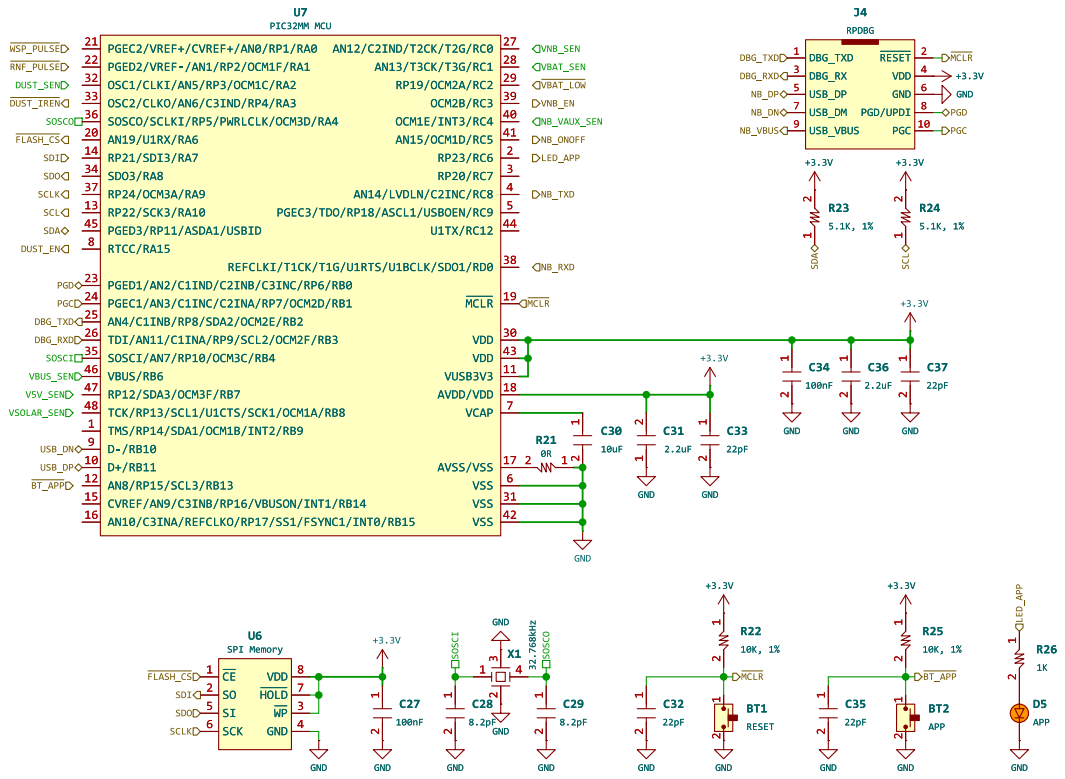
[picture p160: page 3]

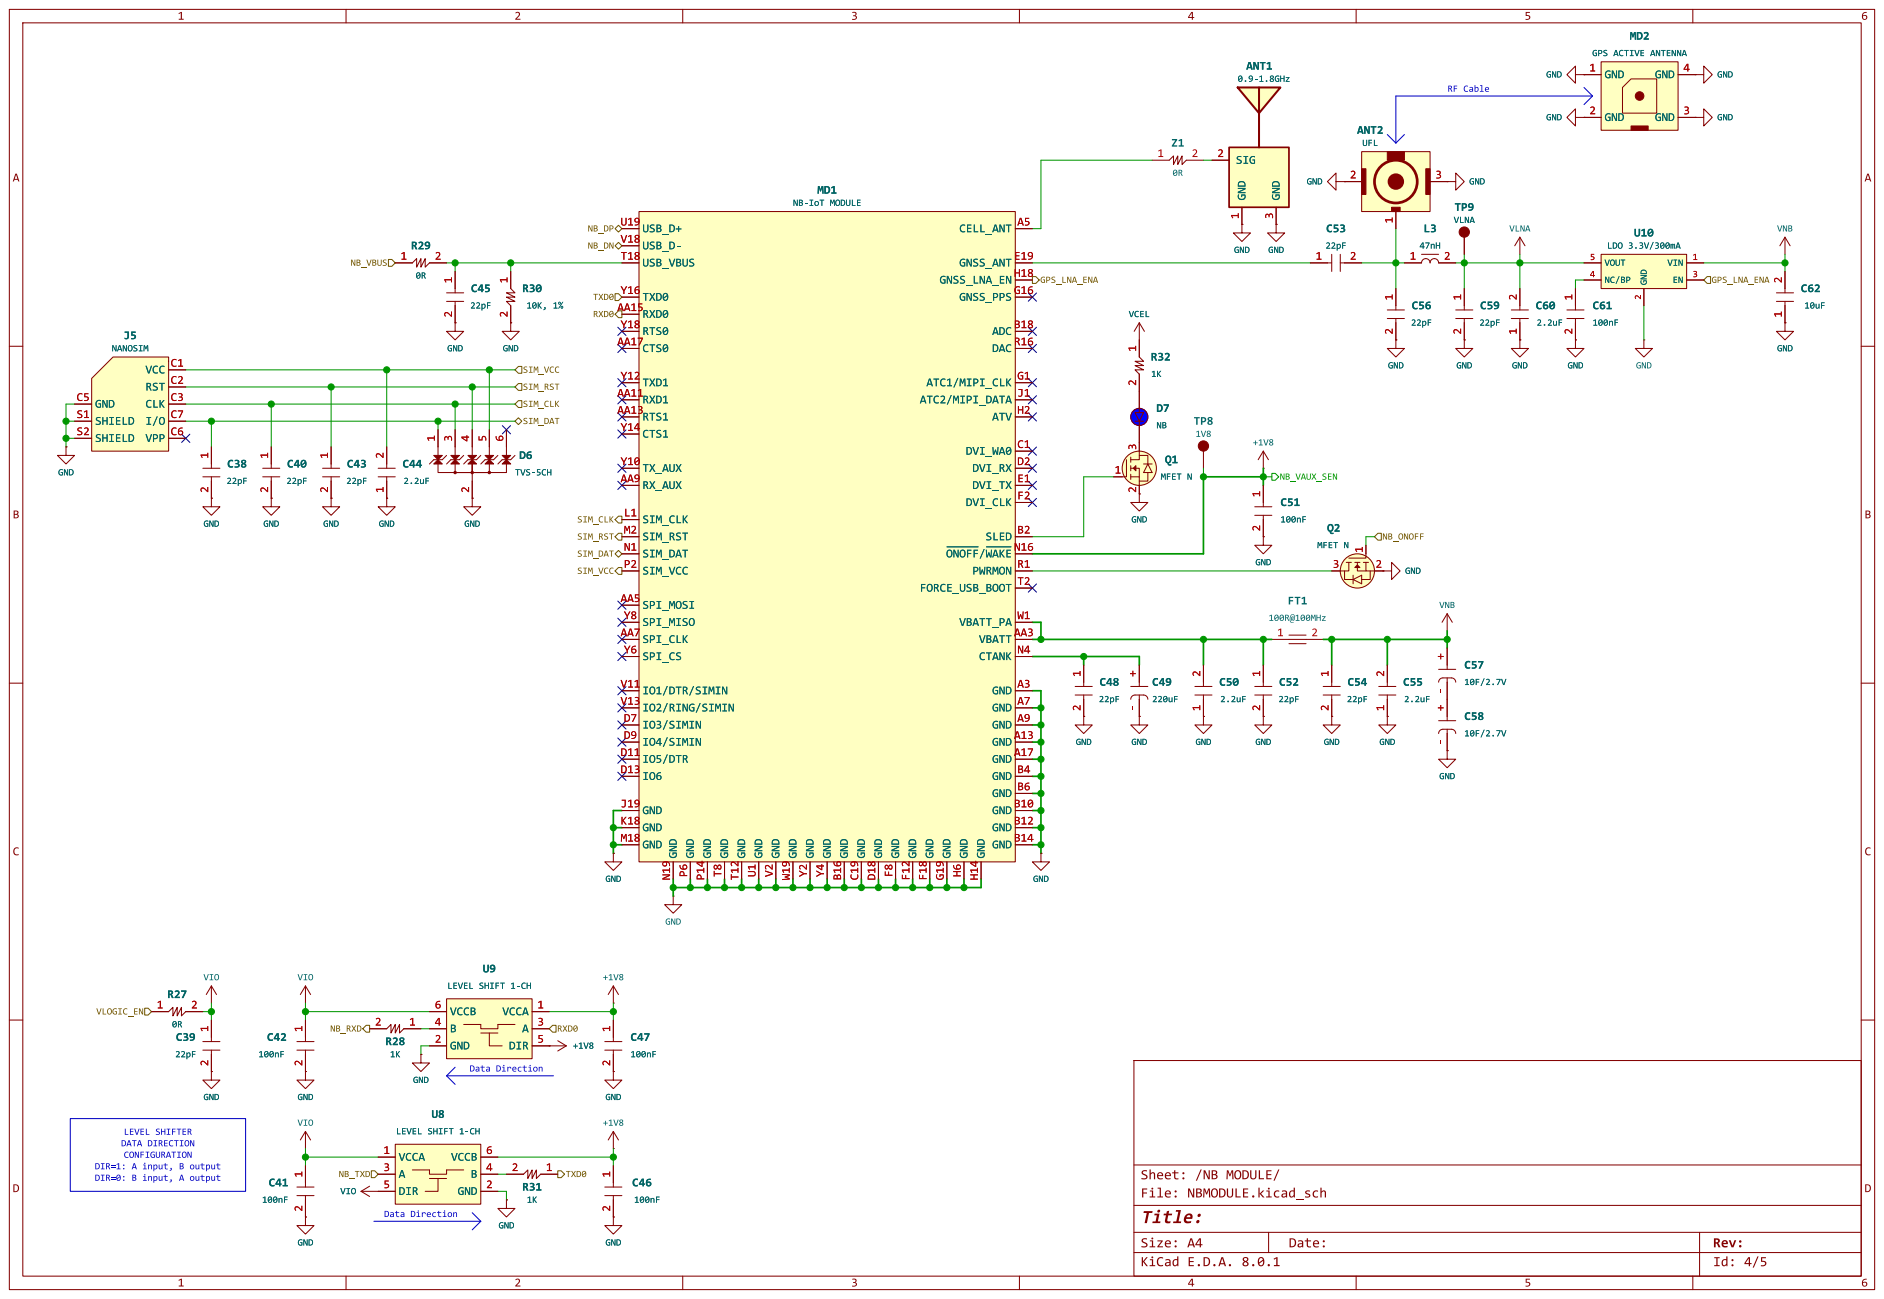
[picture p161: page 4]

3 GND GND GND GND GND C56

2 EN 3 NC/BP 4 VOUT 5 U10
LDO3.3V/300mA

2 EN 3 NC/BP 4 VOUT 5

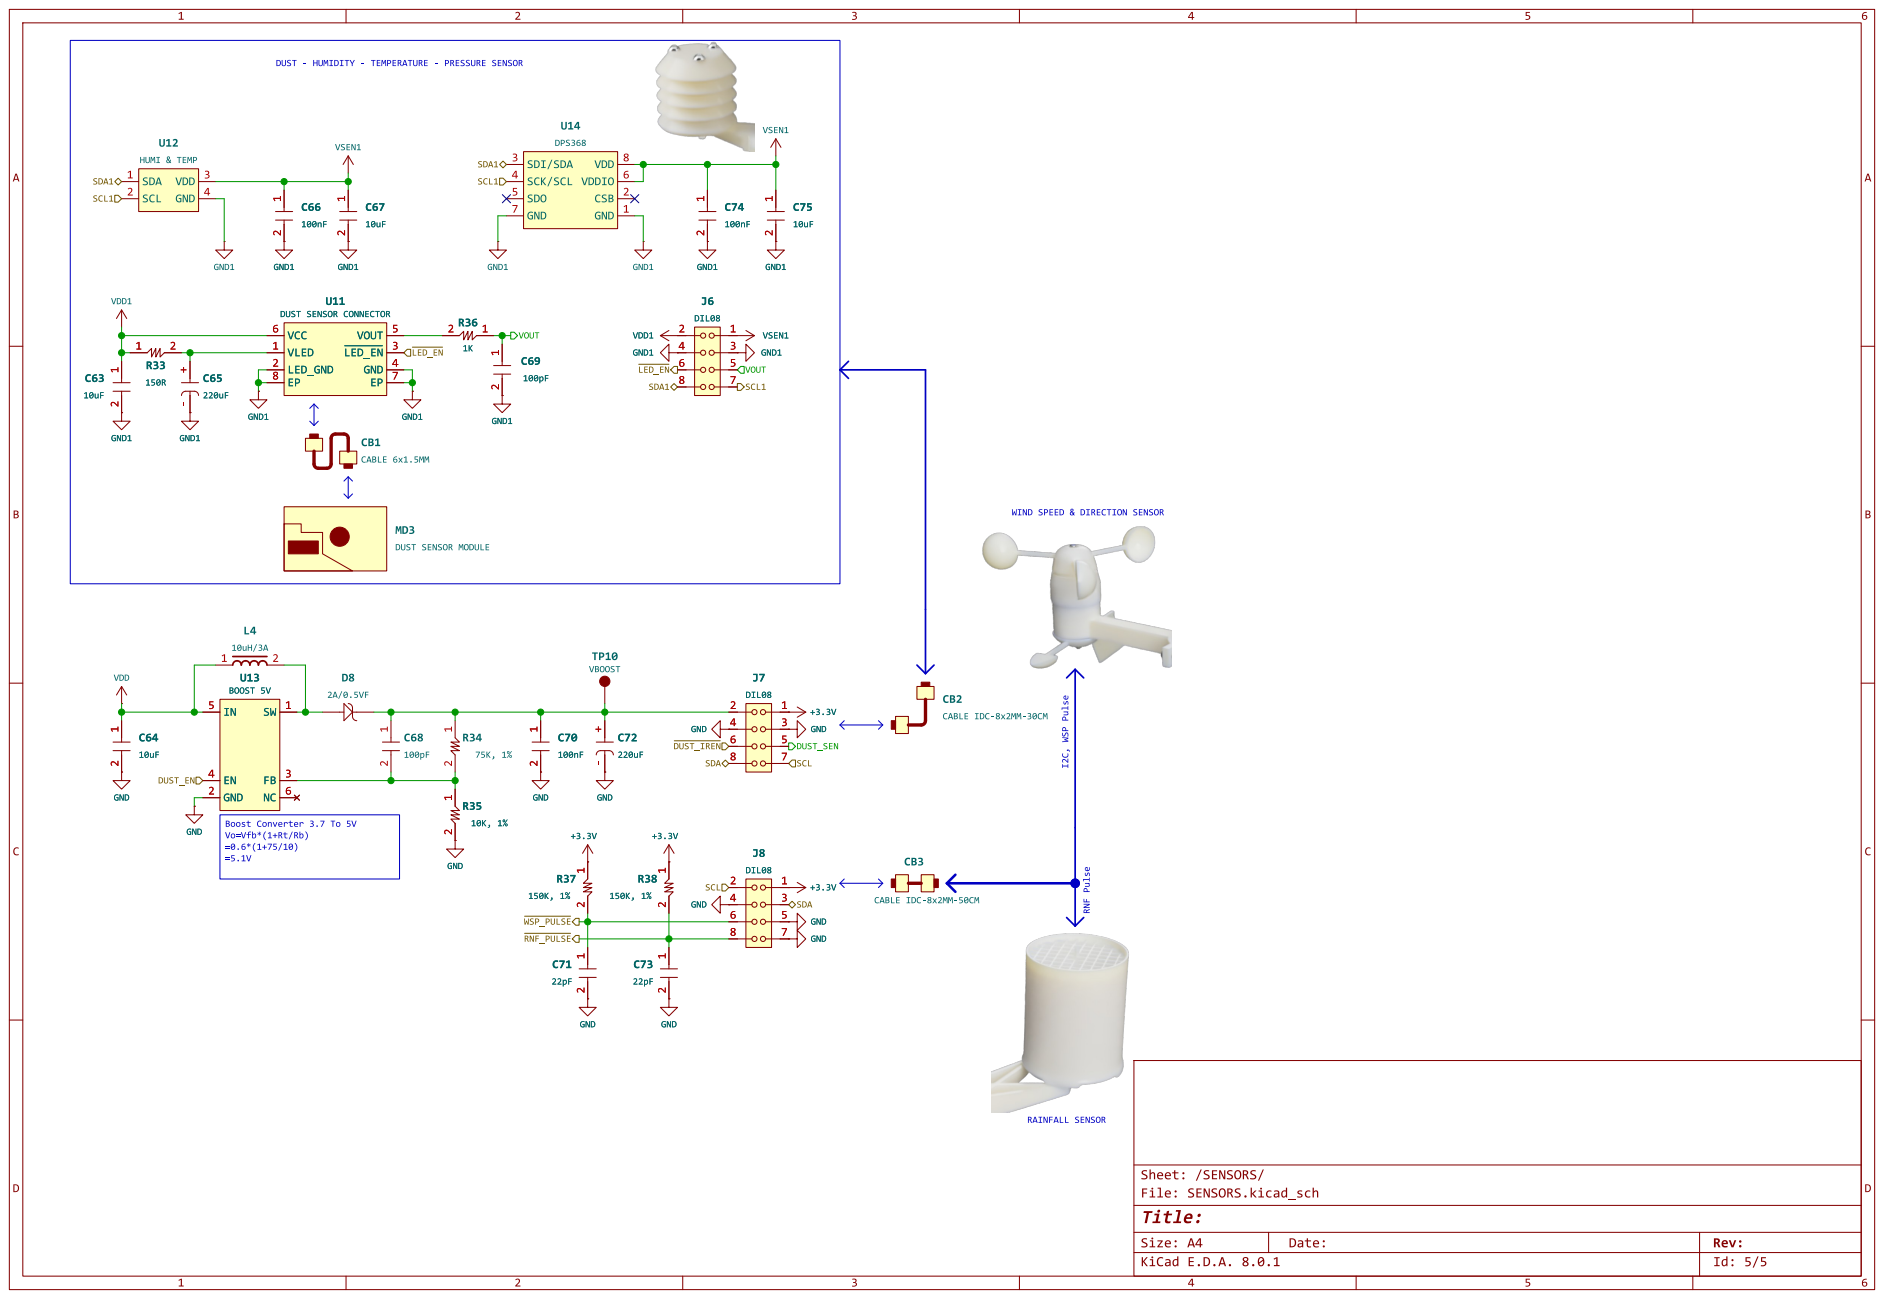
[picture p162: page 5]
